nsobczak/CoupeDeFrance/Module Alimentation/Carte_d_alimentation/ReadMe.txt

Alimentation Robot coupe de France : 
100*100 mm
1 exemplaire
Jean-Marc@isen-lille.fr
Arthur.duytschaever@isen.yncrea.fr
