nsobczak/CoupeDeFrance/Module Cerveau/I2C/README.md

# I2C

Protocole de communication entre les différents arduinos.

i2cCommunication.zip est la librairie que nous avons créée.

## i2cCommunication

Il s'agit du dossier qui contient les fichiers de la bibliothèque que nous avons créée pour gérer la communication i2c.

## Tests

Il s'agit du dossier contenant les fichiers ayant servi à réaliser les différents test de la communication entre les arduino réalisée en i2c.
