nsobczak/CoupeDeFrance/Présentations/Présentation 1er semestre/README.md

# Présentation 1er semestre

Dossier contenant les fichiers ayant servi pour notre présentation du 1er semestre.
