nsobczak/CoupeDeFrance/Module Alimentation/Carte_d_alimentation/README.md

# Module alim

Il s'agit du dossier destiné à accueillir tout ce qui concerne la carte d'alimentation.
