nsobczak/CoupeDeFrance/Module Moteur/Software/Asservissement/README.md

# Asservissment

**TODO** :
- Définir ce à quoi sert chaque code
- Supprimer les codes inutiles
