nsobczak/CoupeDeFrance/Module Cerveau/Artificial Intelligence/Ecran/README.md

# Ecran

Il s'agit du dossier du code pour controler l'écran.

## Dossiers

- "BotMenu" est le dossier dans lequel est conservé le code principal de l'écran.
- "Ecran_test" est le dossier dans lequel nous faisons nos tests de l'écran.

## Bibliothèques

### U8glib
Il s'agit de la bibliothèque permettant de controller l'écran.

### m2tklib
Il s'agit de la bibliothèque permettant de controller les menus de l'écran.
