nsobczak/CoupeDeFrance/Module Funny Action/Hardware/PCB_Project/Project Outputs for PCB_Project/README.txt

Coupe de France de Robotique
1 exemplaire
Jean-marc.capron@yncrea.fr
Arthur.duytschaever@isen.yncrea.fr
