nsobczak/CoupeDeFrance/Module Moteur/Software/Caractérisation des moteurs/Récupération codeuse/README.md

# Récupération codeuse

Ce programme compte le nombre de ticks des codeuses d'un des 2 moteurs et les affiche dans le port série à une fréquence fixée.
