nsobczak/CoupeDeFrance/Module Moteur/Software/Archives/README.md

# Archives

This folder contains old programs. These are the one other team used. We may use them to help us.

## CodeOriginal
Il s'agit du code initialement écrit pour le spark core.

## monMain
Il s'agit du code adapté pour un arduino due.
