nsobczak/CoupeDeFrance/Documentation/arduino_emoji.png

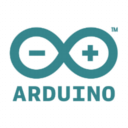
Documentation/arduino_emoji.png
