nsobczak/CoupeDeFrance/Documentation/html/_bot_menu_8cpp__incl.png

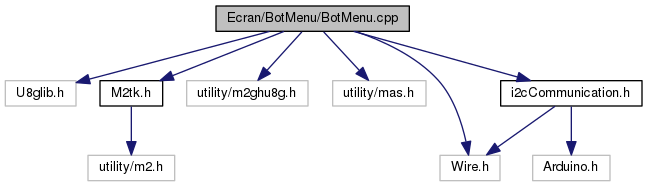
Documentation/html/_bot_menu_8cpp__incl.png
