nsobczak/CoupeDeFrance/Documentation/html/_capteur___i_r__detection__position_8cpp__incl.png

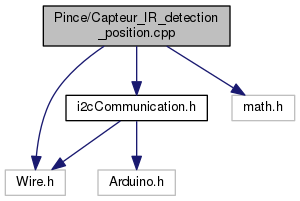
Documentation/html/_capteur___i_r__detection__position_8cpp__incl.png
