nsobczak/CoupeDeFrance/Documentation/html/_ecran_8cpp__incl.png

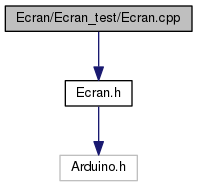
Documentation/html/_ecran_8cpp__incl.png
