nsobczak/CoupeDeFrance/Documentation/html/_ecran_8h__dep__incl.png

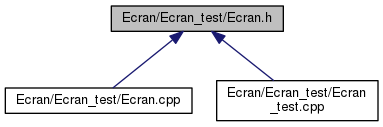
Documentation/html/_ecran_8h__dep__incl.png
