nsobczak/CoupeDeFrance/Documentation/html/_m2tk_8cpp__incl.png

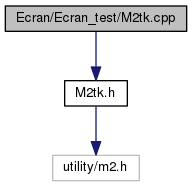
Documentation/html/_m2tk_8cpp__incl.png
