nsobczak/CoupeDeFrance/Documentation/html/_moteur__deplacement_8cpp__incl.png

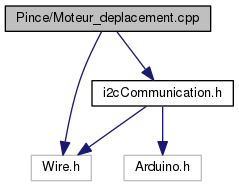
Documentation/html/_moteur__deplacement_8cpp__incl.png
