nsobczak/CoupeDeFrance/Documentation/html/_p_i_d_8cpp__incl.png

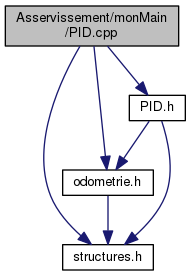
Documentation/html/_p_i_d_8cpp__incl.png
