nsobczak/CoupeDeFrance/Documentation/html/_p_i_d_8h__dep__incl.png

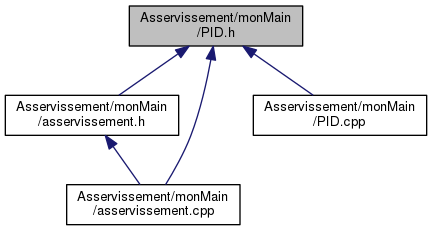
Documentation/html/_p_i_d_8h__dep__incl.png
