nsobczak/CoupeDeFrance/Documentation/html/_p_i_d_8h__incl.png

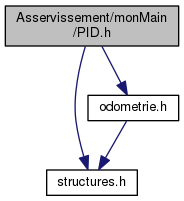
Documentation/html/_p_i_d_8h__incl.png
