nsobczak/CoupeDeFrance/Documentation/html/application_8cpp__incl.png

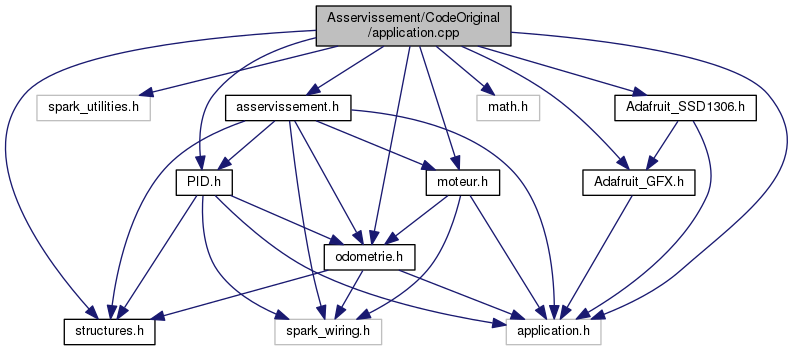
Documentation/html/application_8cpp__incl.png
