nsobczak/CoupeDeFrance/Documentation/html/asservissement_8cpp__incl.png

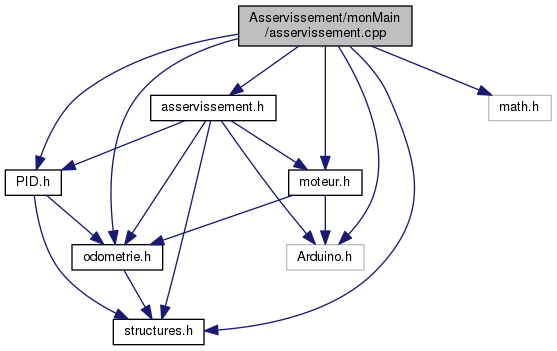
Documentation/html/asservissement_8cpp__incl.png
