nsobczak/CoupeDeFrance/Documentation/html/asservissement_8h__dep__incl.png

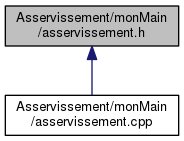
Documentation/html/asservissement_8h__dep__incl.png
