nsobczak/CoupeDeFrance/Documentation/html/asservissement_8h__incl.png

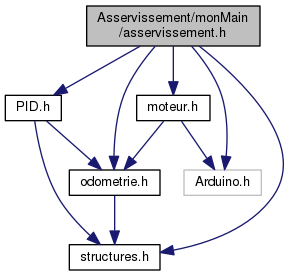
Documentation/html/asservissement_8h__incl.png
