nsobczak/CoupeDeFrance/Documentation/html/class_adafruit___g_f_x__inherit__graph.png

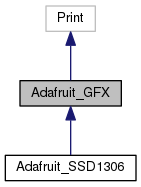
Documentation/html/class_adafruit___g_f_x__inherit__graph.png
