nsobczak/CoupeDeFrance/Documentation/html/dir_7feffd230ef17a4d3f6232c08444e68c_dep.png

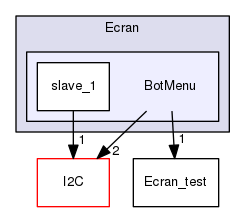
Documentation/html/dir_7feffd230ef17a4d3f6232c08444e68c_dep.png
