nsobczak/CoupeDeFrance/Documentation/html/dir_239d87ce9101b63f8d944565a49246da_dep.png

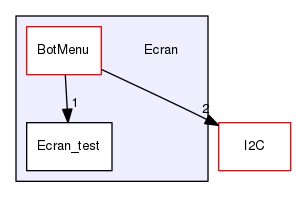
Documentation/html/dir_239d87ce9101b63f8d944565a49246da_dep.png
