nsobczak/CoupeDeFrance/Documentation/html/dir_b54d3ecc02a1dadce9e3ca1df9bb6ecc_dep.png

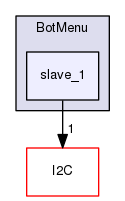
Documentation/html/dir_b54d3ecc02a1dadce9e3ca1df9bb6ecc_dep.png
