nsobczak/CoupeDeFrance/Documentation/html/i2c_communication_8cpp__incl.png

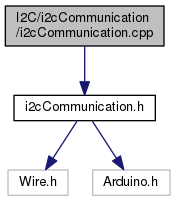
Documentation/html/i2c_communication_8cpp__incl.png
