nsobczak/CoupeDeFrance/Documentation/html/i2c_communication_8h__incl.png

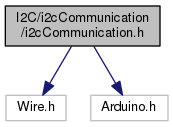
Documentation/html/i2c_communication_8h__incl.png
