nsobczak/CoupeDeFrance/Documentation/html/mon_main_8cpp__incl.png

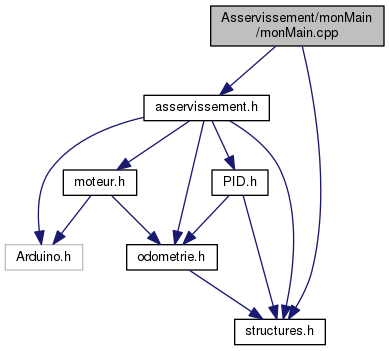
Documentation/html/mon_main_8cpp__incl.png
