nsobczak/CoupeDeFrance/Documentation/html/moteur_8cpp__incl.png

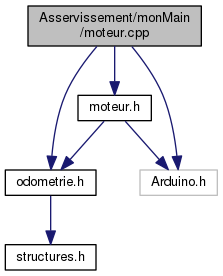
Documentation/html/moteur_8cpp__incl.png
