nsobczak/CoupeDeFrance/Documentation/html/moteur_8h__incl.png

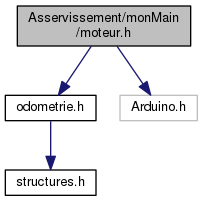
Documentation/html/moteur_8h__incl.png
