nsobczak/CoupeDeFrance/Documentation/html/newlib__stubs_8cpp__incl.png

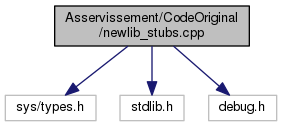
Documentation/html/newlib__stubs_8cpp__incl.png
