nsobczak/CoupeDeFrance/Documentation/html/odometrie_8cpp__incl.png

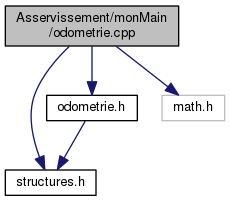
Documentation/html/odometrie_8cpp__incl.png
