nsobczak/CoupeDeFrance/Documentation/html/odometrie_8h__dep__incl.png

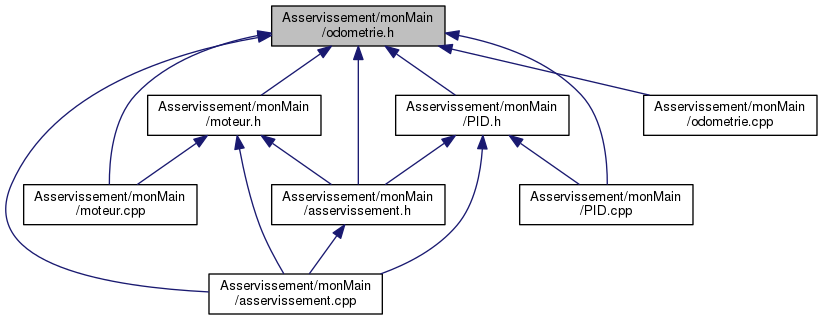
Documentation/html/odometrie_8h__dep__incl.png
