nsobczak/CoupeDeFrance/Documentation/html/odometrie_8h__incl.png

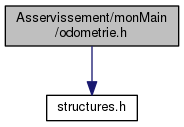
Documentation/html/odometrie_8h__incl.png
