nsobczak/CoupeDeFrance/Documentation/html/slave__1_8cpp__incl.png

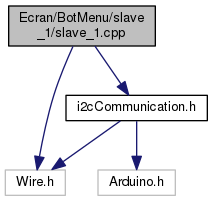
Documentation/html/slave__1_8cpp__incl.png
