nsobczak/CoupeDeFrance/Documentation/html/structures_8h__dep__incl.png

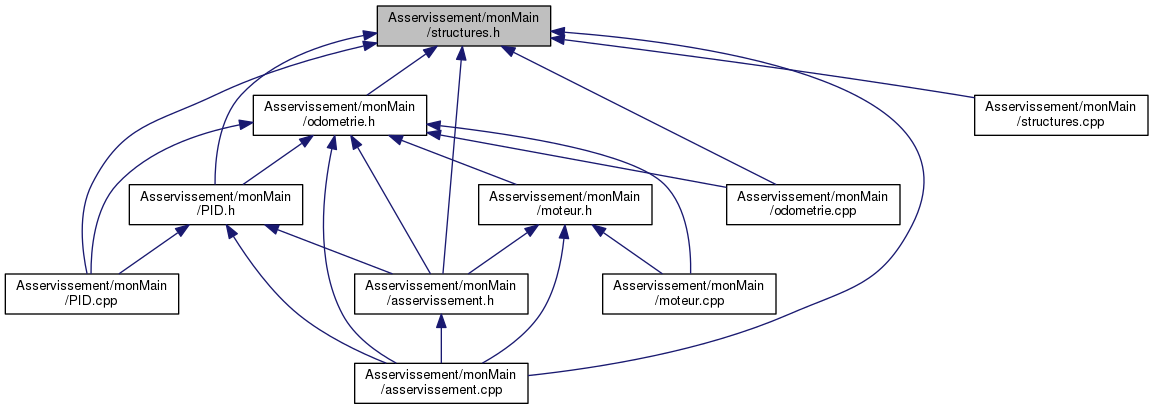
Documentation/html/structures_8h__dep__incl.png
