nsobczak/CoupeDeFrance/Documentation/html/usb__desc_8cpp__incl.png

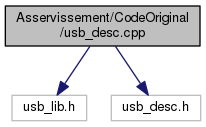
Documentation/html/usb__desc_8cpp__incl.png
