nsobczak/CoupeDeFrance/Documentation/html/usb__istr_8cpp__incl.png

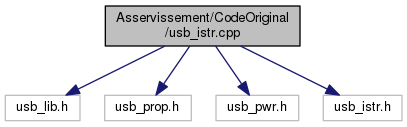
Documentation/html/usb__istr_8cpp__incl.png
