nsobczak/CoupeDeFrance/Documentation/html/wifi__credentials__reader_8cpp__incl.png

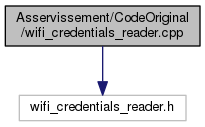
Documentation/html/wifi__credentials__reader_8cpp__incl.png
