nsobczak/CoupeDeFrance/Documentation/schéma global.png

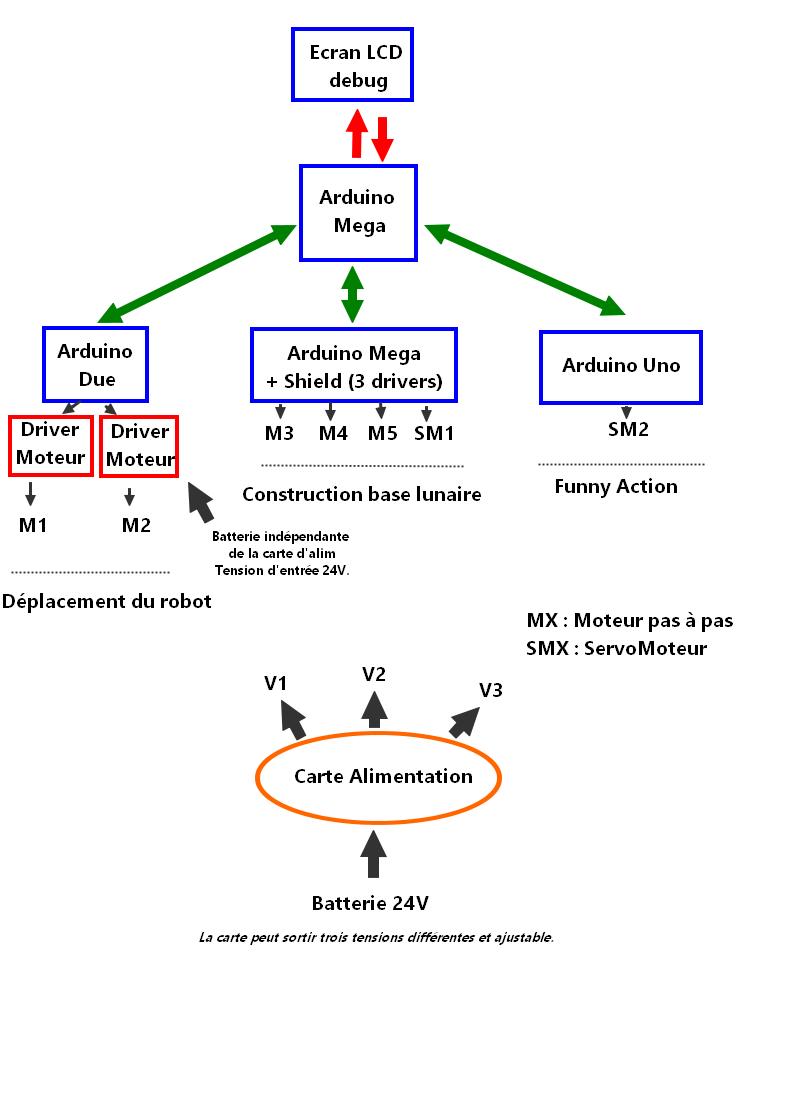
Documentation/schéma global.png
