nsobczak/CoupeDeFrance/Module Cerveau/Artificial Intelligence/AI_uml/AI_UML.png

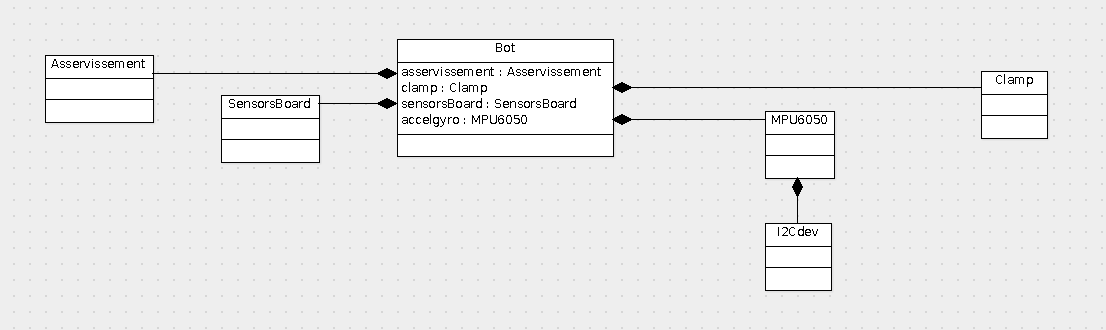
Module Cerveau/Artificial Intelligence/AI_uml/AI_UML.png
