nsobczak/CoupeDeFrance/Module Cerveau/Artificial Intelligence/Menu_Plans/Menu Plans.png

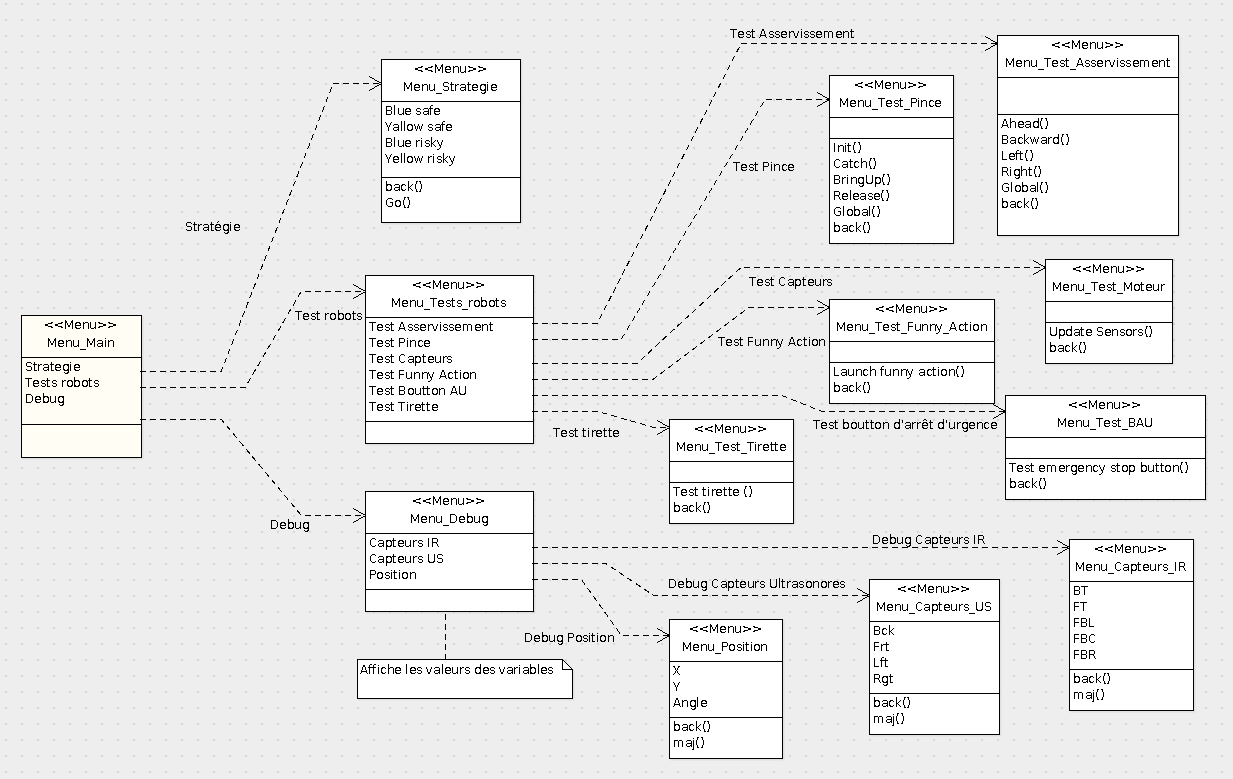
Module Cerveau/Artificial Intelligence/Menu_Plans/Menu Plans.png
