nsobczak/CoupeDeFrance/Média/Funny action (2).JPG

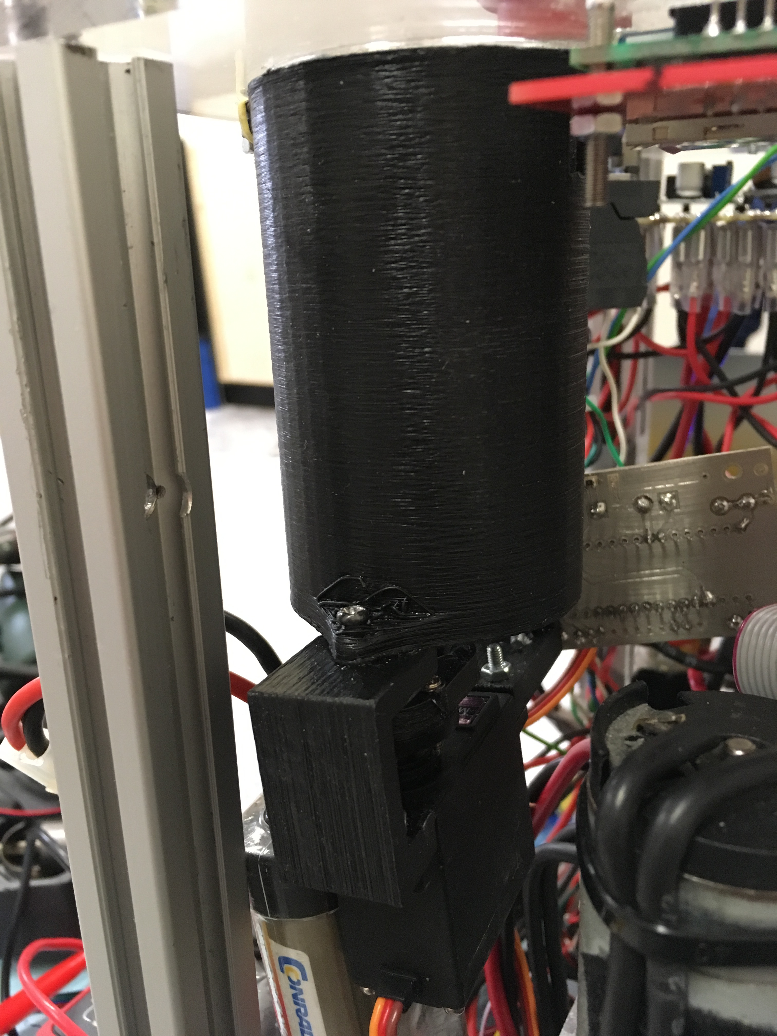
Média/Funny action (2).JPG
