nsobczak/CoupeDeFrance/Média/Funny action.JPG

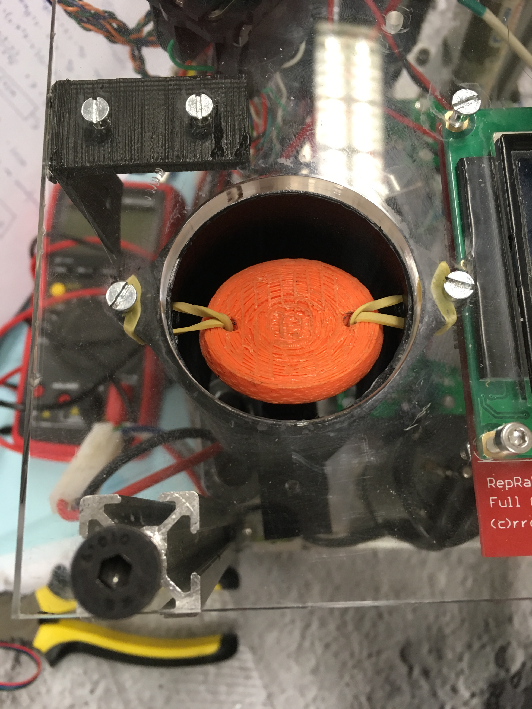
Média/Funny action.JPG
