nsobczak/CoupeDeFrance/Média/IMG_20161012_150901.jpg

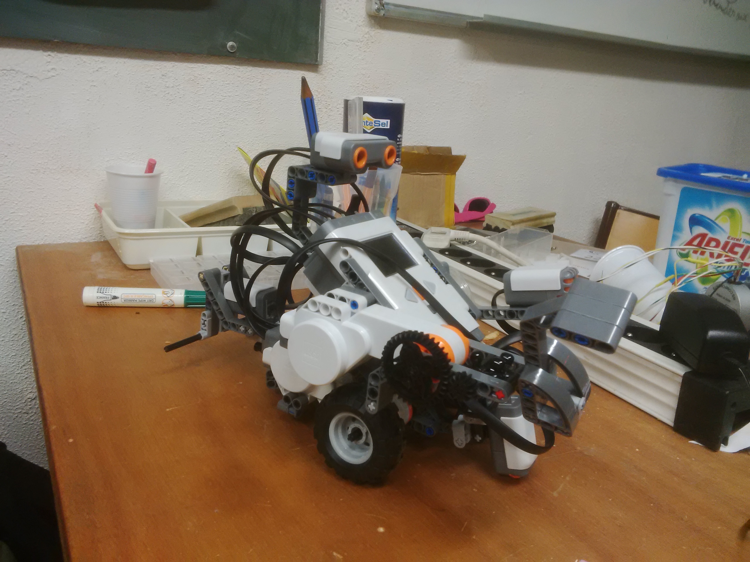
Média/IMG_20161012_150901.jpg
