nsobczak/CoupeDeFrance/Média/IMG_20161215_091232.jpg

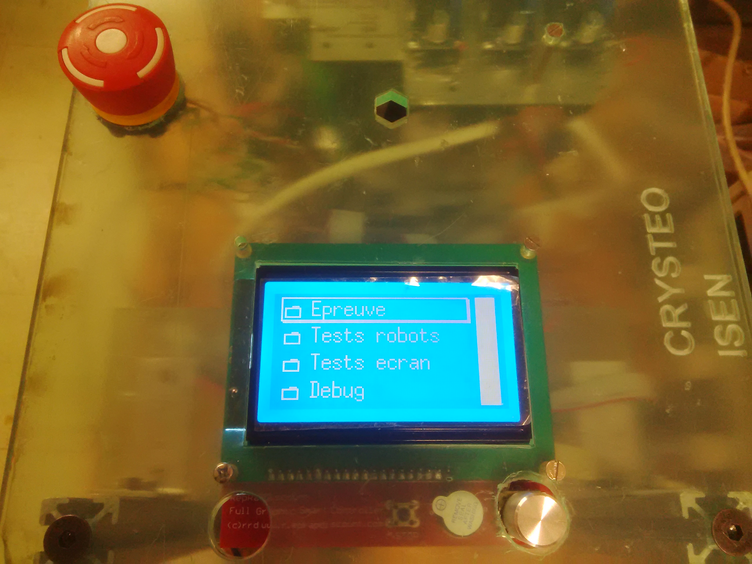
Média/IMG_20161215_091232.jpg
