nsobczak/CoupeDeFrance/Média/Photo_découpe_laser.PNG

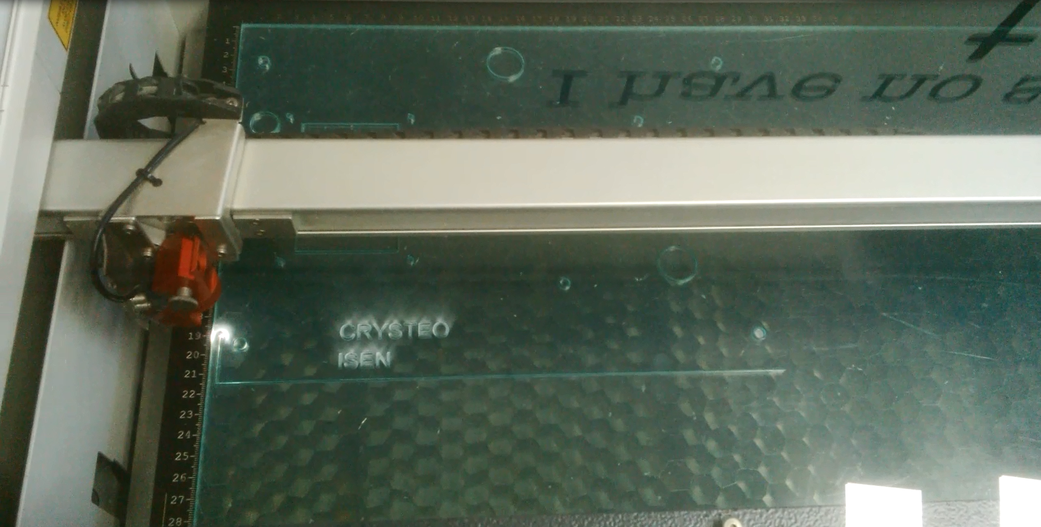
Média/Photo_découpe_laser.PNG
