nsobczak/CoupeDeFrance/Média/Photo_grand_robot_01.PNG

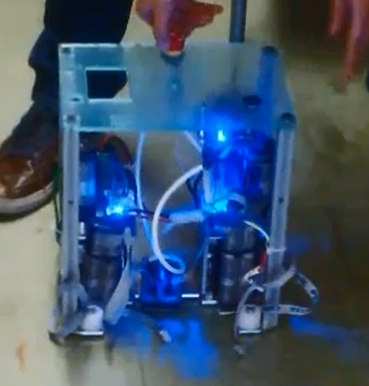
Média/Photo_grand_robot_01.PNG
