nsobczak/CoupeDeFrance/Média/Pince.JPG

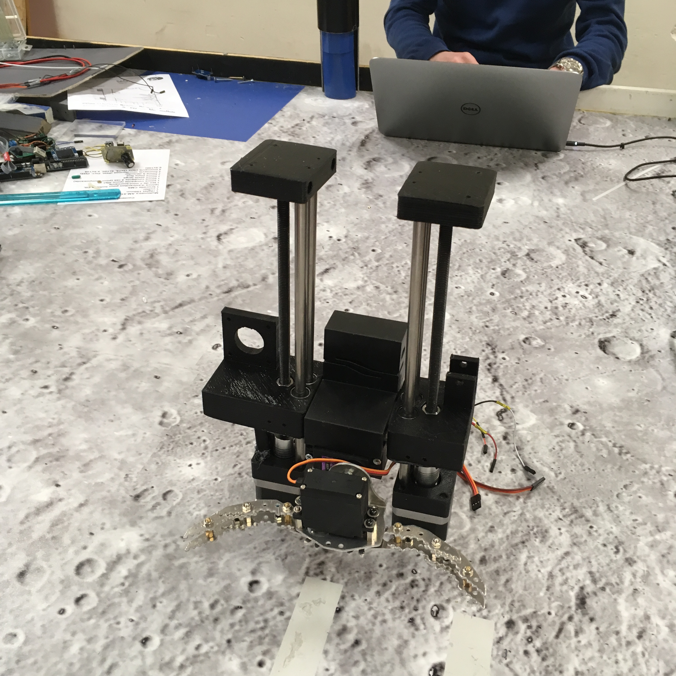
Média/Pince.JPG
