nsobczak/CoupeDeFrance/Média/Robot (2).JPG

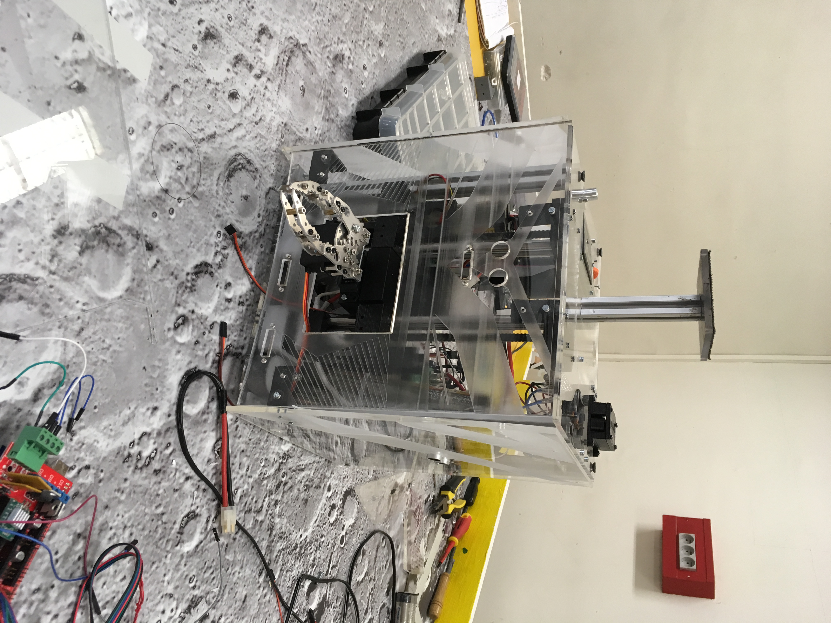
Média/Robot (2).JPG
