nsobczak/CoupeDeFrance/Média/Robot (3).JPG

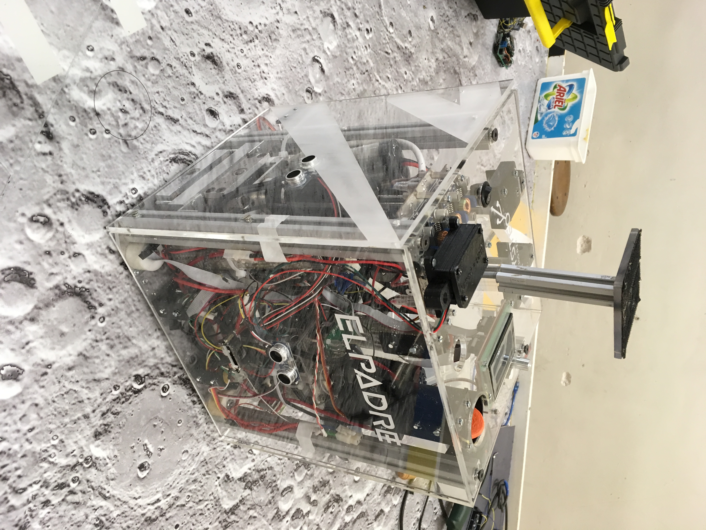
Média/Robot (3).JPG
