nsobczak/CoupeDeFrance/Média/Robot (4).JPG

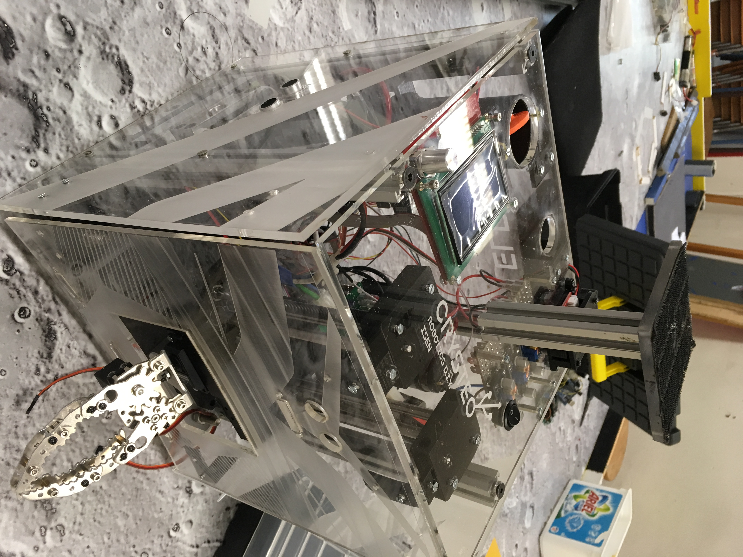
Média/Robot (4).JPG
