nsobczak/CoupeDeFrance/Média/Robot.JPG

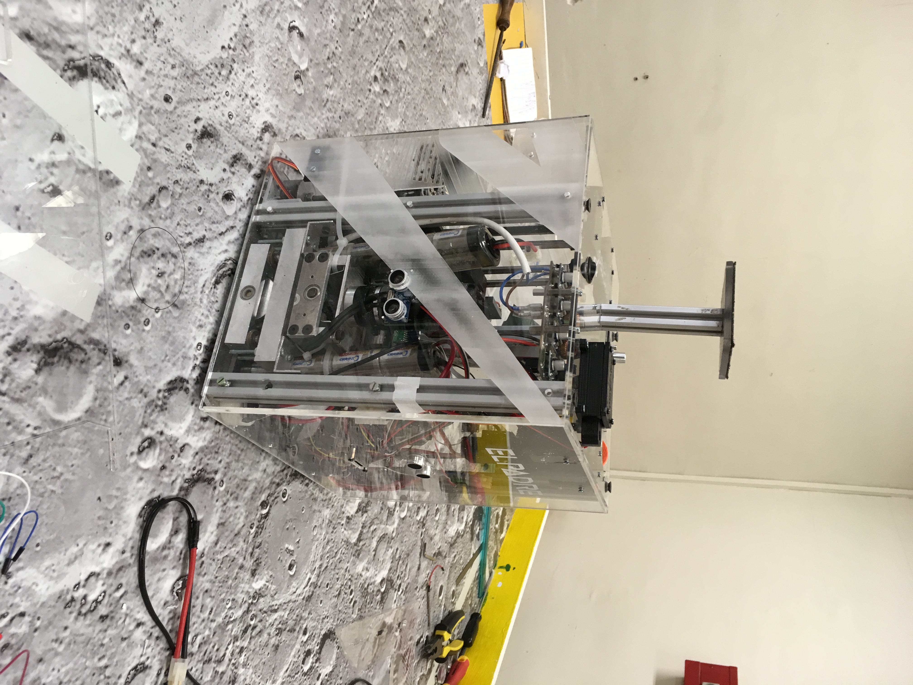
Média/Robot.JPG
