nsobczak/CoupeDeFrance/Présentations/Présentation 2eme semestre/Images/capteur-distance-ir-sharp-gp2yoa21-10cm-80cm-5.jpg

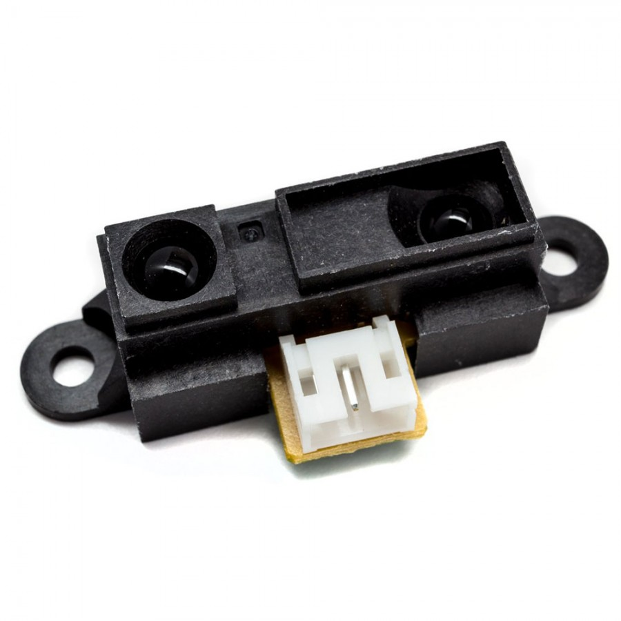
Présentations/Présentation 2eme semestre/Images/capteur-distance-ir-sharp-gp2yoa21-10cm-80cm-5.jpg
