nsobczak/CoupeDeFrance/Présentations/Présentation 2eme semestre/Images/Ecran.jpg

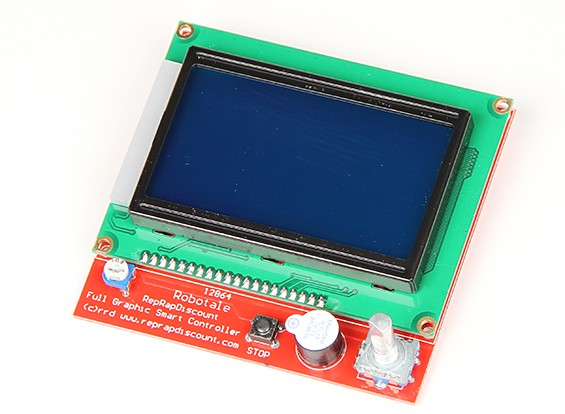
Présentations/Présentation 2eme semestre/Images/Ecran.jpg
