nsobczak/CoupeDeFrance/Présentations/Présentation 2eme semestre/Images/hc-sr04_capteur_de_distance_par_ultrason.jpg

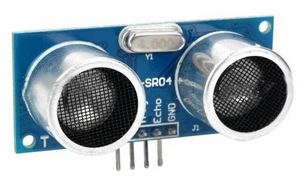
Présentations/Présentation 2eme semestre/Images/hc-sr04_capteur_de_distance_par_ultrason.jpg
