nsobczak/CoupeDeFrance/Présentations/Présentation 2eme semestre/Images/Schéma global.png

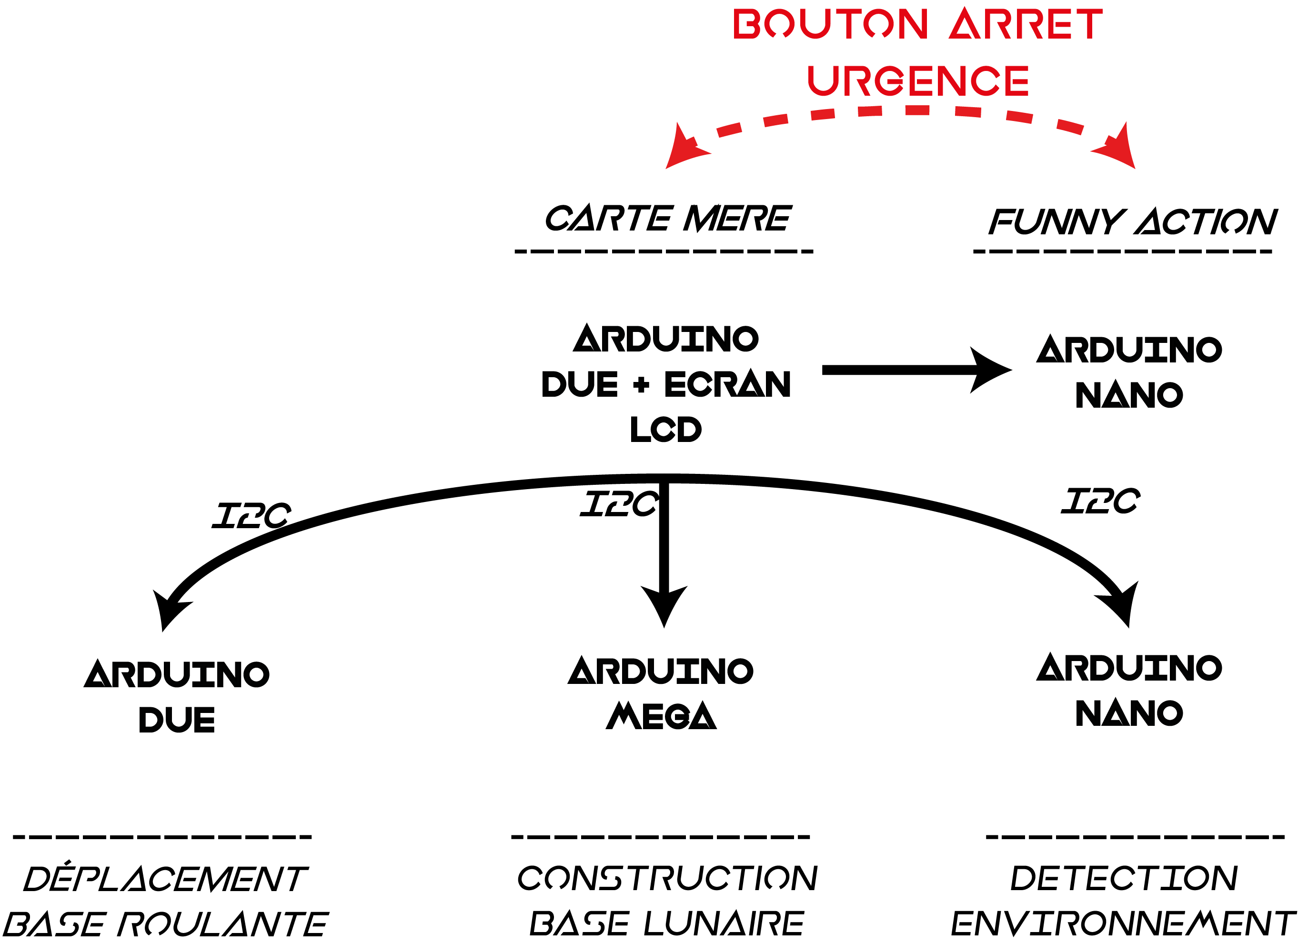
Présentations/Présentation 2eme semestre/Images/Schéma global.png
