nsobczak/CoupeDeFrance/Présentations/Présentation 2eme semestre/Images/Yncrea_BM_ISEN-Lille_Blanc-horizontal.png

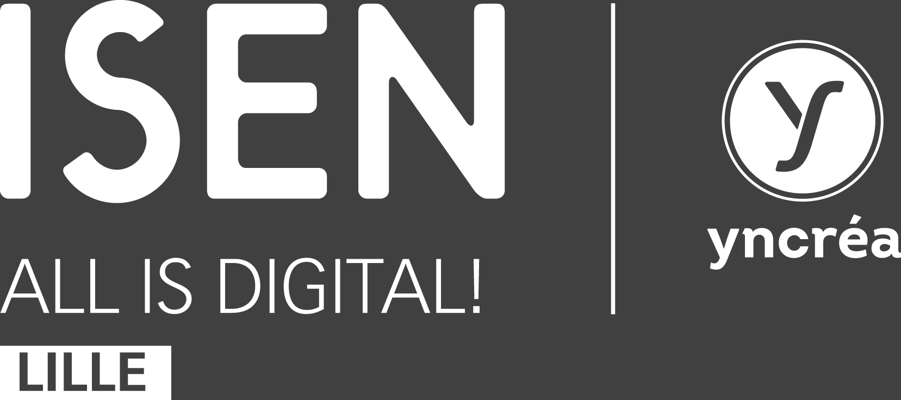
Présentations/Présentation 2eme semestre/Images/Yncrea_BM_ISEN-Lille_Blanc-horizontal.png
