nsobczak/CoupeDeFrance/Présentations/Présentation 2eme semestre/Images/Yncrea_BM_ISEN-Lille_horizontal fond transparent.png

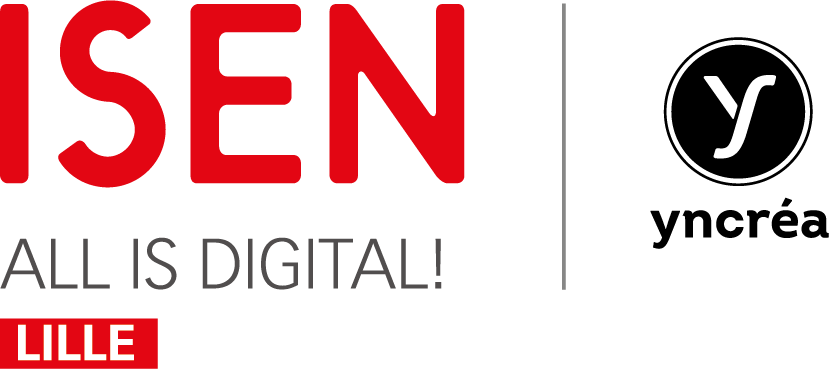
Présentations/Présentation 2eme semestre/Images/Yncrea_BM_ISEN-Lille_horizontal fond transparent.png
