nsobczak/CoupeDeFrance/Présentations/Présentation 2eme semestre/Poster/3051793895_1_16_avUZXeAR.jpg

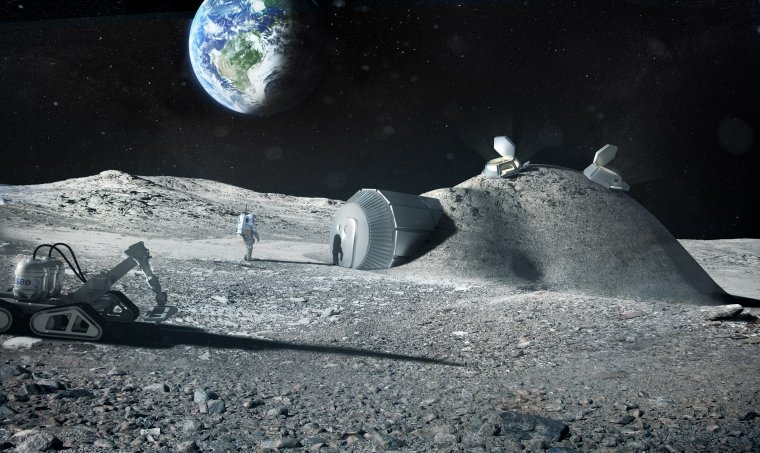
Présentations/Présentation 2eme semestre/Poster/3051793895_1_16_avUZXeAR.jpg
