nsobczak/CoupeDeFrance/SolidWorks/El Padre/Base_roulante/Actionneur/herculex_DRS0101.jpg

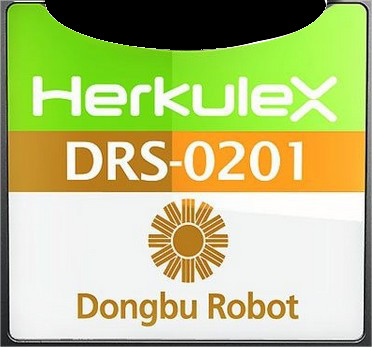
SolidWorks/El Padre/Base_roulante/Actionneur/herculex_DRS0101.jpg
