nsobczak/CoupeDeFrance/SolidWorks/El Padre/Base_roulante/Claps/AntiClapsFinal/Assembly anti claps 2.SLDASM

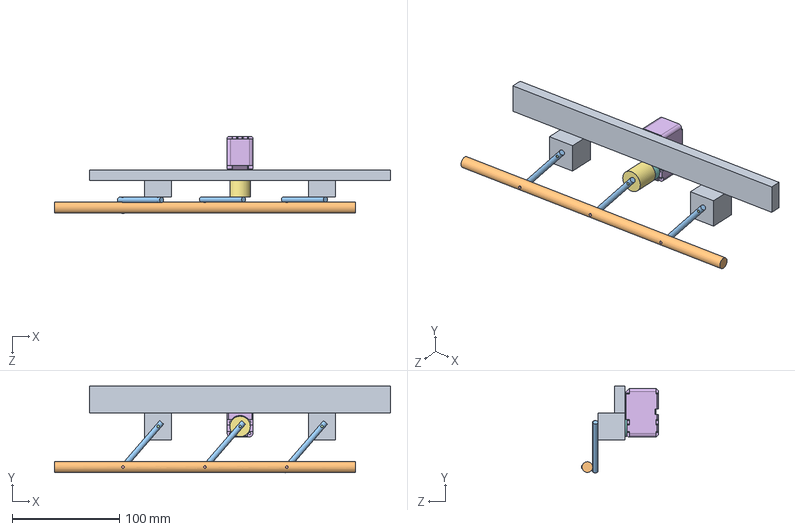
[picture p97: CAD file, 2017-02-13]
SolidWorks/El Padre/Base_roulante/Claps/AntiClapsFinal/Assembly anti claps 2.SLDASM
312.7 x 80.7 x 71.3 mm
support
tige
tigeSupport x 3
Vis 1 x 3
Vis 2 x 3
herkulex_DRS0101_servomoteur
RenfortServomoteur
roulementHerkulex
