nsobczak/CoupeDeFrance/SolidWorks/El Padre/Base_roulante/cristeo/Assemblage canon - acroche-1.STL

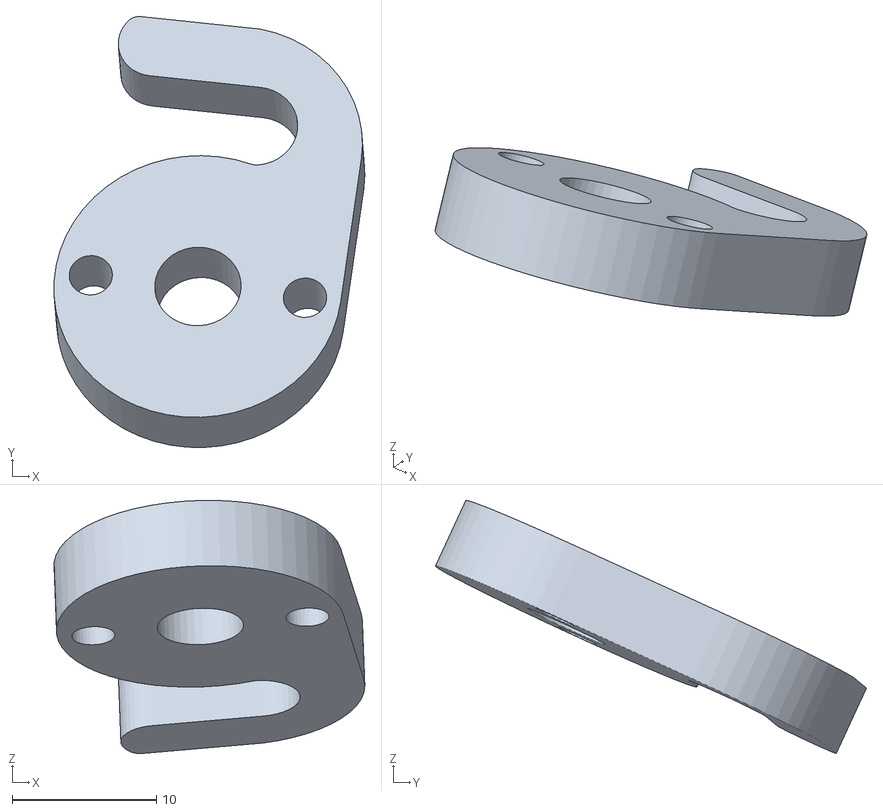
[picture p98: CAD file, 2017-04-03]
SolidWorks/El Padre/Base_roulante/cristeo/Assemblage canon - acroche-1.STL
21.6 x 29.9 x 17.6
