nsobczak/CoupeDeFrance/SolidWorks/El Padre/isen robot 2016-17/SUPPORT DU MILIEU.SLDASM

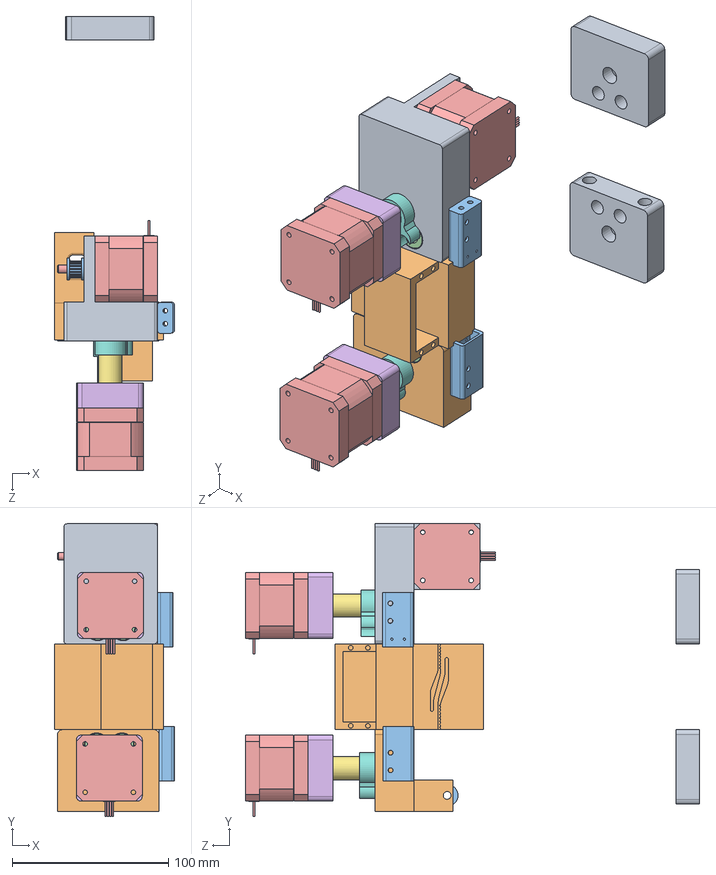
[picture p99: CAD file, 2017-04-14]
SolidWorks/El Padre/isen robot 2016-17/SUPPORT DU MILIEU.SLDASM
77.0 x 188.1 x 291.0 mm
support-milieu_droite
support-milieu_gauche
poulie pour courroie x 2
roulement lineaire M8-24 x 6
moteur NEMA 17-40mm x 3
support8moteur x 2
Adaptateur x 2
PINCE_ANTI_WOOBLE x 2
support_haut x 2
ENSEMBLE CHARIOT DEPLACEMENT_1
support_fin_de_coursz x 2
