nsobczak/CoupeDeFrance/SolidWorks/El Padre/Base_roulante/cristeo/Assemblage canon - support moteur 2-1.STL

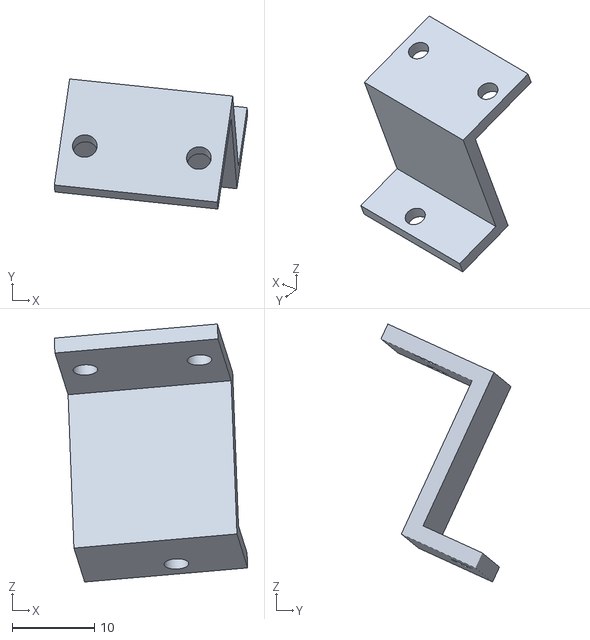
[picture p100: CAD file, 2017-04-03]
SolidWorks/El Padre/Base_roulante/cristeo/Assemblage canon - support moteur 2-1.STL
23.5 x 15.8 x 31.4
