nsobczak/CoupeDeFrance/SolidWorks/El Padre/Base_roulante/cristeo/Assemblage canon - support servo moteur 1-1.STL

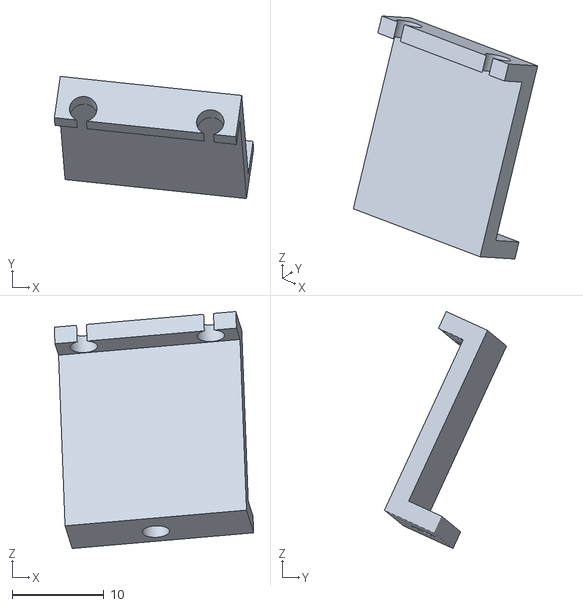
[picture p101: CAD file, 2017-04-03]
SolidWorks/El Padre/Base_roulante/cristeo/Assemblage canon - support servo moteur 1-1.STL
21.8 x 13.3 x 25.9
