nsobczak/CoupeDeFrance/SolidWorks/El Padre/isen robot 2016-17/Pince/Assemblage2.SLDPRT

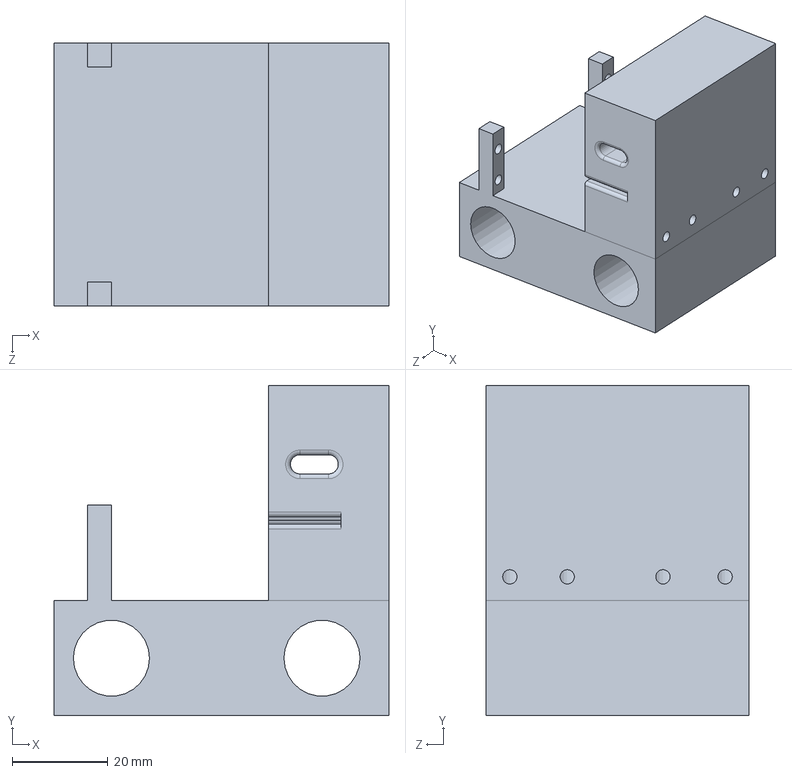
[picture p102: CAD file, 2017-02-13]
SolidWorks/El Padre/isen robot 2016-17/Pince/Assemblage2.SLDPRT
70.0 x 69.0 x 55.0 mm
