nsobczak/CoupeDeFrance/SolidWorks/El Padre/Base_roulante/Base du robot/capteur_ultrasonore.SLDASM

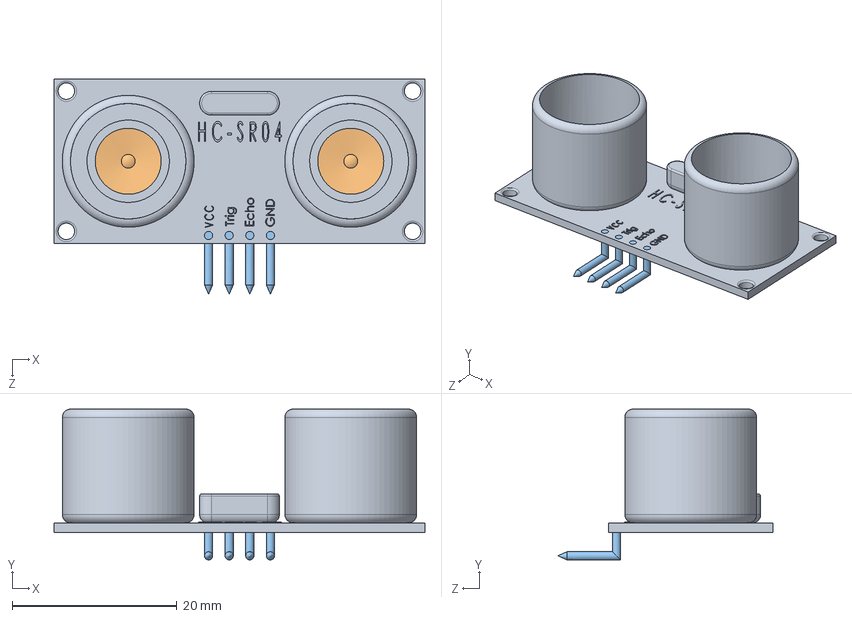
[picture p103: CAD file, 2017-03-29]
SolidWorks/El Padre/Base_roulante/Base du robot/capteur_ultrasonore.SLDASM
45.0 x 18.3 x 26.1 mm
UltraSonic
pin header x 4
