nsobczak/CoupeDeFrance/SolidWorks/El Padre/Base_roulante/cristeo/Assemblage canon - servo moteur-1.STL

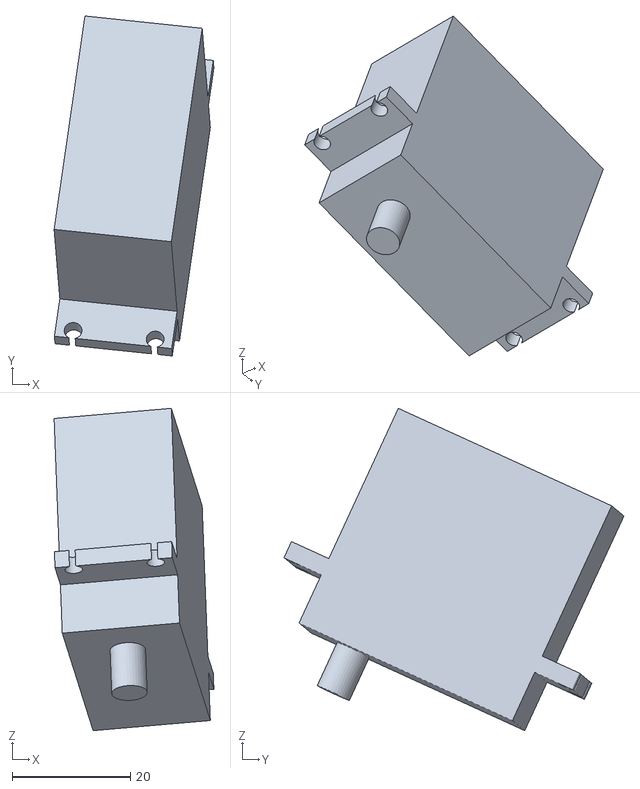
[picture p104: CAD file, 2017-04-03]
SolidWorks/El Padre/Base_roulante/cristeo/Assemblage canon - servo moteur-1.STL
27.0 x 57.5 x 54.5
