nsobczak/CoupeDeFrance/SolidWorks/El Padre/Base_roulante/Base du robot/Ultrasonic.SLDASM

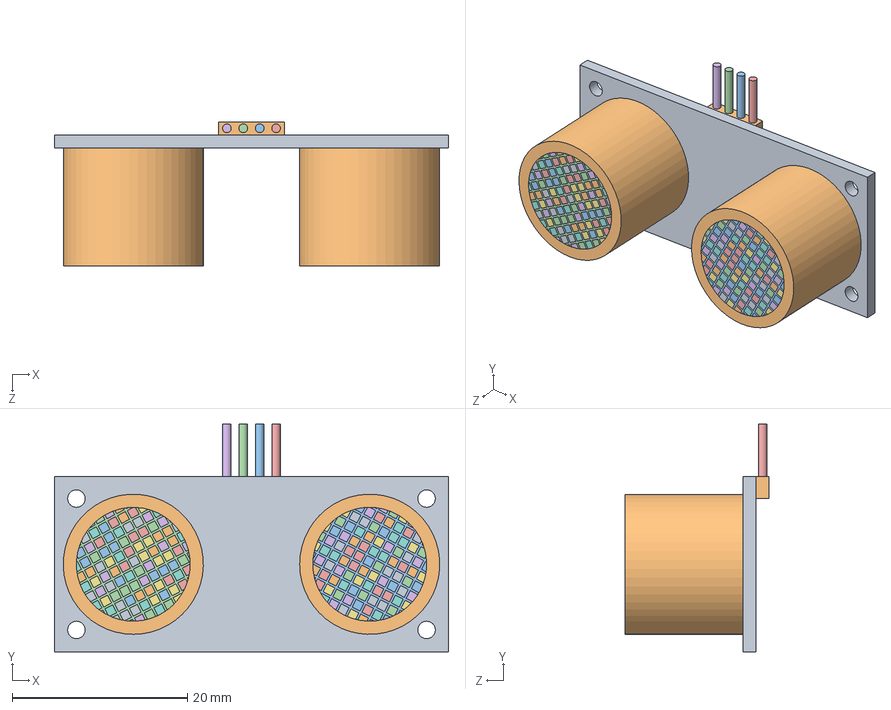
[picture p105: CAD file, 2017-03-29]
SolidWorks/El Padre/Base_roulante/Base du robot/Ultrasonic.SLDASM
45.0 x 26.0 x 16.5 mm
Ultrasonic1
Ultrasonic2
Ultrasonic3
Ultrasonic4
Ultrasonic5
Ultrasonic6
Ultrasonic7
Ultrasonic8
Ultrasonic9
Ultrasonic10
Ultrasonic11
Ultrasonic12
Ultrasonic13
Ultrasonic14
Ultrasonic15
Ultrasonic16
Ultrasonic17
Ultrasonic18
Ultrasonic19
Ultrasonic20
Ultrasonic21
Ultrasonic22
Ultrasonic23
Ultrasonic24
Ultrasonic25
Ultrasonic26
Ultrasonic27
Ultrasonic28
Ultrasonic29
Ultrasonic30
Ultrasonic31
Ultrasonic32
Ultrasonic33
Ultrasonic34
Ultrasonic35
Ultrasonic36
Ultrasonic37
Ultrasonic38
Ultrasonic39
Ultrasonic40
Ultrasonic41
Ultrasonic42
Ultrasonic43
Ultrasonic44
Ultrasonic45
Ultrasonic46
Ultrasonic47
Ultrasonic48
Ultrasonic49
Ultrasonic50
Ultrasonic51
Ultrasonic52
Ultrasonic53
Ultrasonic54
Ultrasonic55
Ultrasonic56
Ultrasonic57
Ultrasonic58
Ultrasonic59
Ultrasonic60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
