nsobczak/CoupeDeFrance/SolidWorks/El Padre/Base_roulante/Bloc moteur/bloc moteur.SLDASM

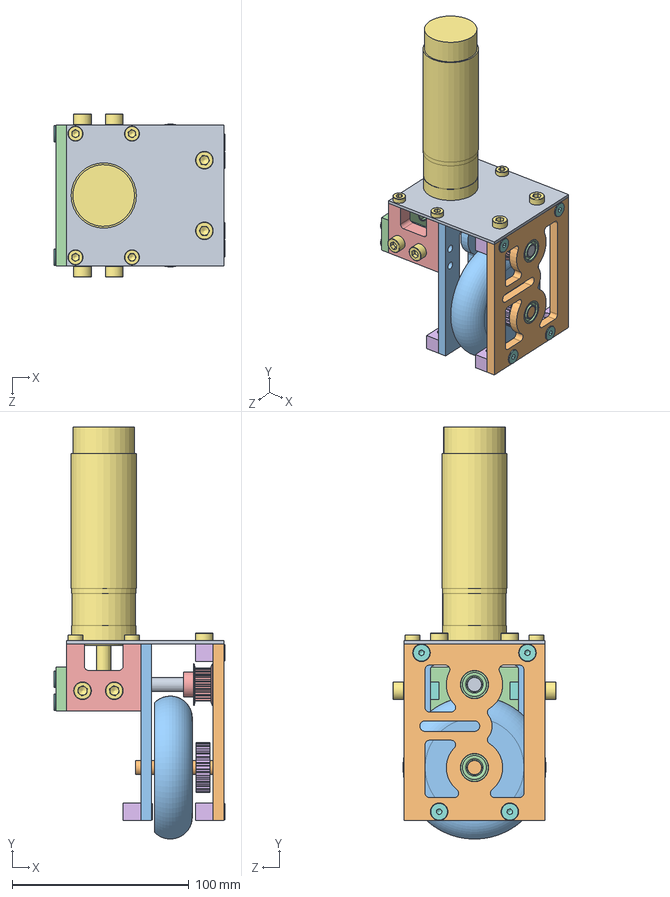
[picture p106: CAD file, 2017-02-13]
SolidWorks/El Padre/Base_roulante/Bloc moteur/bloc moteur.SLDASM
96.7 x 233.3 x 92.5 mm
support moteur
support central
support inter
support exter
RENFORT x 2
fix carre x 3
moteur
support coulisse x 2
axe inter
axe roue
roue
angular contact ball bearing_68_iso x 5
poulie 20 dents
poulie 30 dents
socket head cap screw_iso x 10
socket countersunk head screw_iso x 9
