nsobczak/CoupeDeFrance/SolidWorks/El Padre/Base_roulante/cristeo/Assemblage canon - la boule-1.STL

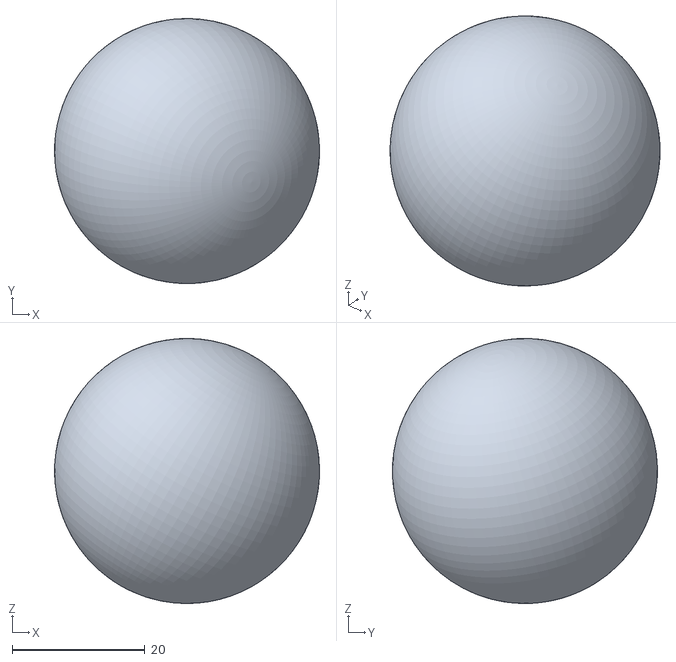
[picture p107: CAD file, 2017-04-03]
SolidWorks/El Padre/Base_roulante/cristeo/Assemblage canon - la boule-1.STL
40.0 x 40.0 x 40.0
