nsobczak/CoupeDeFrance/SolidWorks/El Padre/isen robot 2016-17/MTOT.SLDASM

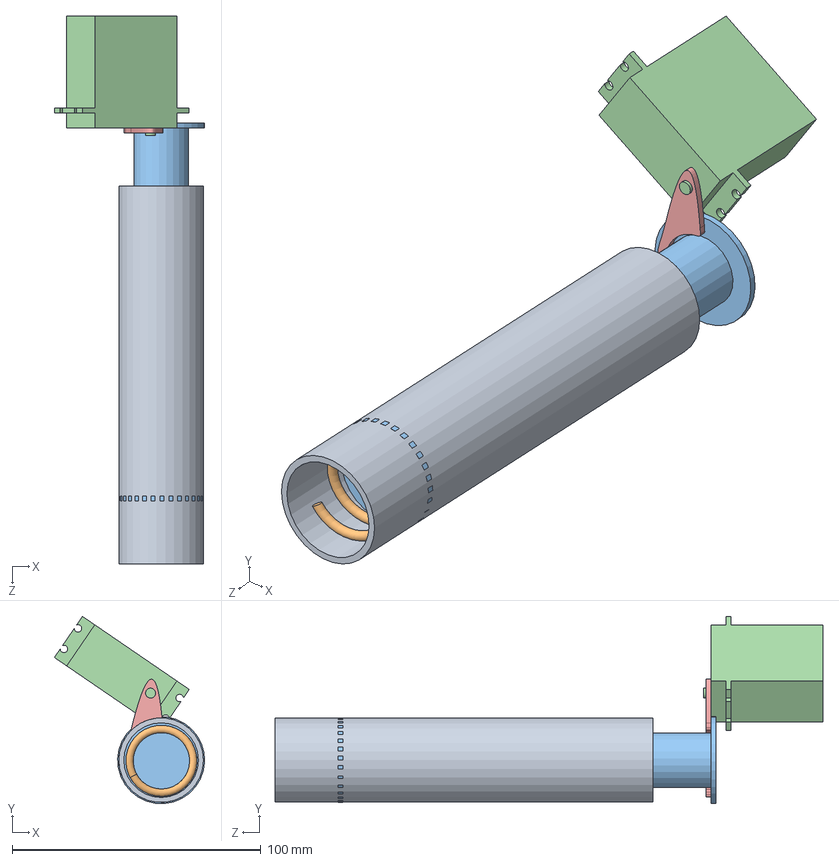
[picture p108: CAD file, 2017-02-13]
SolidWorks/El Padre/isen robot 2016-17/MTOT.SLDASM
60.4 x 75.2 x 220.2 mm
M1
M2
M3
M4
M5
