nsobczak/CoupeDeFrance/SolidWorks/El Padre/isen robot 2016-17/Pince/Assemblage11.SLDASM

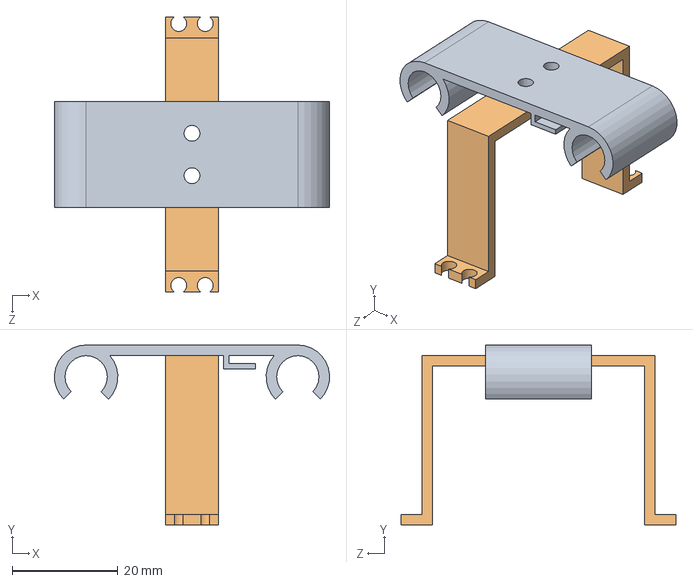
[picture p110: CAD file, 2017-02-13]
SolidWorks/El Padre/isen robot 2016-17/Pince/Assemblage11.SLDASM
52.0 x 34.0 x 52.0 mm
Pièce11
Pièce12
