nsobczak/CoupeDeFrance/SolidWorks/El Padre/Base_roulante/cristeo/Assemblage canon.SLDASM

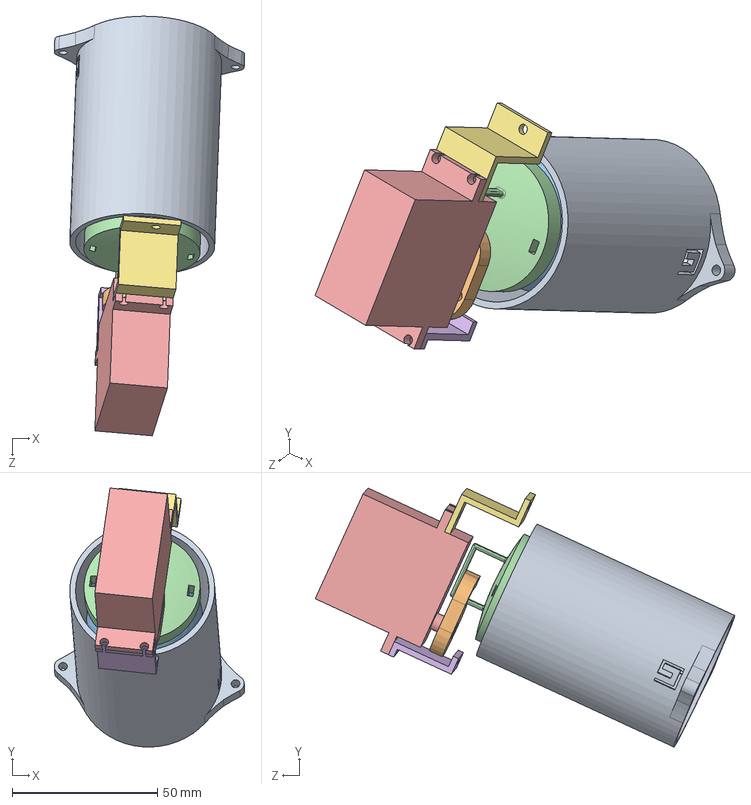
[picture p111: CAD file, 2017-04-03]
SolidWorks/El Padre/Base_roulante/cristeo/Assemblage canon.SLDASM
65.6 x 89.3 x 144.6 mm
canon
acroche
la boule
lanceur
servo moteur
support servo moteur 1
support moteur 2
