nsobczak/CoupeDeFrance/SolidWorks/El Padre/Base_roulante/Base du robot/Base_grand_robot_V2 (2).SLDASM

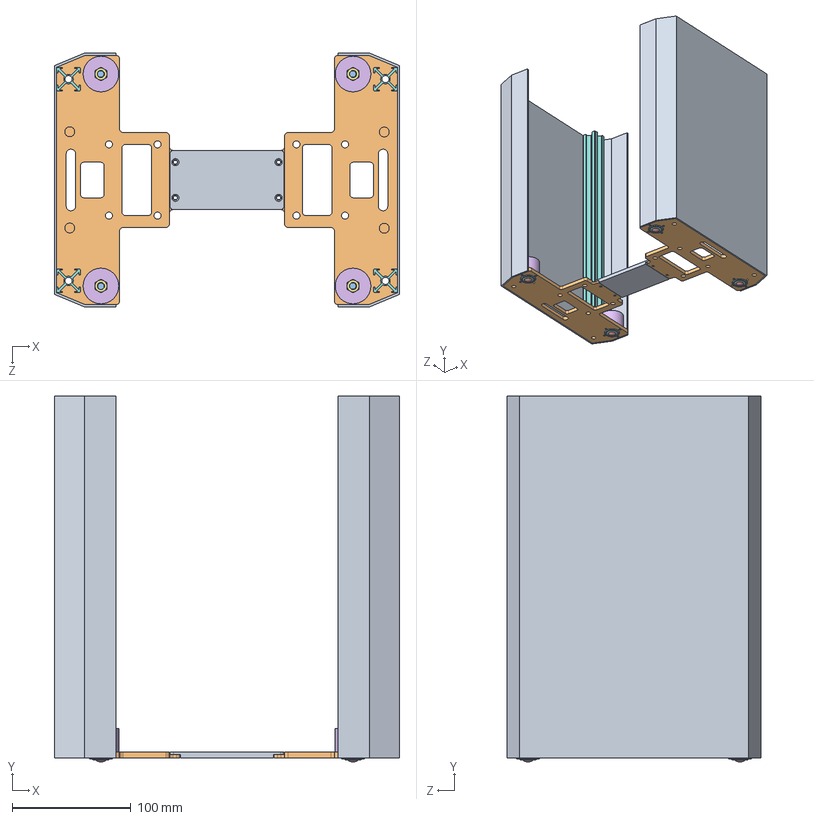
[picture p112: CAD file, 2017-02-13]
SolidWorks/El Padre/Base_roulante/Base du robot/Base_grand_robot_V2 (2).SLDASM
291.0 x 308.4 x 214.0 mm
Base_centre
base_modifiee x 2
contour_roulement x 4
porte_bille x 4
bille x 4
Support_bille_appui x 4
hex nut style 1 gradeab_iso x 4
Profile20O6_V2 x 4
Contour_Socle_V2 x 2
