nsobczak/CoupeDeFrance/SolidWorks/El Padre/Base_roulante/Bloc moteur/maintientcodeuseroulement.SLDPRT

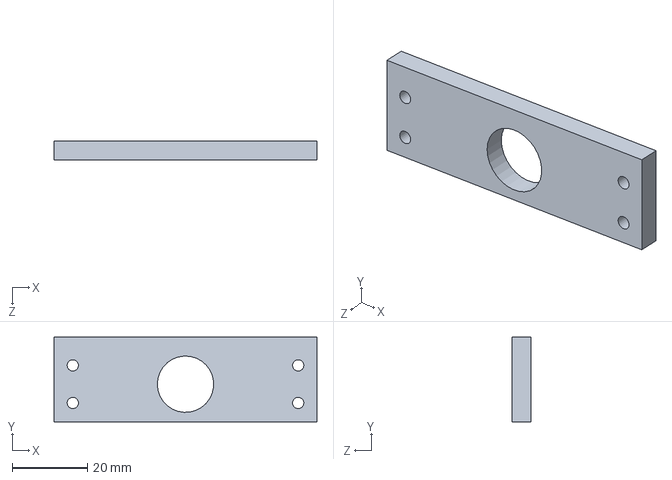
[picture p113: CAD file, 2017-02-13]
SolidWorks/El Padre/Base_roulante/Bloc moteur/maintientcodeuseroulement.SLDPRT
70.0 x 22.5 x 5.00 mm
