nsobczak/CoupeDeFrance/SolidWorks/El Padre/isen robot 2016-17/Assemblage_finale.SLDASM

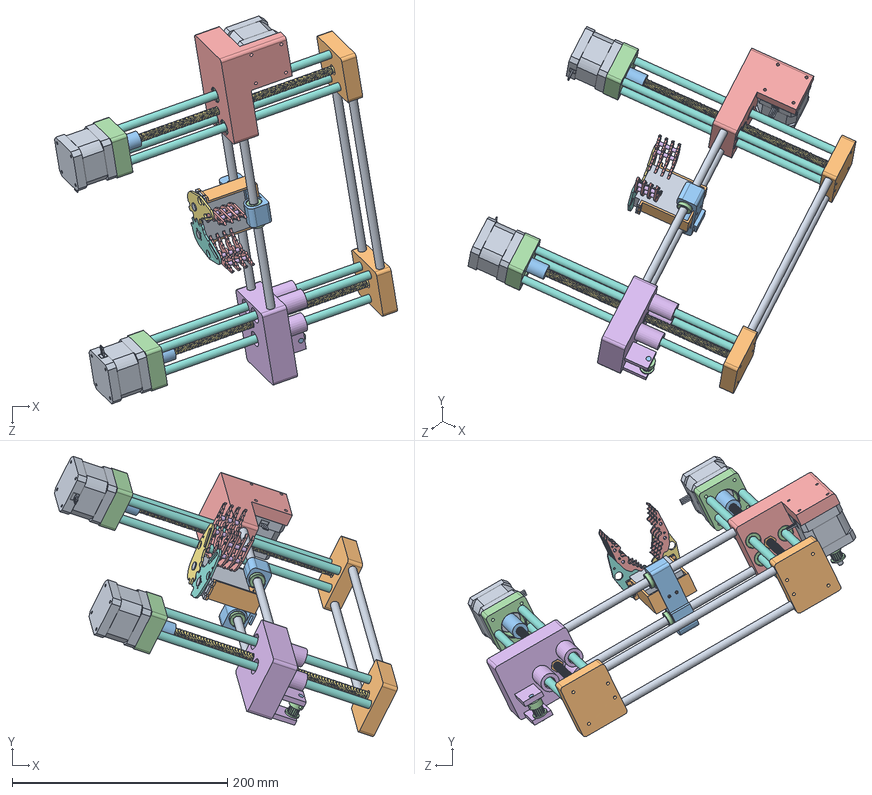
[picture p114: CAD file, 2017-02-13]
SolidWorks/El Padre/isen robot 2016-17/Assemblage_finale.SLDASM
318.8 x 260.5 x 360.5 mm
moteur NEMA 17-40mm x 3
support_haut x 2
Adaptateur x 2
support8moteur x 2
support-milieu_droite
support-milieu_gauche
tige filetee M8 x 2
tige lisse 8 x 6
e6 x 4
ecrou socket x 2
TIGE ROULLEMENT
LM8UU x 8
piece pince x 8
Pièce2 x 12
Pièce4
Pièce3
Pièce5
Pièce12
Pièce22
poulie pour courroie x 2
