nsobczak/CoupeDeFrance/SolidWorks/El Padre/Base_roulante/Actionneur/roulementHerkulex.SLDPRT

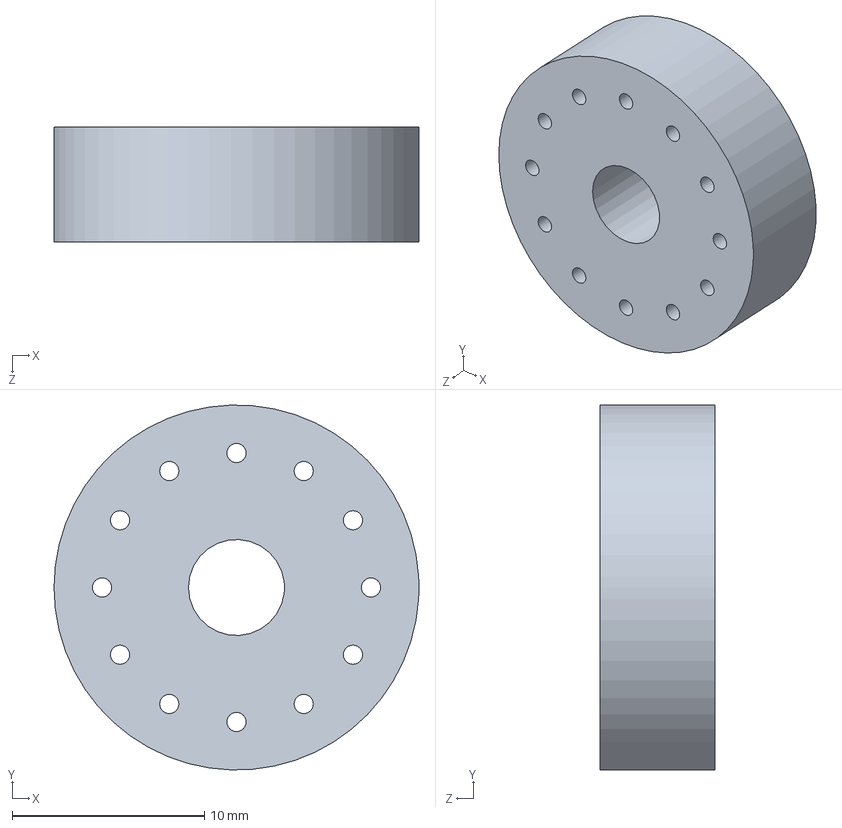
[picture p115: CAD file, 2017-02-13]
SolidWorks/El Padre/Base_roulante/Actionneur/roulementHerkulex.SLDPRT
19.0 x 19.0 x 6.00 mm
