nsobczak/CoupeDeFrance/SolidWorks/El Padre/Base_roulante/Assemblage popcorn/Pièces/Bac/Bac ping pong.SLDPRT

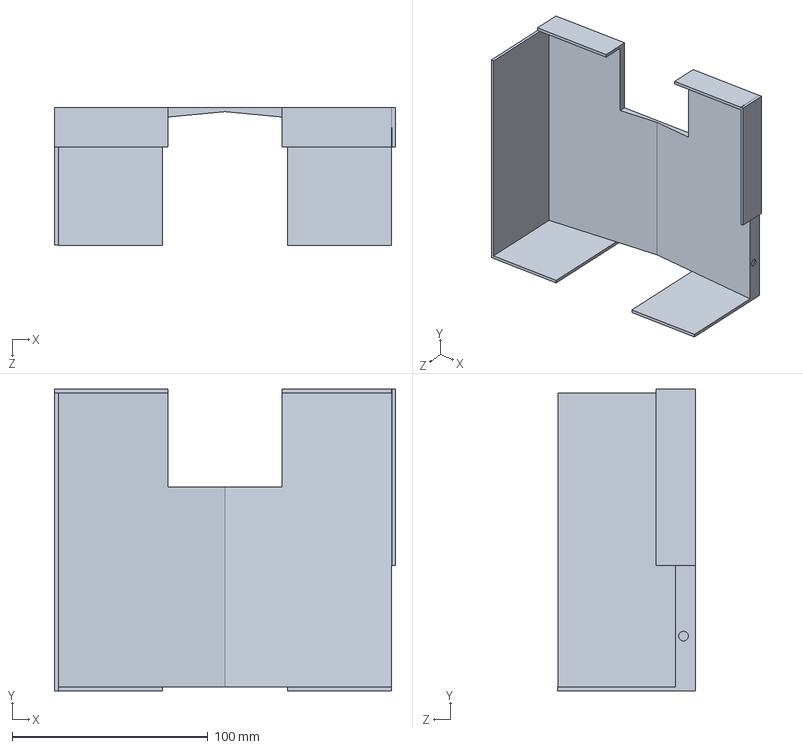
[picture p116: CAD file, 2017-02-13]
SolidWorks/El Padre/Base_roulante/Assemblage popcorn/Pièces/Bac/Bac ping pong.SLDPRT
174.0 x 154.1 x 70.2 mm
