nsobczak/CoupeDeFrance/SolidWorks/El Padre/Base_roulante/Assemblage popcorn/Pièces/socle/Gand socle.SLDPRT

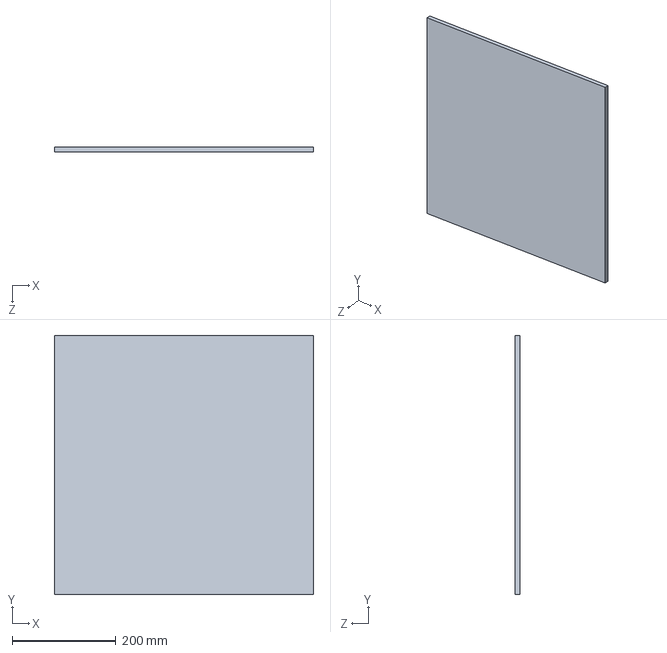
[picture p117: CAD file, 2017-02-13]
SolidWorks/El Padre/Base_roulante/Assemblage popcorn/Pièces/socle/Gand socle.SLDPRT
500.0 x 500.0 x 10.0 mm
