nsobczak/CoupeDeFrance/SolidWorks/El Padre/Base_roulante/Assemblage popcorn/Pièces/Tige/tige.SLDPRT

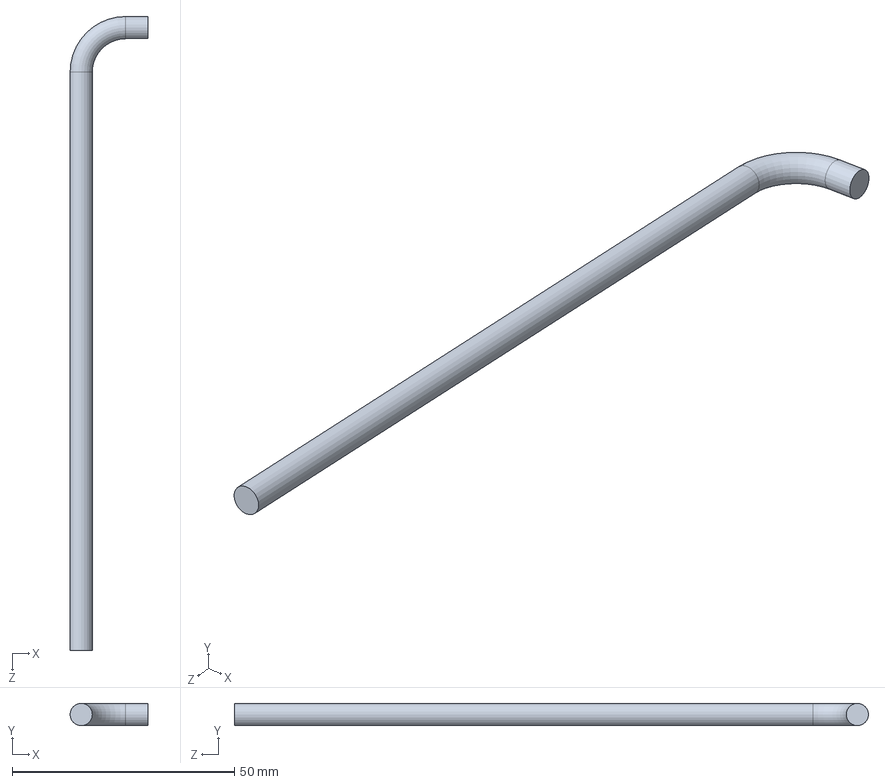
[picture p118: CAD file, 2017-02-13]
SolidWorks/El Padre/Base_roulante/Assemblage popcorn/Pièces/Tige/tige.SLDPRT
17.5 x 5.00 x 142.5 mm
