nsobczak/CoupeDeFrance/SolidWorks/El Padre/Base_roulante/Assemblage popcorn/Pièces/Tube/bord.SLDPRT

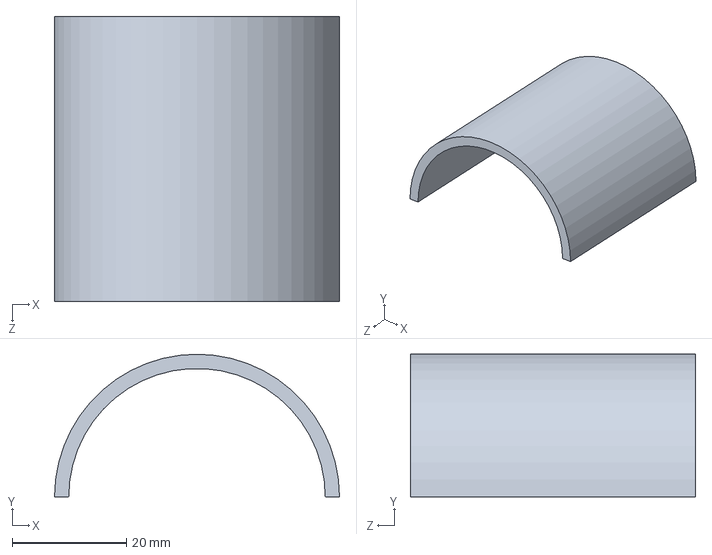
[picture p119: CAD file, 2017-02-13]
SolidWorks/El Padre/Base_roulante/Assemblage popcorn/Pièces/Tube/bord.SLDPRT
50.0 x 25.0 x 50.0 mm
