nsobczak/CoupeDeFrance/SolidWorks/El Padre/Base_roulante/assemblage_spot2/plaque_engrenage_qui_sort.SLDPRT

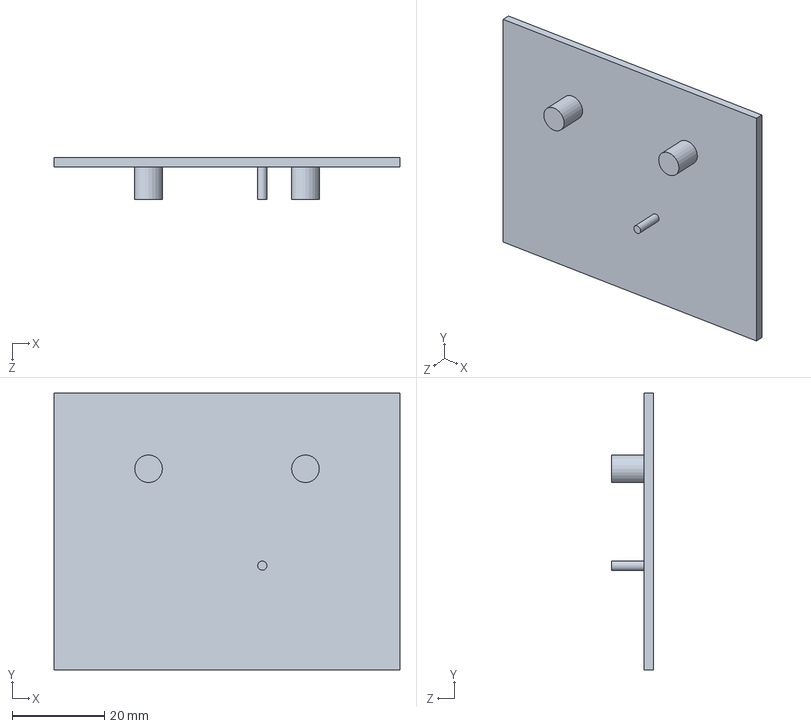
[picture p120: CAD file, 2017-02-13]
SolidWorks/El Padre/Base_roulante/assemblage_spot2/plaque_engrenage_qui_sort.SLDPRT
75.0 x 60.0 x 9.00 mm
