nsobczak/CoupeDeFrance/SolidWorks/El Padre/Base_roulante/Base du robot/bille_porteuse/Support_bille_appui.SLDPRT

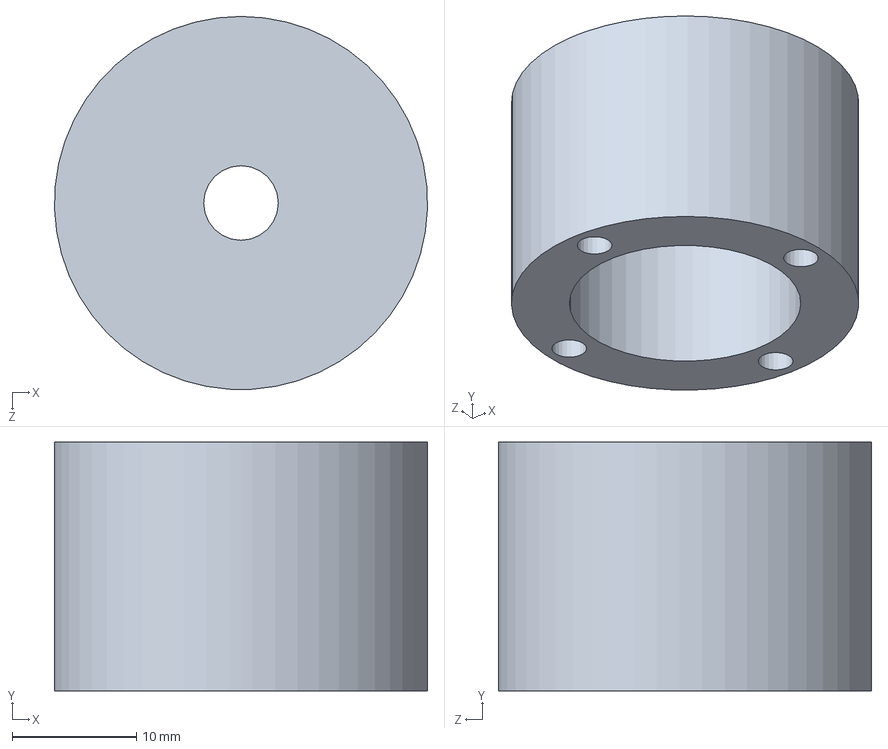
[picture p121: CAD file, 2017-02-13]
SolidWorks/El Padre/Base_roulante/Base du robot/bille_porteuse/Support_bille_appui.SLDPRT
30.0 x 20.0 x 30.0 mm
