nsobczak/CoupeDeFrance/SolidWorks/El Padre/Base_roulante/Base du robot/socleV2.SLDPRT

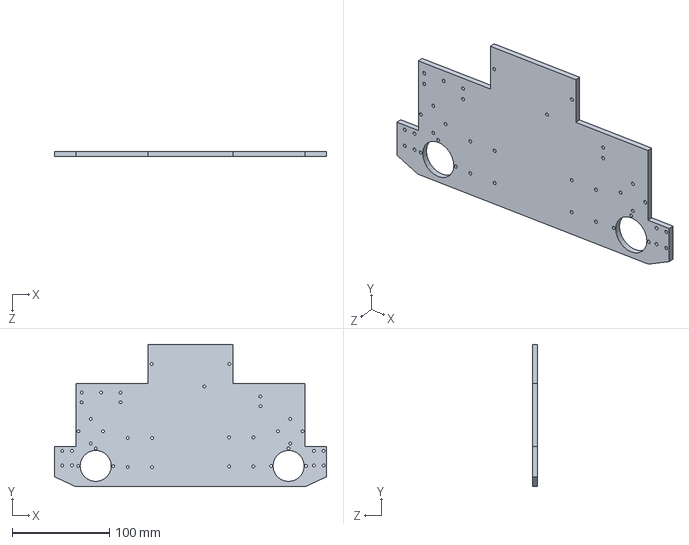
[picture p122: CAD file, 2017-05-04]
SolidWorks/El Padre/Base_roulante/Base du robot/socleV2.SLDPRT
280.0 x 146.2 x 5.00 mm
