nsobczak/CoupeDeFrance/SolidWorks/El Padre/Base_roulante/Bloc moteur/nouvelle_codeuse.SLDPRT

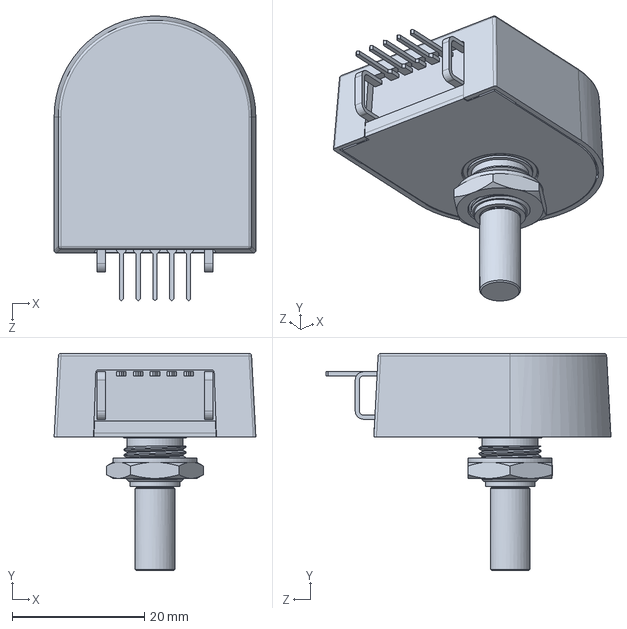
[picture p123: CAD file, 2017-02-13]
SolidWorks/El Padre/Base_roulante/Bloc moteur/nouvelle_codeuse.SLDPRT
30.5 x 32.8 x 43.1 mm
