nsobczak/CoupeDeFrance/SolidWorks/El Padre/Base_roulante/Claps/AntiClapsFinal/BloqueurTige.SLDPRT

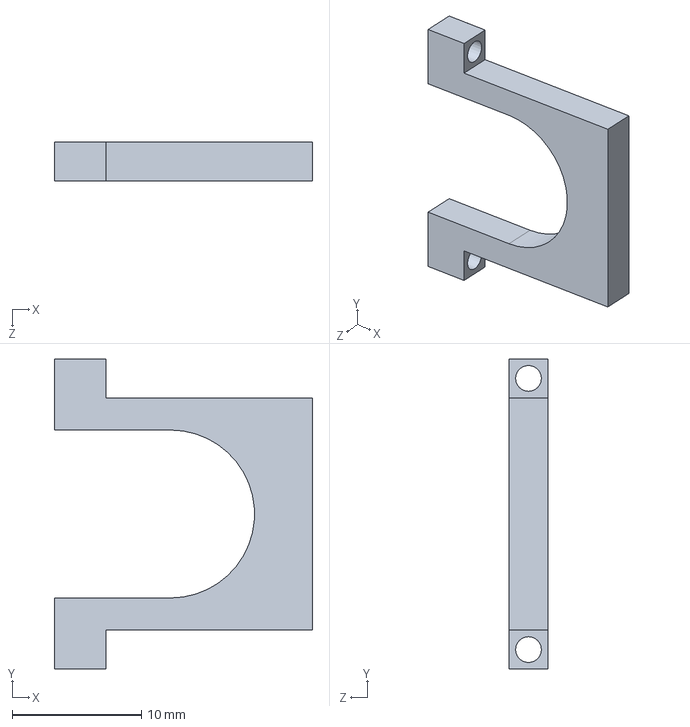
[picture p124: CAD file, 2017-02-13]
SolidWorks/El Padre/Base_roulante/Claps/AntiClapsFinal/BloqueurTige.SLDPRT
20.0 x 24.0 x 3.00 mm
