nsobczak/CoupeDeFrance/SolidWorks/El Padre/Base_roulante/Claps/Clap/haut claps.SLDPRT

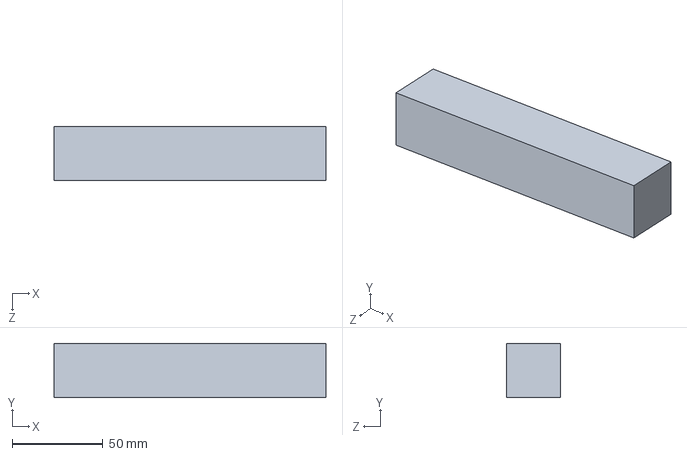
[picture p125: CAD file, 2017-02-13]
SolidWorks/El Padre/Base_roulante/Claps/Clap/haut claps.SLDPRT
150.0 x 30.0 x 30.0 mm
