nsobczak/CoupeDeFrance/SolidWorks/El Padre/isen robot 2016-17/PROTEGE FACE.SLDPRT

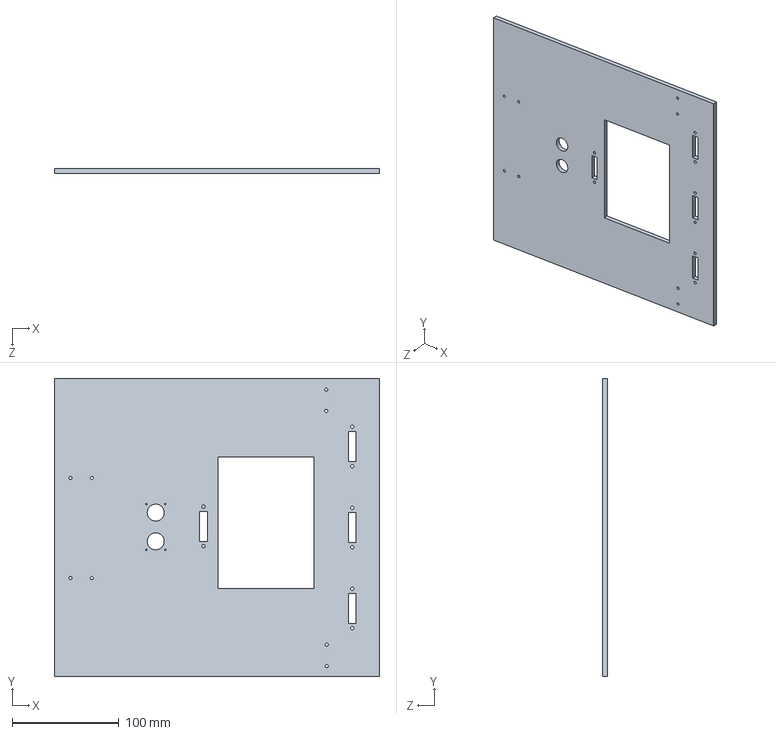
[picture p126: CAD file, 2017-05-10]
SolidWorks/El Padre/isen robot 2016-17/PROTEGE FACE.SLDPRT
305.0 x 280.0 x 5.00 mm
