nsobczak/CoupeDeFrance/SolidWorks/El Padre/isen robot 2016-17/TiretteDeDepart/Carlingue/Bas.SLDPRT

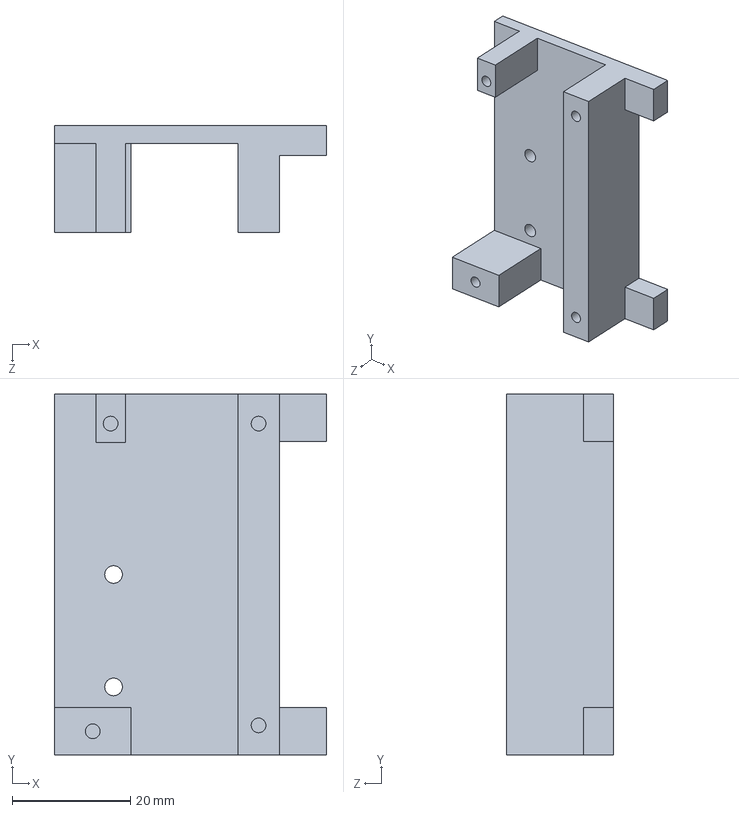
[picture p127: CAD file, 2017-04-14]
SolidWorks/El Padre/isen robot 2016-17/TiretteDeDepart/Carlingue/Bas.SLDPRT
46.0 x 61.0 x 18.0 mm
