nsobczak/CoupeDeFrance/SolidWorks/El Padre/isen robot 2016-17/TiretteDeDepart/EndStop/End-Stop.SLDPRT

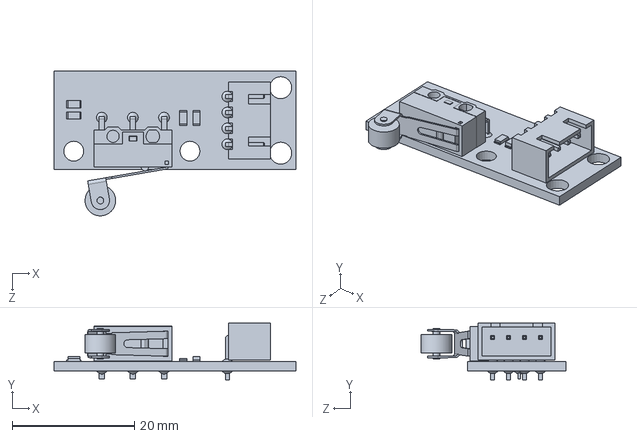
[picture p128: CAD file, 2017-04-14]
SolidWorks/El Padre/isen robot 2016-17/TiretteDeDepart/EndStop/End-Stop.SLDPRT
39.5 x 9.25 x 23.6 mm
