nsobczak/CoupeDeFrance/SolidWorks/El Padre/isen robot 2016-17/TiretteDeDepart/Tirette/Tirette.SLDPRT

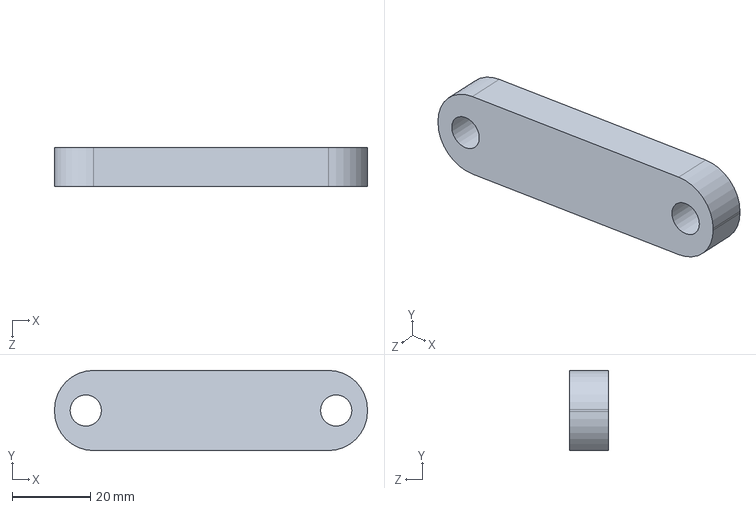
[picture p129: CAD file, 2017-04-14]
SolidWorks/El Padre/isen robot 2016-17/TiretteDeDepart/Tirette/Tirette.SLDPRT
80.0 x 20.5 x 10.0 mm
