nsobczak/CoupeDeFrance/SolidWorks/El Padre/Plans découpeuse laser des différentes faces/GAUCHE_EL_PADRE.DXF

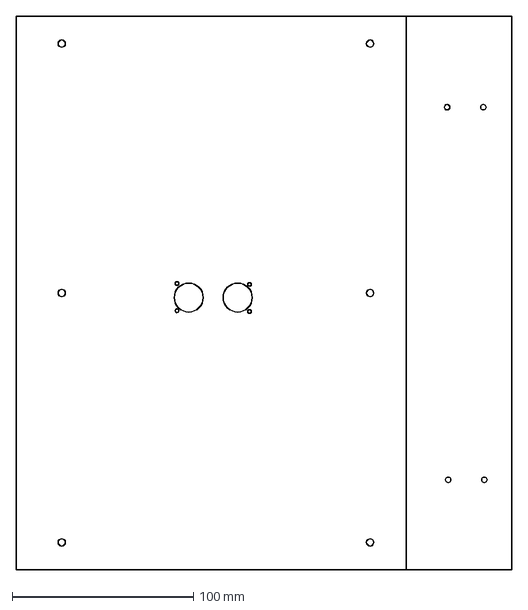
[picture p130: CAD file, 2017-04-14]
SolidWorks/El Padre/Plans découpeuse laser des différentes faces/GAUCHE_EL_PADRE.DXF
273.0 x 305.0 mm
