nsobczak/CoupeDeFrance/SolidWorks/El Padre/Base_roulante/Actionneur/herkulex_DRS0101_servomoteur.SLDPRT

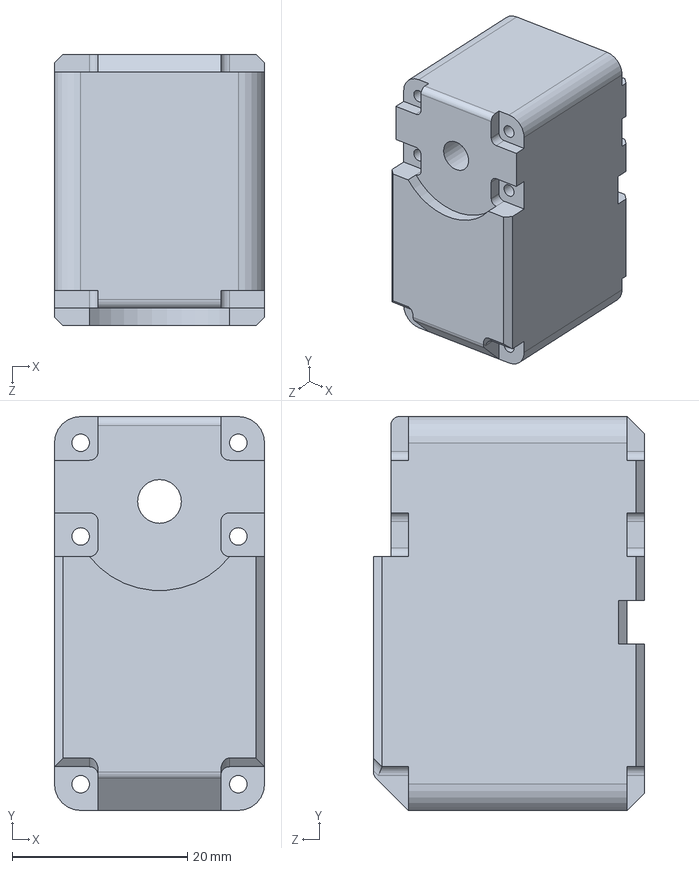
[picture p131: CAD file, 2017-02-13]
SolidWorks/El Padre/Base_roulante/Actionneur/herkulex_DRS0101_servomoteur.SLDPRT
24.0 x 45.0 x 31.0 mm
