nsobczak/CoupeDeFrance/SolidWorks/El Padre/Base_roulante/Assemblage popcorn/Pièces/Clapet/Axe servo.SLDPRT

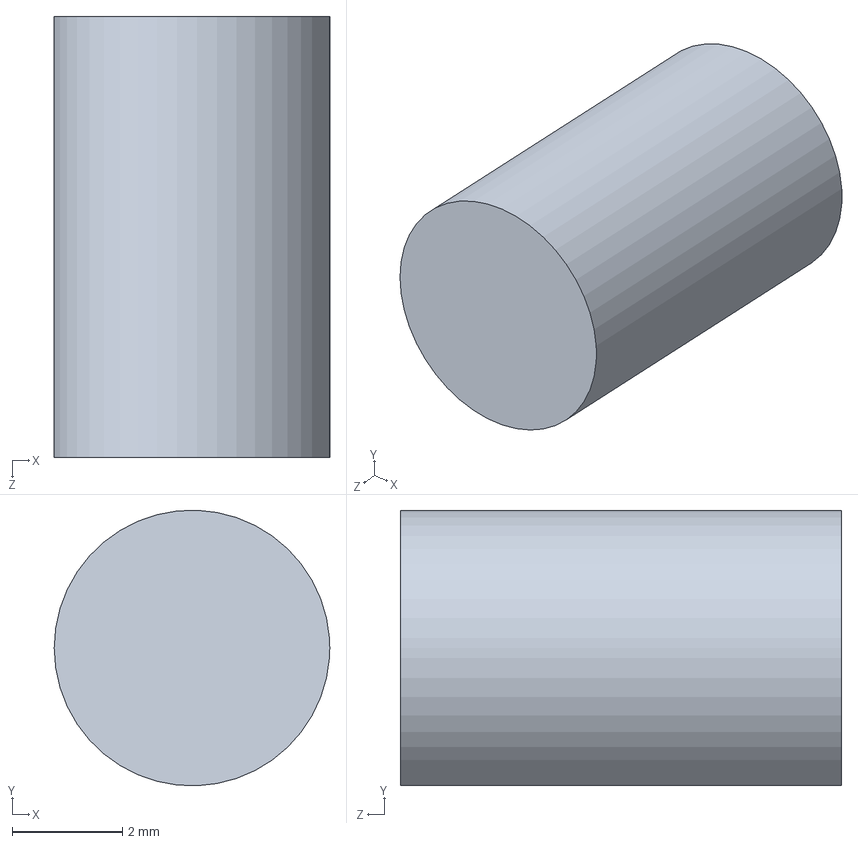
[picture p132: CAD file, 2017-02-13]
SolidWorks/El Padre/Base_roulante/Assemblage popcorn/Pièces/Clapet/Axe servo.SLDPRT
5.00 x 5.00 x 8.00 mm
