nsobczak/CoupeDeFrance/SolidWorks/El Padre/Base_roulante/Assemblage popcorn/Pièces/socle/socle servo bac.SLDPRT

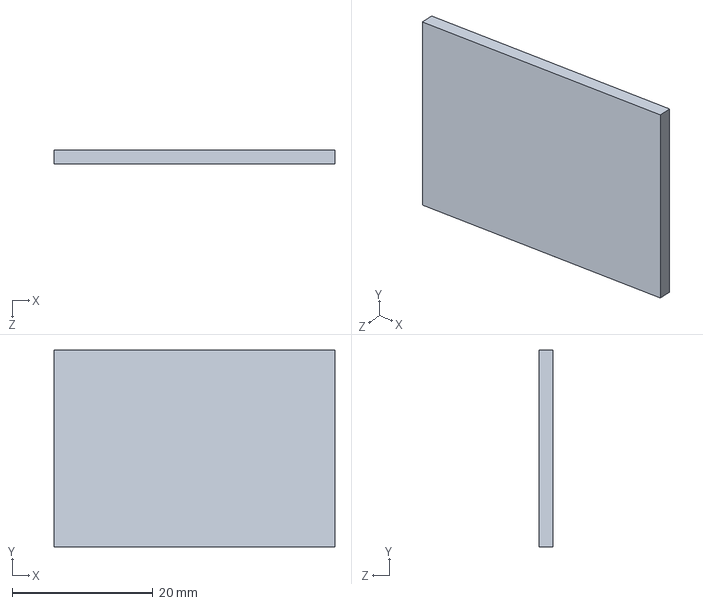
[picture p133: CAD file, 2017-02-13]
SolidWorks/El Padre/Base_roulante/Assemblage popcorn/Pièces/socle/socle servo bac.SLDPRT
40.0 x 28.0 x 2.00 mm
