nsobczak/CoupeDeFrance/SolidWorks/El Padre/Base_roulante/assemblage_spot2/support_pince_pour_vis.SLDPRT

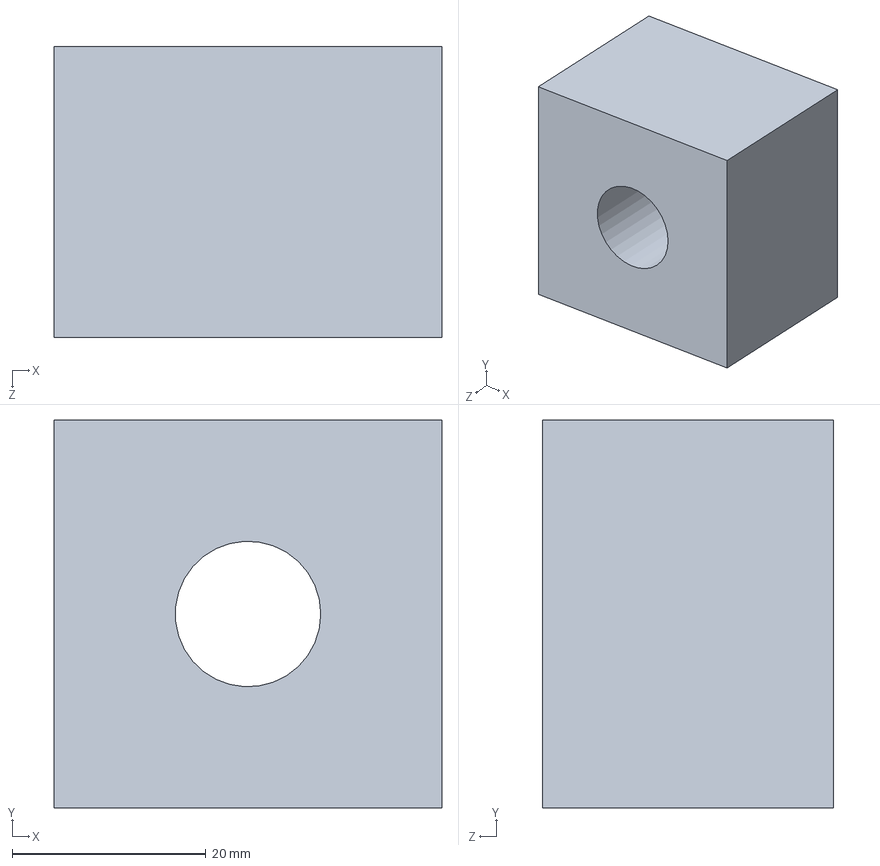
[picture p134: CAD file, 2017-02-13]
SolidWorks/El Padre/Base_roulante/assemblage_spot2/support_pince_pour_vis.SLDPRT
40.0 x 40.0 x 30.0 mm
