nsobczak/CoupeDeFrance/SolidWorks/El Padre/Base_roulante/Base du robot/Protege_arriere.SLDPRT

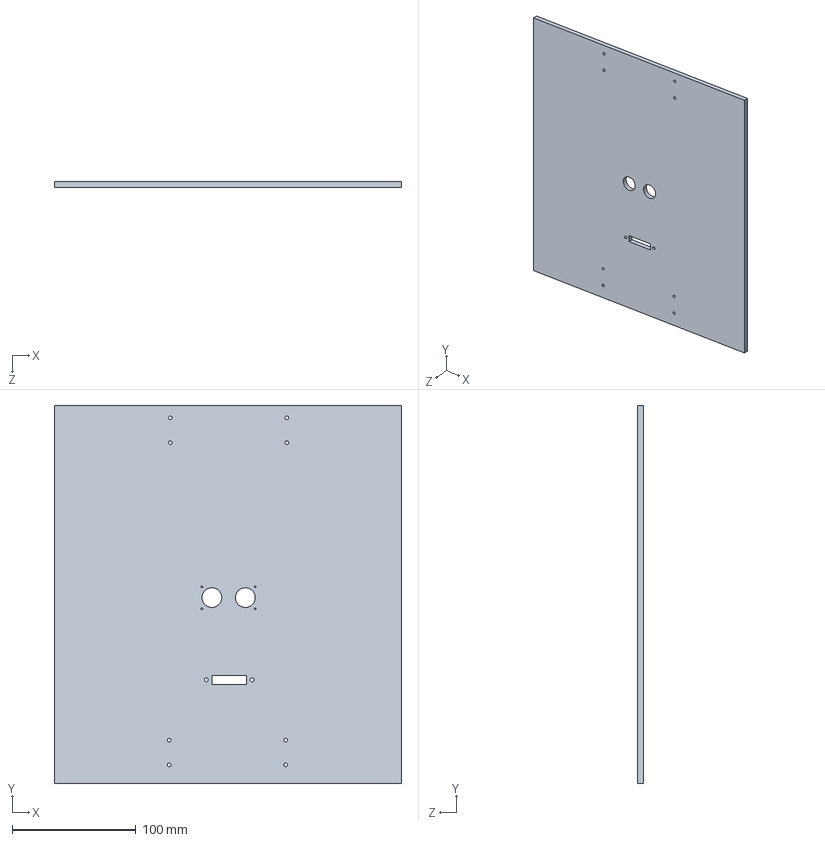
[picture p135: CAD file, 2017-05-04]
SolidWorks/El Padre/Base_roulante/Base du robot/Protege_arriere.SLDPRT
280.0 x 305.0 x 5.00 mm
