nsobczak/CoupeDeFrance/SolidWorks/El Padre/Base_roulante/Bloc moteur/axe inter.SLDPRT

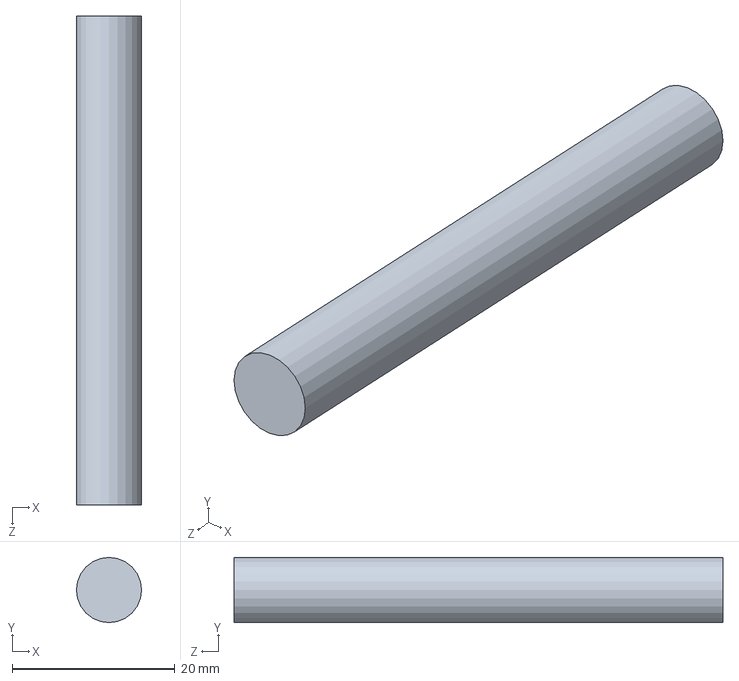
[picture p136: CAD file, 2017-02-13]
SolidWorks/El Padre/Base_roulante/Bloc moteur/axe inter.SLDPRT
8.00 x 8.00 x 60.0 mm
