nsobczak/CoupeDeFrance/SolidWorks/El Padre/Base_roulante/Claps/AntiClapsFinal/support.SLDPRT

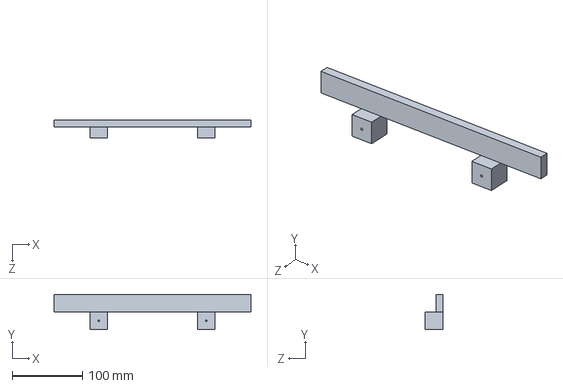
[picture p137: CAD file, 2017-02-13]
SolidWorks/El Padre/Base_roulante/Claps/AntiClapsFinal/support.SLDPRT
280.0 x 50.0 x 25.0 mm
