nsobczak/CoupeDeFrance/SolidWorks/El Padre/Base_roulante/cristeo/canon.STL

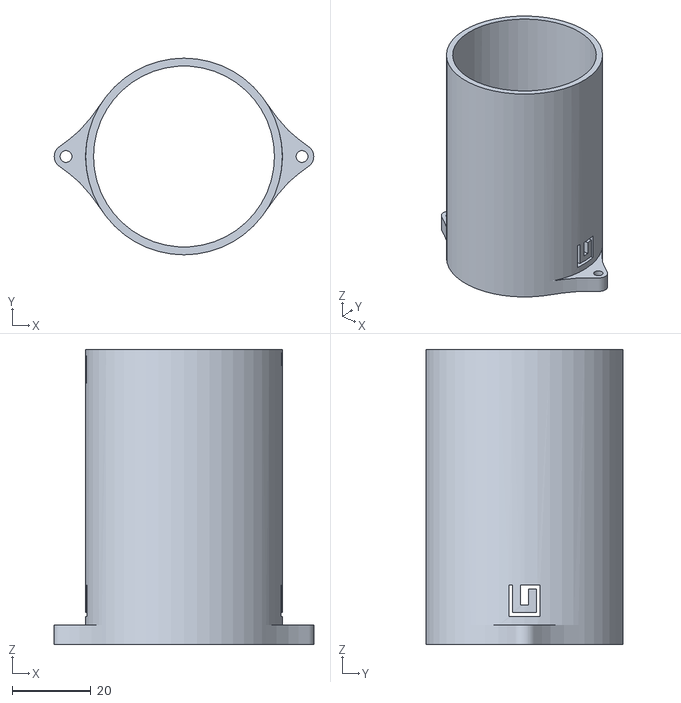
[picture p138: CAD file, 2017-04-03]
SolidWorks/El Padre/Base_roulante/cristeo/canon.STL
66.0 x 50.0 x 75.0
