nsobczak/CoupeDeFrance/SolidWorks/El Padre/isen robot 2016-17/Funny Action/support moteur 2.SLDPRT

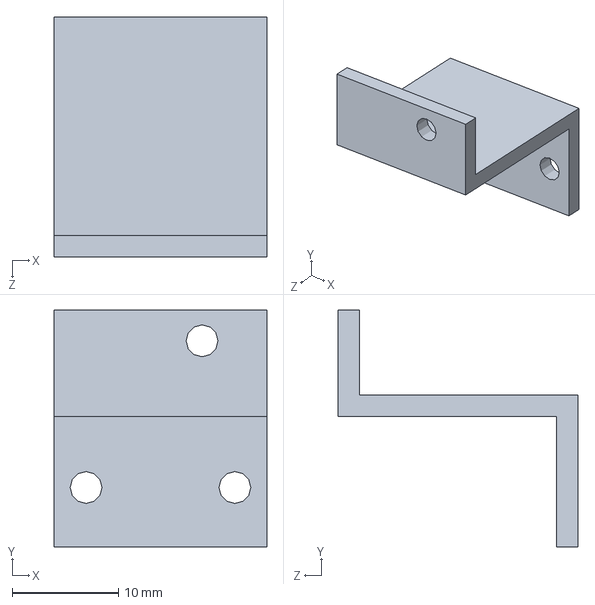
[picture p139: CAD file, 2017-04-14]
SolidWorks/El Padre/isen robot 2016-17/Funny Action/support moteur 2.SLDPRT
20.0 x 22.3 x 22.5 mm
