nsobczak/CoupeDeFrance/SolidWorks/El Padre/isen robot 2016-17/Pince/support_charriot_2.SLDPRT

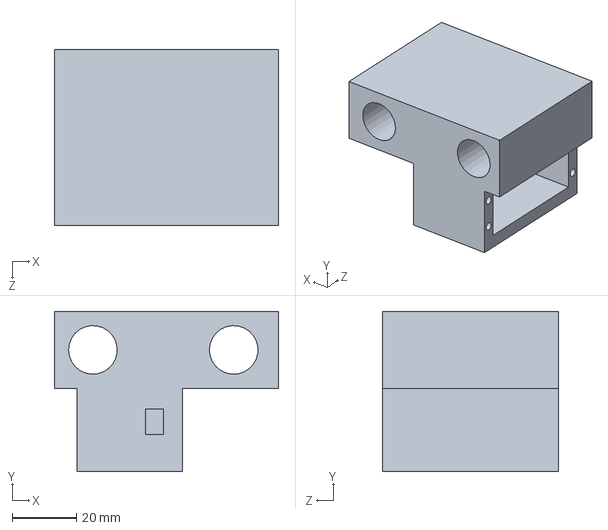
[picture p140: CAD file, 2017-03-29]
SolidWorks/El Padre/isen robot 2016-17/Pince/support_charriot_2.SLDPRT
70.0 x 50.0 x 55.0 mm
