nsobczak/CoupeDeFrance/SolidWorks/El Padre/isen robot 2016-17/support batterieV2.SLDPRT

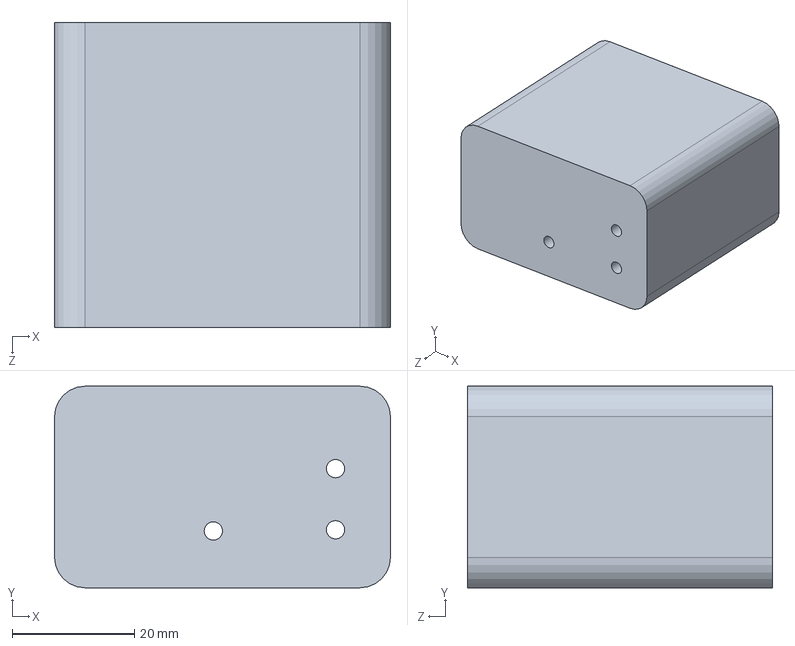
[picture p141: CAD file, 2017-05-10]
SolidWorks/El Padre/isen robot 2016-17/support batterieV2.SLDPRT
55.0 x 33.0 x 50.0 mm
