nsobczak/CoupeDeFrance/SolidWorks/El Padre/isen robot 2016-17/TiretteDeDepart/Carlingue/Haut.SLDPRT

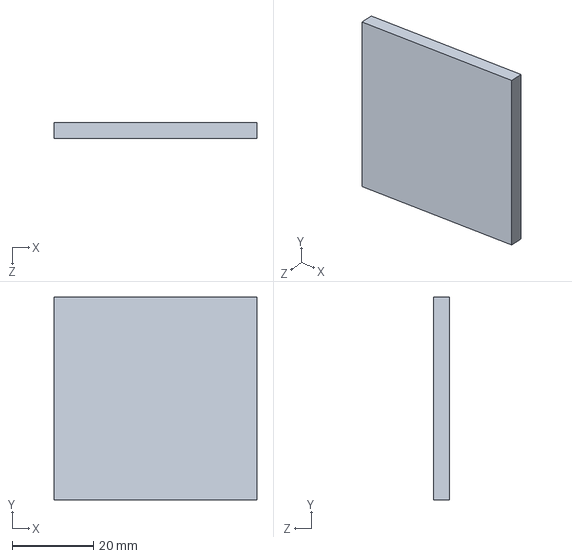
[picture p142: CAD file, 2017-04-07]
SolidWorks/El Padre/isen robot 2016-17/TiretteDeDepart/Carlingue/Haut.SLDPRT
50.0 x 50.0 x 4.00 mm
