nsobczak/CoupeDeFrance/SolidWorks/El Padre/Plans découpeuse laser des différentes faces/ARRIERE_EL_PADRE.DXF

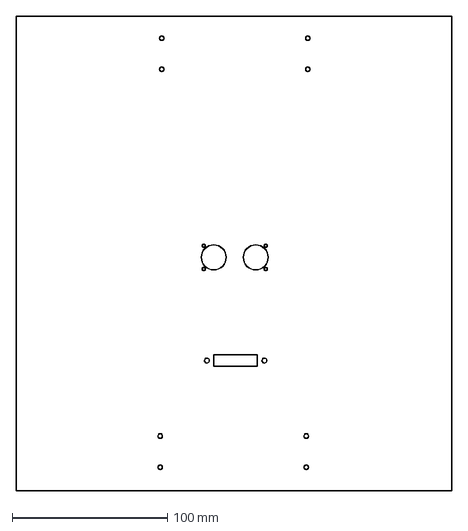
[picture p143: CAD file, 2017-04-14]
SolidWorks/El Padre/Plans découpeuse laser des différentes faces/ARRIERE_EL_PADRE.DXF
280.0 x 305.0 mm
