nsobczak/CoupeDeFrance/SolidWorks/El Padre/Base_roulante/Assemblage popcorn/Pièces/Clapet/clapet1.SLDPRT

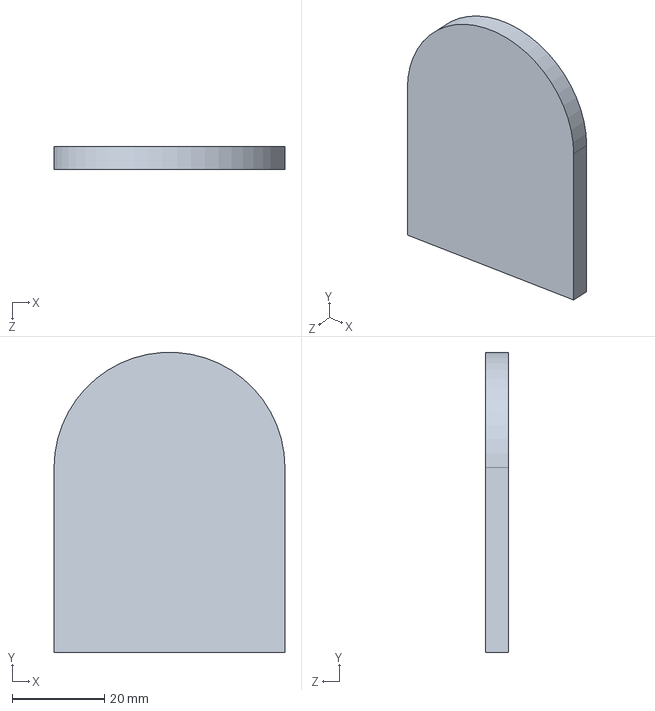
[picture p144: CAD file, 2017-02-13]
SolidWorks/El Padre/Base_roulante/Assemblage popcorn/Pièces/Clapet/clapet1.SLDPRT
50.0 x 65.0 x 5.00 mm
