nsobczak/CoupeDeFrance/SolidWorks/El Padre/Base_roulante/Assemblage popcorn/Pièces/socle/socle.SLDPRT

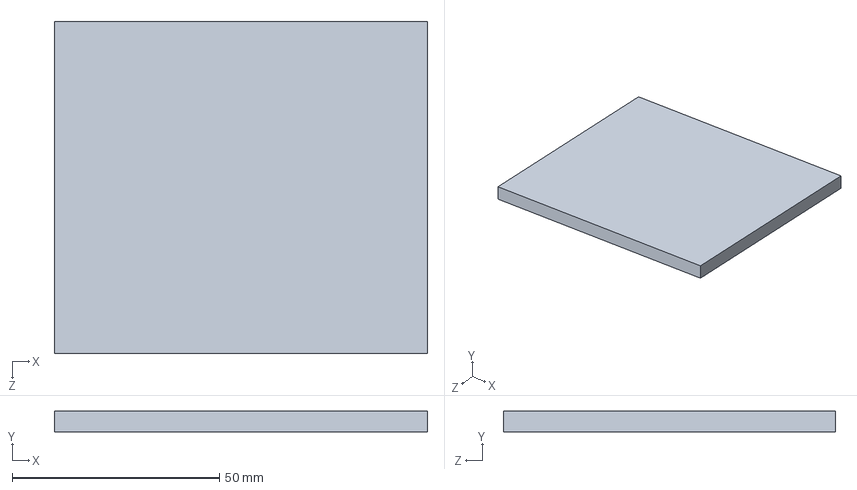
[picture p145: CAD file, 2017-02-13]
SolidWorks/El Padre/Base_roulante/Assemblage popcorn/Pièces/socle/socle.SLDPRT
90.0 x 5.00 x 80.0 mm
