nsobczak/CoupeDeFrance/SolidWorks/El Padre/Base_roulante/Base du robot/bille_porteuse/porte_bille.SLDPRT

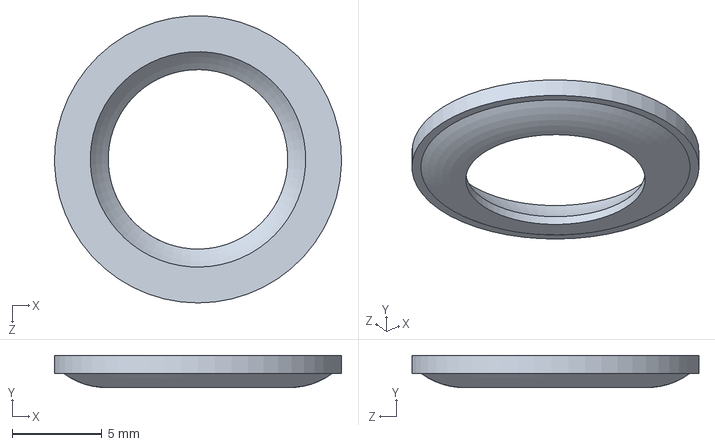
[picture p146: CAD file, 2017-02-13]
SolidWorks/El Padre/Base_roulante/Base du robot/bille_porteuse/porte_bille.SLDPRT
16.0 x 1.79 x 16.0 mm
