nsobczak/CoupeDeFrance/SolidWorks/El Padre/Base_roulante/Base du robot/socle00.SLDPRT

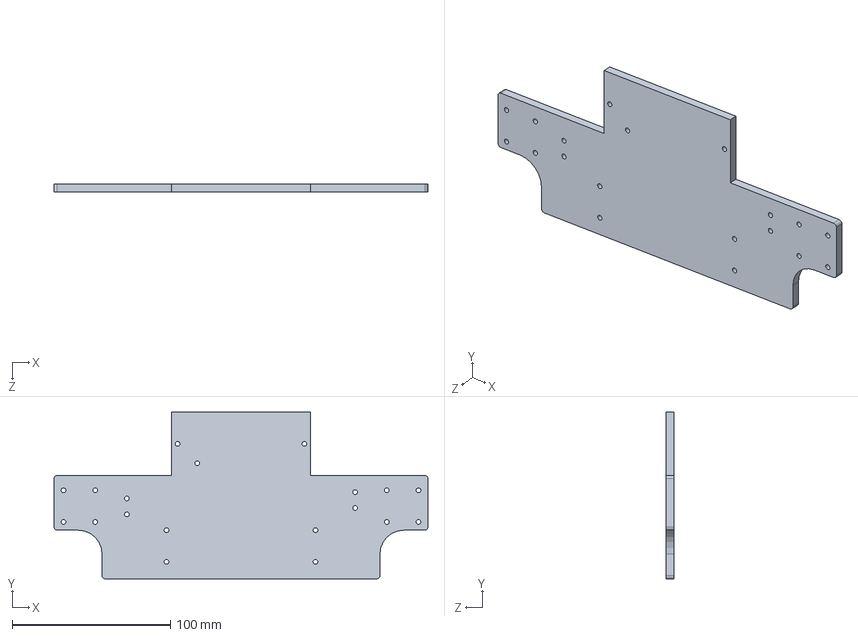
[picture p147: CAD file, 2017-05-04]
SolidWorks/El Padre/Base_roulante/Base du robot/socle00.SLDPRT
236.0 x 105.2 x 5.00 mm
