nsobczak/CoupeDeFrance/SolidWorks/El Padre/Base_roulante/Bloc moteur/ROULEMENT.SLDPRT

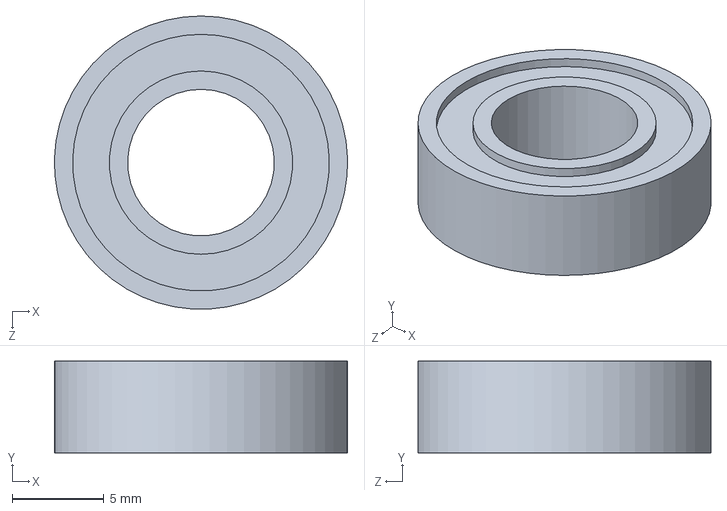
[picture p148: CAD file, 2017-02-13]
SolidWorks/El Padre/Base_roulante/Bloc moteur/ROULEMENT.SLDPRT
16.0 x 5.00 x 16.0 mm
