nsobczak/CoupeDeFrance/SolidWorks/El Padre/Base_roulante/Claps/AntiClapsFinal/Vis 2.SLDPRT

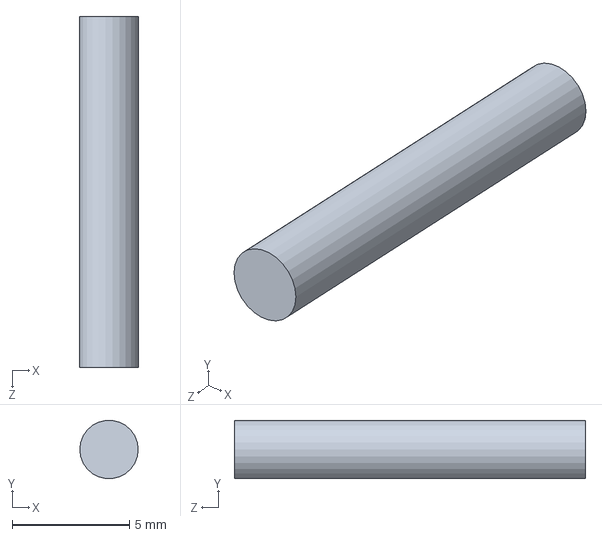
[picture p149: CAD file, 2017-02-13]
SolidWorks/El Padre/Base_roulante/Claps/AntiClapsFinal/Vis 2.SLDPRT
2.50 x 2.48 x 15.0 mm
