nsobczak/CoupeDeFrance/SolidWorks/El Padre/Base_roulante/Claps/Clap/bas claps.SLDPRT

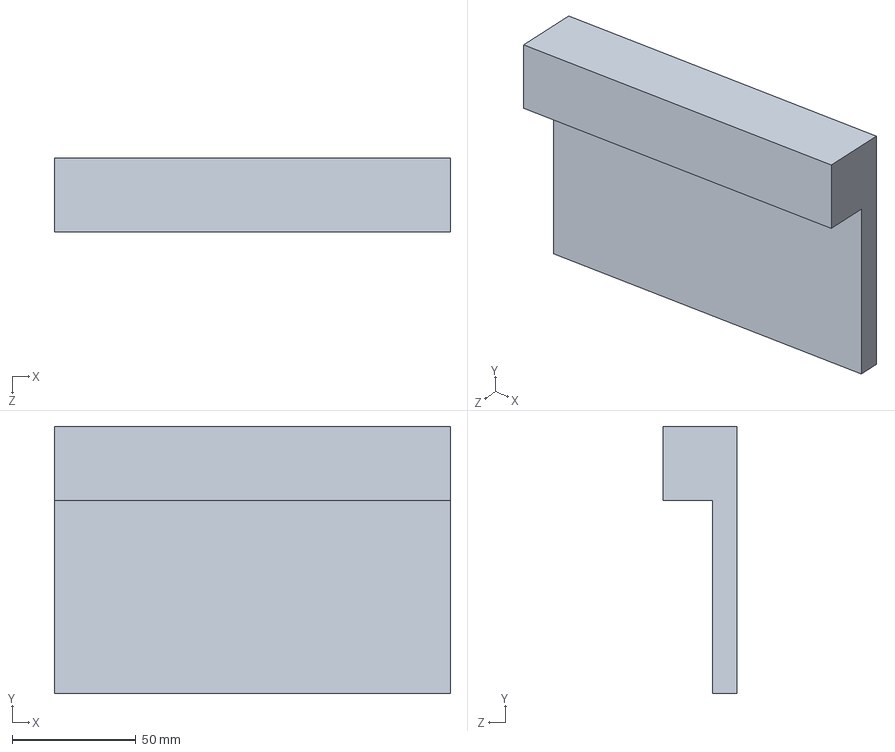
[picture p150: CAD file, 2017-02-13]
SolidWorks/El Padre/Base_roulante/Claps/Clap/bas claps.SLDPRT
160.0 x 108.0 x 30.0 mm
