nsobczak/CoupeDeFrance/SolidWorks/El Padre/isen robot 2016-17/Funny Action/bague support.SLDPRT

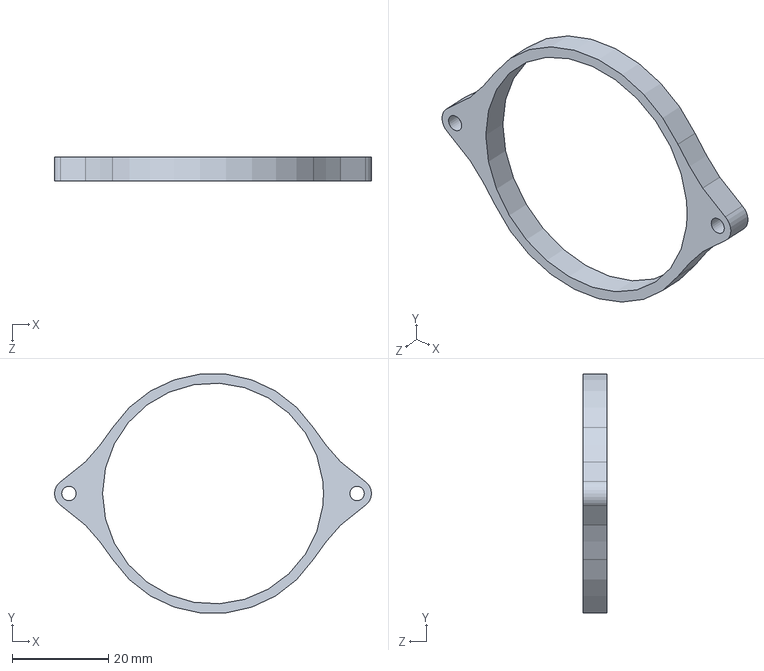
[picture p151: CAD file, 2017-04-14]
SolidWorks/El Padre/isen robot 2016-17/Funny Action/bague support.SLDPRT
66.0 x 49.7 x 5.00 mm
