nsobczak/CoupeDeFrance/SolidWorks/El Padre/isen robot 2016-17/Pince/Pièce11.SLDPRT

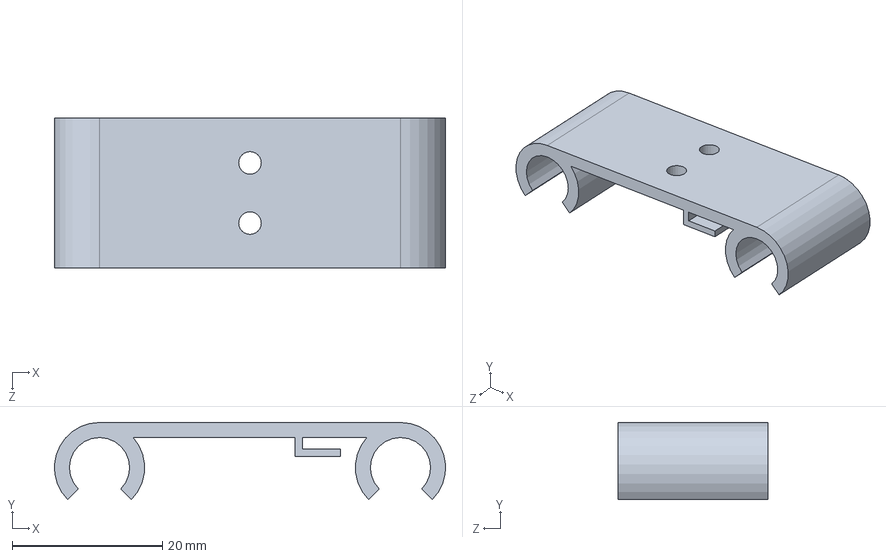
[picture p152: CAD file, 2017-02-13]
SolidWorks/El Padre/isen robot 2016-17/Pince/Pièce11.SLDPRT
52.0 x 10.2 x 20.0 mm
