nsobczak/CoupeDeFrance/SolidWorks/El Padre/isen robot 2016-17/SupportRoulementBille.SLDPRT

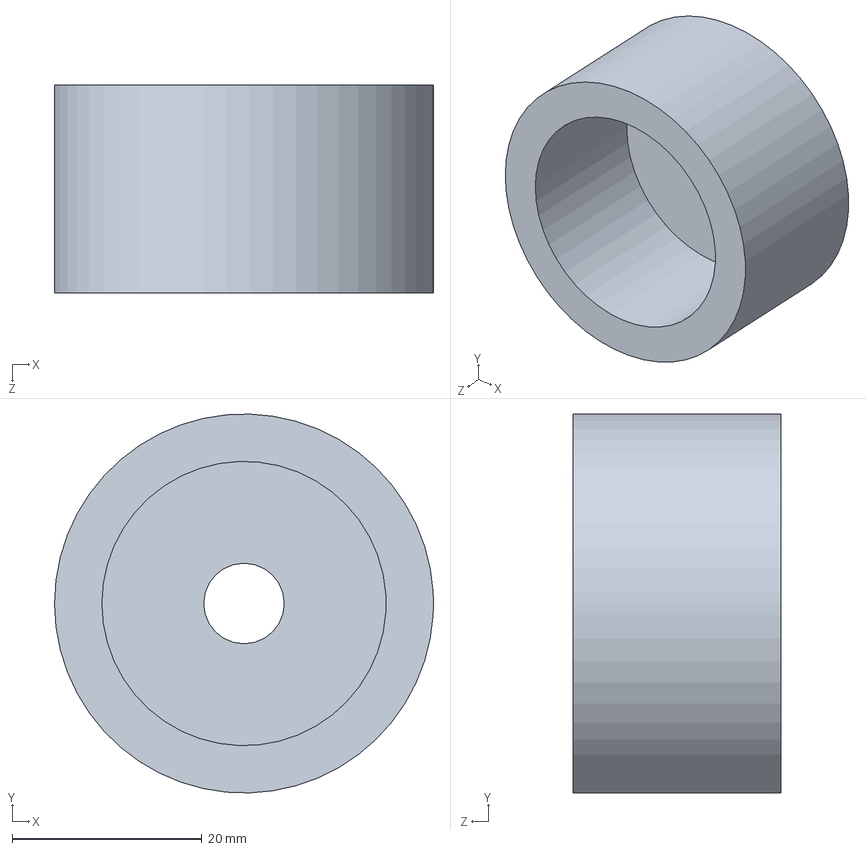
[picture p153: CAD file, 2017-05-10]
SolidWorks/El Padre/isen robot 2016-17/SupportRoulementBille.SLDPRT
40.0 x 40.0 x 22.0 mm
