nsobczak/CoupeDeFrance/SolidWorks/El Padre/Plans découpeuse laser des différentes faces/HAUT_EL_PADRE.DXF

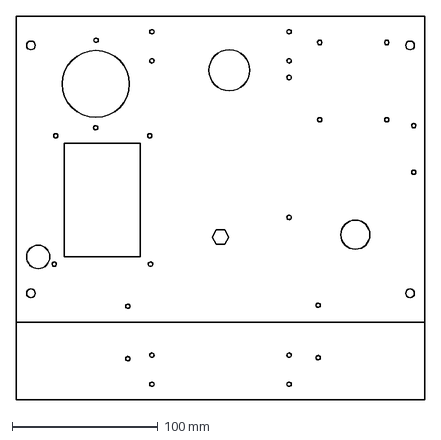
[picture p154: CAD file, 2017-04-14]
SolidWorks/El Padre/Plans découpeuse laser des différentes faces/HAUT_EL_PADRE.DXF
280.0 x 263.0 mm
