nsobczak/CoupeDeFrance/SolidWorks/El Padre/Base_roulante/Assemblage popcorn/Pièces/Clapet/clapet2.SLDPRT

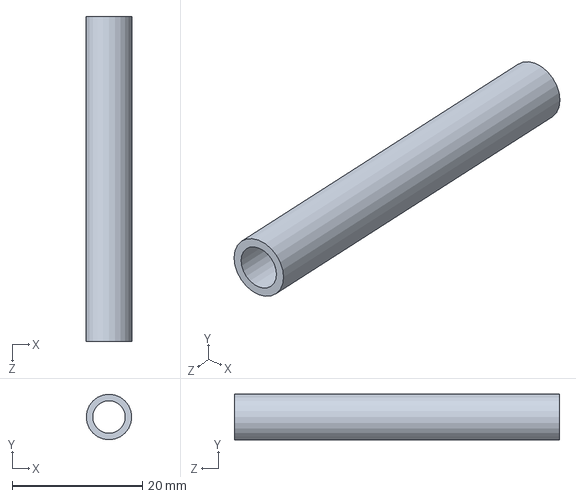
[picture p155: CAD file, 2017-02-13]
SolidWorks/El Padre/Base_roulante/Assemblage popcorn/Pièces/Clapet/clapet2.SLDPRT
7.00 x 7.00 x 50.0 mm
