nsobczak/CoupeDeFrance/SolidWorks/El Padre/Base_roulante/Assemblage popcorn/Pièces/socle/socle servo clapet.SLDPRT

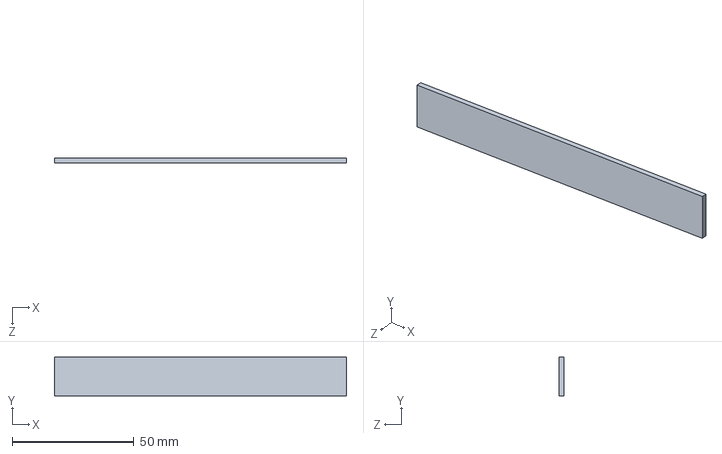
[picture p156: CAD file, 2017-02-13]
SolidWorks/El Padre/Base_roulante/Assemblage popcorn/Pièces/socle/socle servo clapet.SLDPRT
120.0 x 16.0 x 2.00 mm
