nsobczak/CoupeDeFrance/SolidWorks/El Padre/Base_roulante/Assemblage popcorn/Pièces/Tube/tube2.SLDPRT

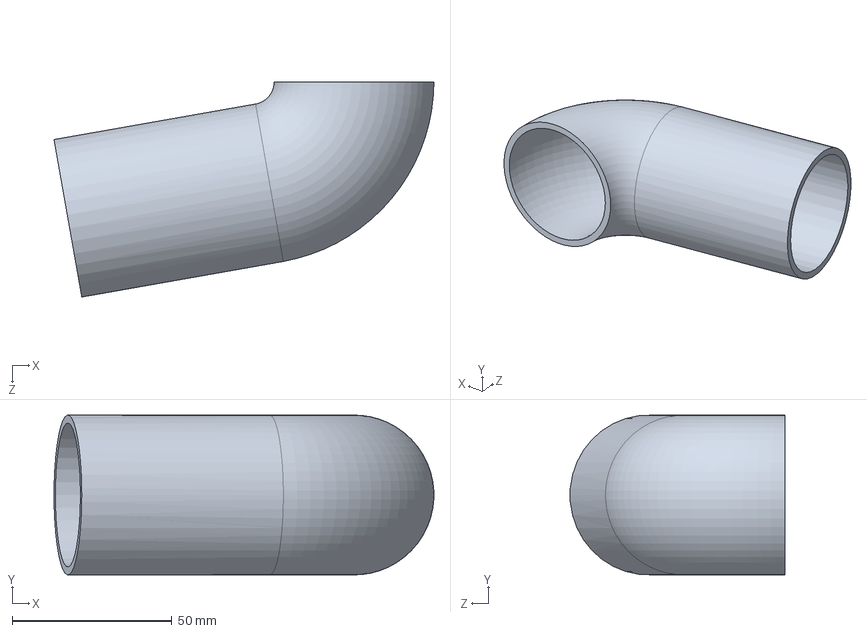
[picture p157: CAD file, 2017-02-13]
SolidWorks/El Padre/Base_roulante/Assemblage popcorn/Pièces/Tube/tube2.SLDPRT
118.8 x 50.0 x 67.2 mm
