nsobczak/CoupeDeFrance/SolidWorks/El Padre/Base_roulante/assemblage_spot2/spot.SLDPRT

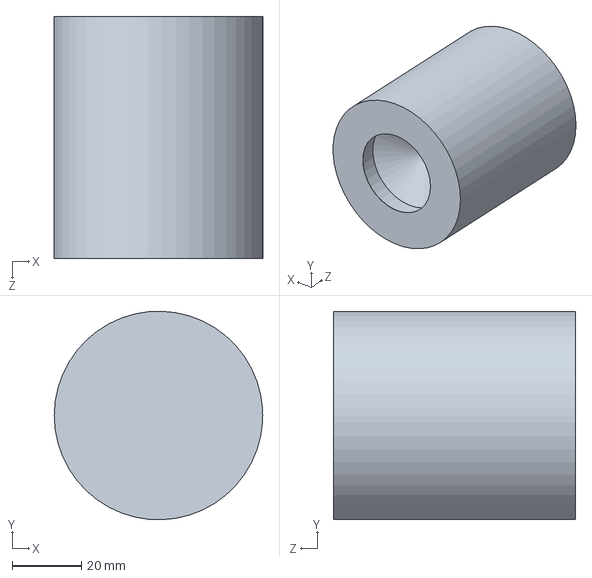
[picture p158: CAD file, 2017-02-13]
SolidWorks/El Padre/Base_roulante/assemblage_spot2/spot.SLDPRT
60.3 x 60.3 x 70.0 mm
