nsobczak/CoupeDeFrance/SolidWorks/El Padre/Base_roulante/Base du robot/bille_porteuse/bille.SLDPRT

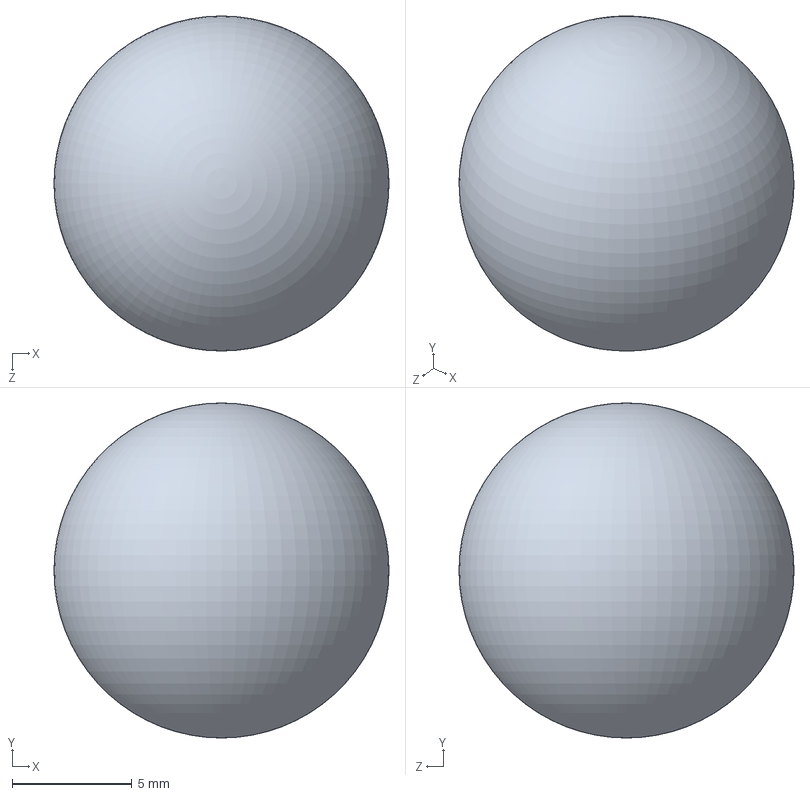
[picture p159: CAD file, 2017-02-13]
SolidWorks/El Padre/Base_roulante/Base du robot/bille_porteuse/bille.SLDPRT
14.0 x 14.0 x 14.0 mm
