nsobczak/CoupeDeFrance/SolidWorks/El Padre/Base_roulante/Base du robot/Protege_laterale_gauche.SLDPRT

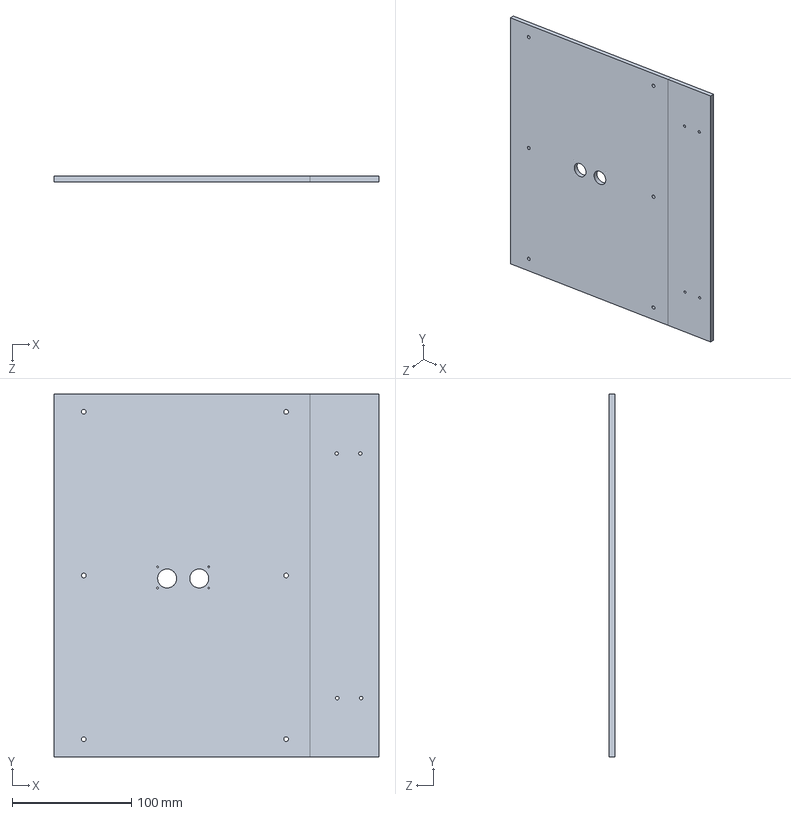
[picture p160: CAD file, 2017-05-04]
SolidWorks/El Padre/Base_roulante/Base du robot/Protege_laterale_gauche.SLDPRT
273.0 x 305.0 x 5.00 mm
