nsobczak/CoupeDeFrance/SolidWorks/El Padre/Base_roulante/Bloc moteur/coulisse codeur.SLDPRT

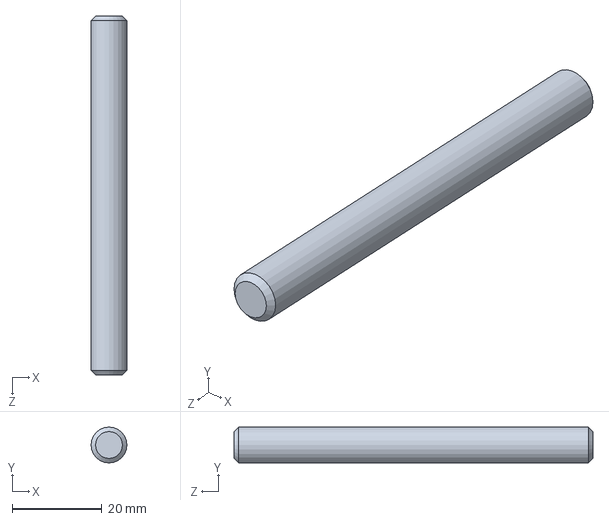
[picture p161: CAD file, 2017-02-13]
SolidWorks/El Padre/Base_roulante/Bloc moteur/coulisse codeur.SLDPRT
8.00 x 8.00 x 80.0 mm
