nsobczak/CoupeDeFrance/SolidWorks/El Padre/isen robot 2016-17/Pince/Pièce22.SLDPRT

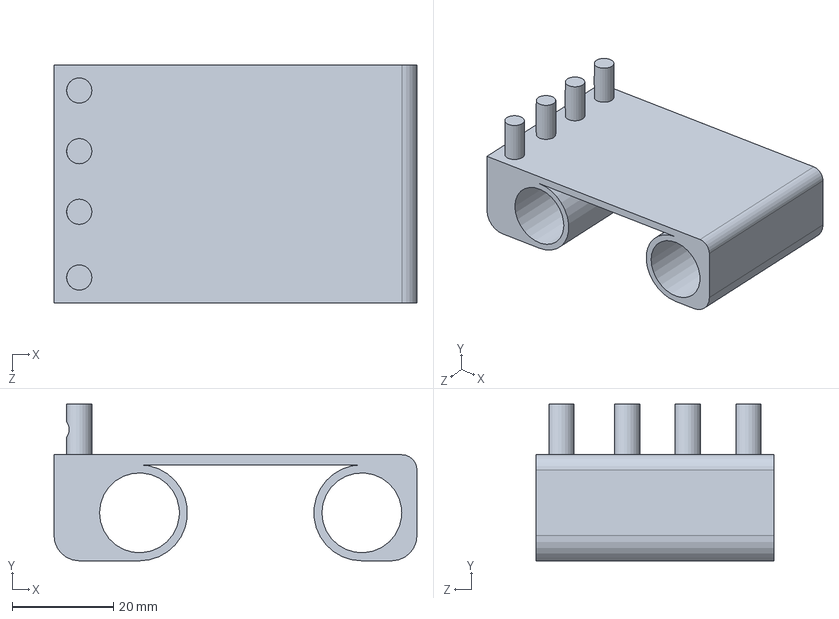
[picture p162: CAD file, 2017-02-13]
SolidWorks/El Padre/isen robot 2016-17/Pince/Pièce22.SLDPRT
71.8 x 31.0 x 47.0 mm
