nsobczak/CoupeDeFrance/SolidWorks/El Padre/isen robot 2016-17/support_haut_moteur.SLDPRT

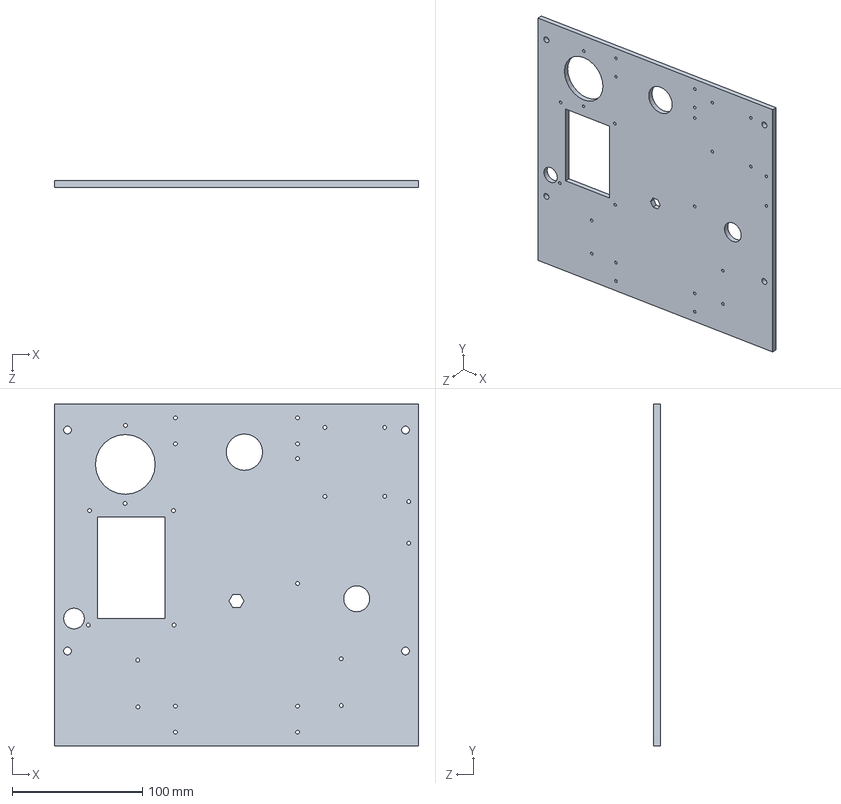
[picture p163: CAD file, 2017-04-14]
SolidWorks/El Padre/isen robot 2016-17/support_haut_moteur.SLDPRT
280.0 x 263.0 x 5.00 mm
