nsobczak/CoupeDeFrance/SolidWorks/El Padre/Base_roulante/Assemblage popcorn/Pièces/Tube/Tube1.SLDPRT

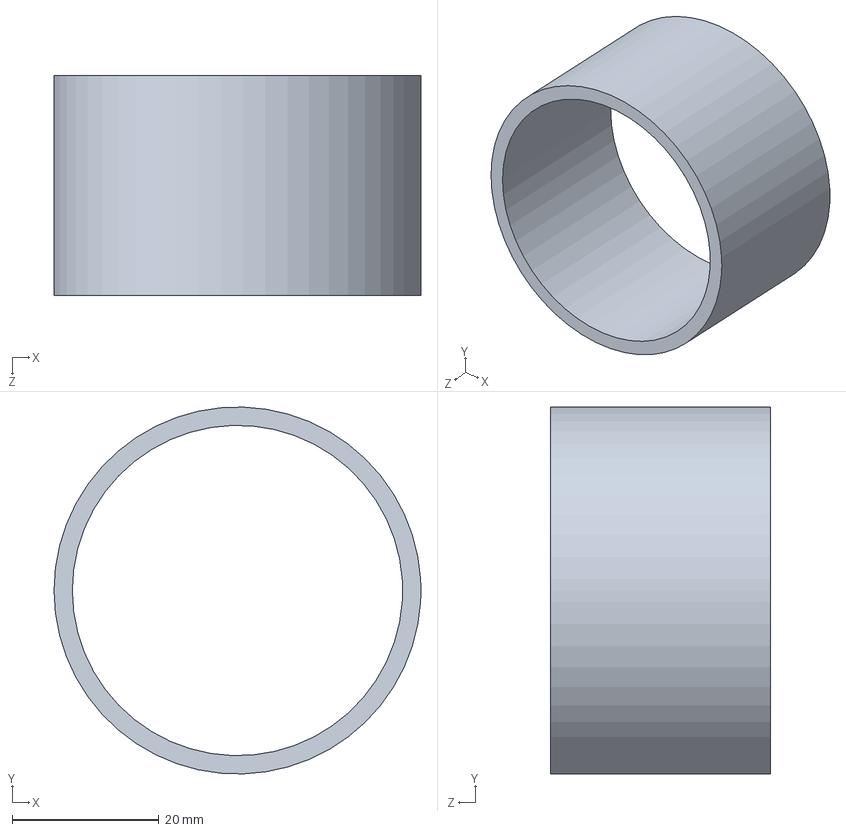
[picture p165: CAD file, 2017-02-13]
SolidWorks/El Padre/Base_roulante/Assemblage popcorn/Pièces/Tube/Tube1.SLDPRT
50.0 x 50.0 x 30.0 mm
