nsobczak/CoupeDeFrance/SolidWorks/El Padre/Base_roulante/Base du robot/bille_porteuse/contour_roulement.SLDPRT

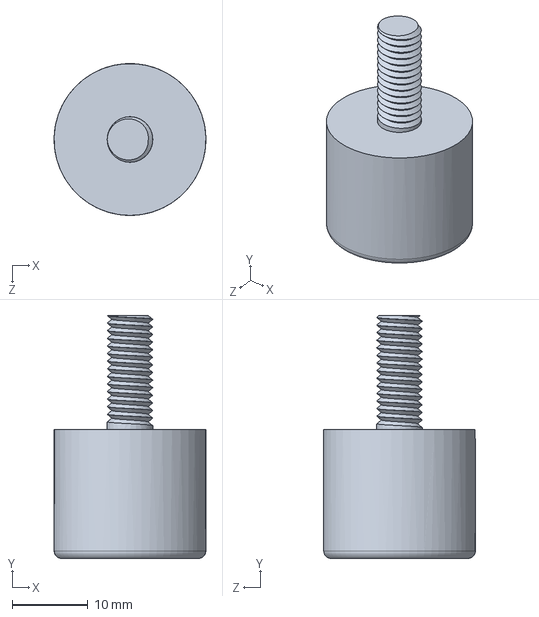
[picture p166: CAD file, 2017-02-13]
SolidWorks/El Padre/Base_roulante/Base du robot/bille_porteuse/contour_roulement.SLDPRT
20.0 x 32.0 x 20.0 mm
