nsobczak/CoupeDeFrance/SolidWorks/El Padre/Base_roulante/Claps/AntiClapsFinal/tigeCLAP.SLDPRT

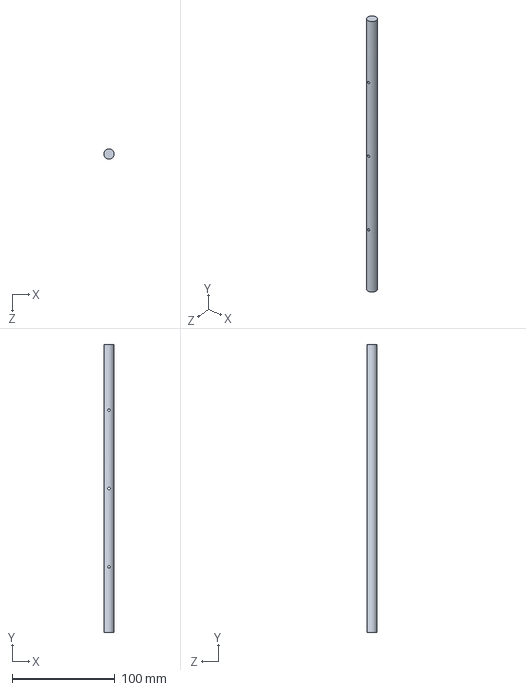
[picture p167: CAD file, 2017-02-13]
SolidWorks/El Padre/Base_roulante/Claps/AntiClapsFinal/tigeCLAP.SLDPRT
10.0 x 280.0 x 10.0 mm
