nsobczak/CoupeDeFrance/SolidWorks/El Padre/isen robot 2016-17/Funny Action/support servo moteur 1.SLDPRT

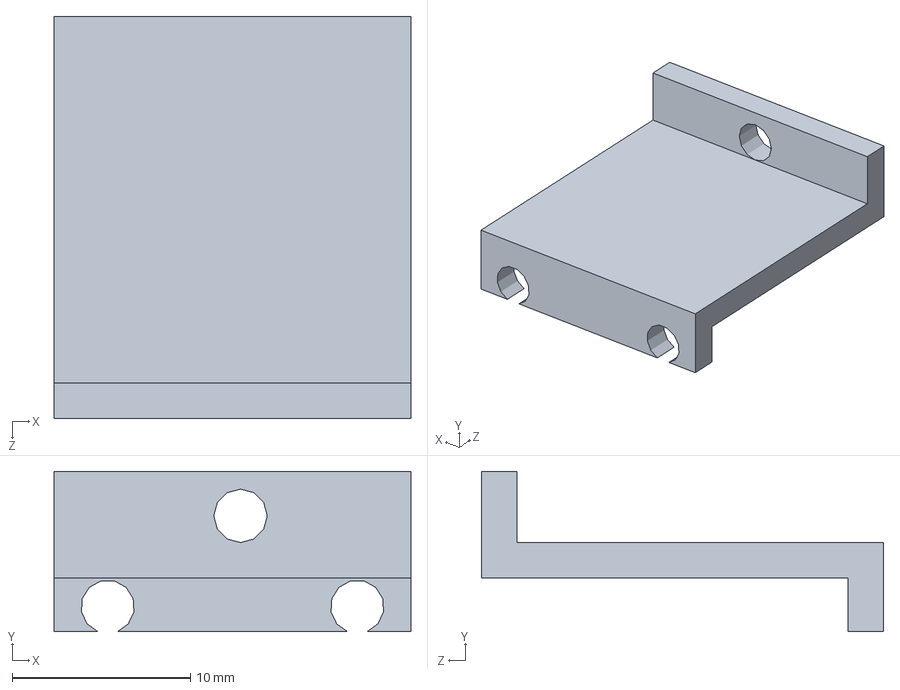
[picture p168: CAD file, 2017-03-29]
SolidWorks/El Padre/isen robot 2016-17/Funny Action/support servo moteur 1.SLDPRT
20.0 x 9.00 x 22.5 mm
