nsobczak/CoupeDeFrance/SolidWorks/El Padre/isen robot 2016-17/Pince/Pièce12.SLDPRT

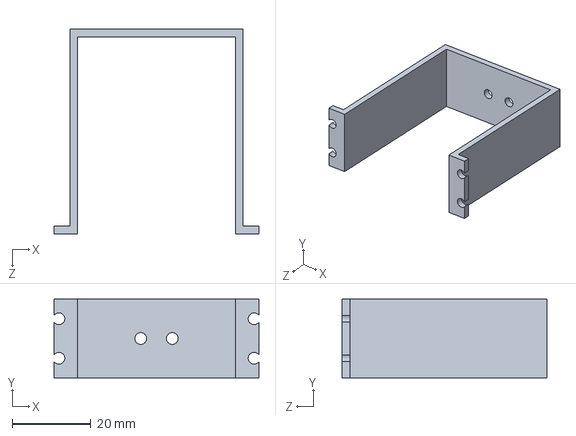
[picture p169: CAD file, 2017-02-13]
SolidWorks/El Padre/isen robot 2016-17/Pince/Pièce12.SLDPRT
52.0 x 20.0 x 52.0 mm
