nsobczak/CoupeDeFrance/SolidWorks/El Padre/isen robot 2016-17/support moteur pas a pas.SLDPRT

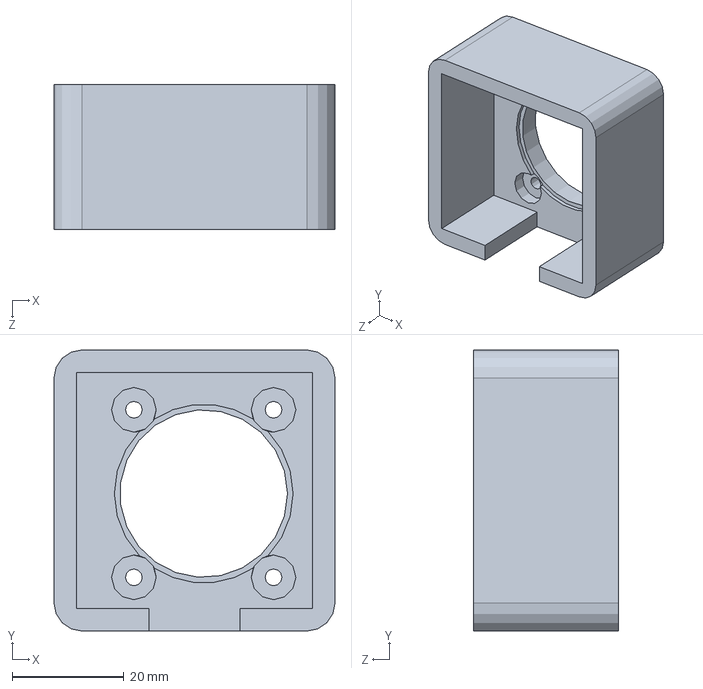
[picture p170: CAD file, 2017-04-14]
SolidWorks/El Padre/isen robot 2016-17/support moteur pas a pas.SLDPRT
50.3 x 50.3 x 26.0 mm
