nsobczak/CoupeDeFrance/SolidWorks/El Padre/Plans découpeuse laser des différentes faces/FACE_EL_PADRE.DXF

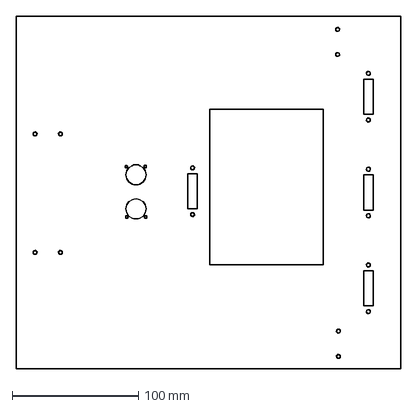
[picture p171: CAD file, 2017-04-14]
SolidWorks/El Padre/Plans découpeuse laser des différentes faces/FACE_EL_PADRE.DXF
305.0 x 280.0 mm
