nsobczak/CoupeDeFrance/SolidWorks/El Padre/Base_roulante/assemblage_spot2/engrenage_gros_1.SLDPRT

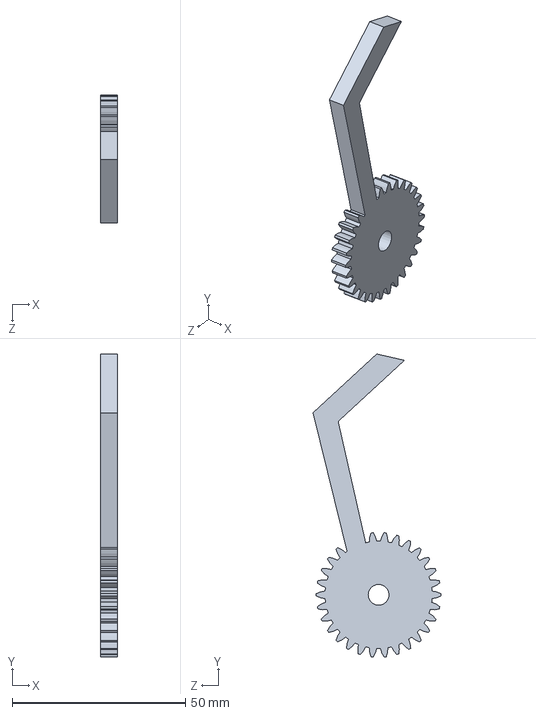
[picture p172: CAD file, 2017-02-13]
SolidWorks/El Padre/Base_roulante/assemblage_spot2/engrenage_gros_1.SLDPRT
5.00 x 87.4 x 36.9 mm
