nsobczak/CoupeDeFrance/SolidWorks/El Padre/Base_roulante/Base du robot/EQUERRE.SLDPRT

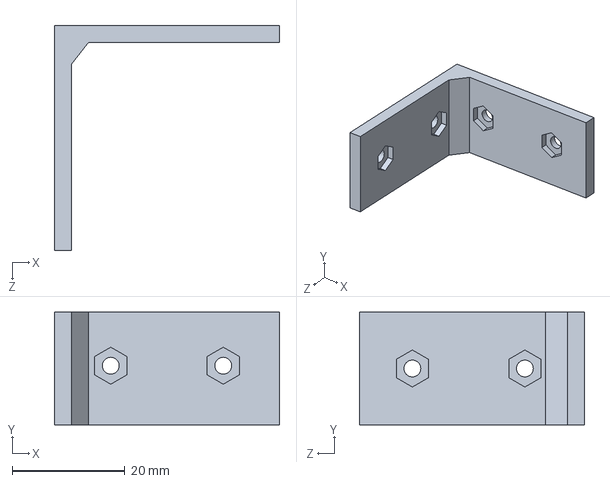
[picture p173: CAD file, 2017-05-04]
SolidWorks/El Padre/Base_roulante/Base du robot/EQUERRE.SLDPRT
40.0 x 20.0 x 40.0 mm
