nsobczak/CoupeDeFrance/SolidWorks/El Padre/Base_roulante/Bloc moteur/roulement_6_15_5.sldprt

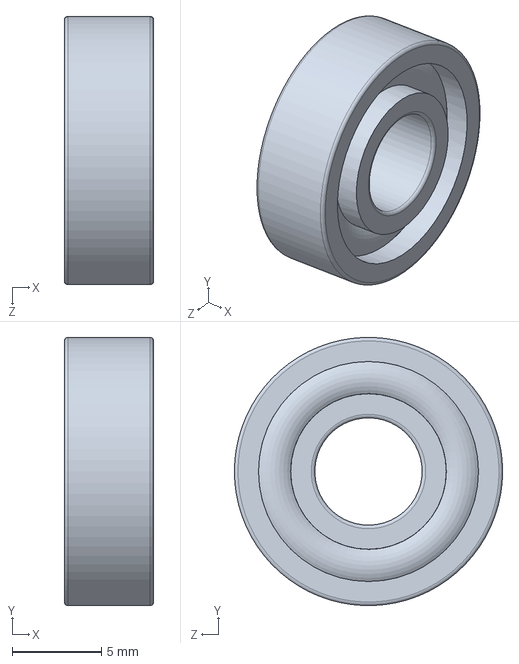
[picture p174: CAD file, 2017-02-13]
SolidWorks/El Padre/Base_roulante/Bloc moteur/roulement_6_15_5.sldprt
5.00 x 15.0 x 15.0 mm
