nsobczak/CoupeDeFrance/SolidWorks/El Padre/isen robot 2016-17/Funny Action/lanceur.SLDPRT

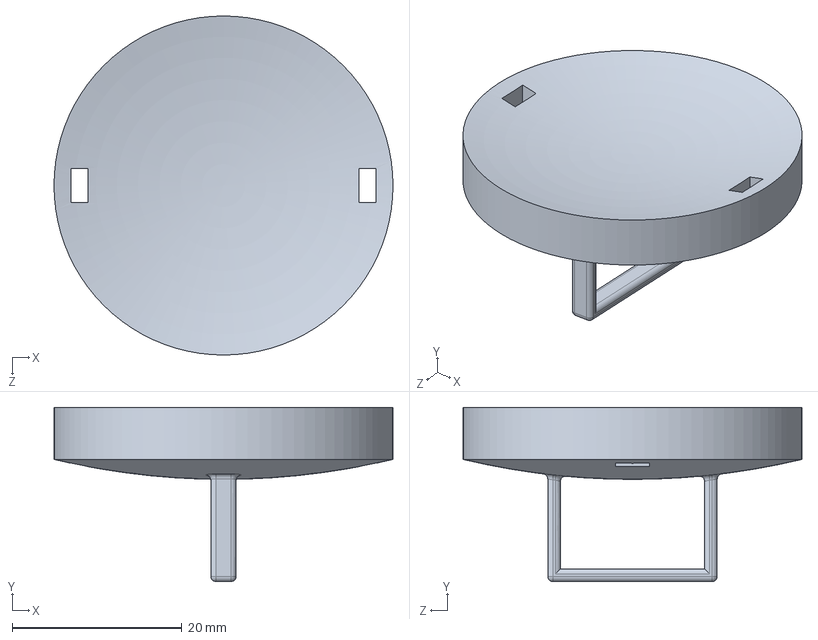
[picture p175: CAD file, 2017-03-29]
SolidWorks/El Padre/isen robot 2016-17/Funny Action/lanceur.SLDPRT
40.0 x 20.5 x 40.0 mm
