nsobczak/CoupeDeFrance/SolidWorks/El Padre/isen robot 2016-17/Pince/Pièce3.SLDPRT

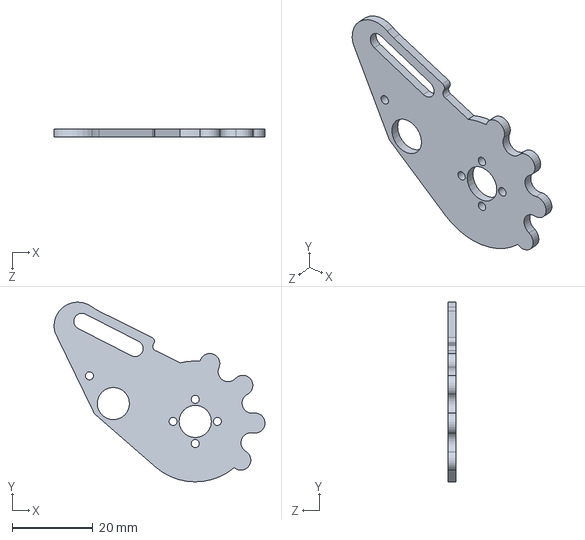
[picture p176: CAD file, 2017-02-13]
SolidWorks/El Padre/isen robot 2016-17/Pince/Pièce3.SLDPRT
52.4 x 44.6 x 2.00 mm
