nsobczak/CoupeDeFrance/SolidWorks/El Padre/Plans découpeuse laser des différentes faces/PROTEGE FACE.DXF

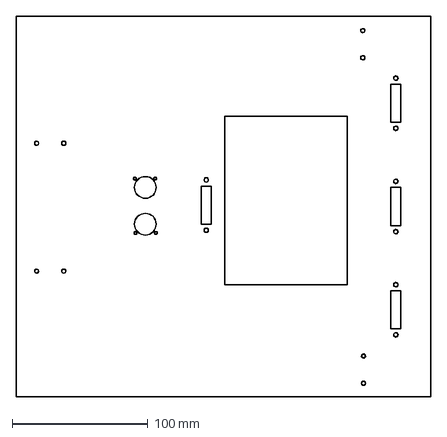
[picture p177: CAD file, 2017-04-14]
SolidWorks/El Padre/Plans découpeuse laser des différentes faces/PROTEGE FACE.DXF
305.0 x 280.0 mm
