nsobczak/CoupeDeFrance/SolidWorks/El Padre/Base_roulante/assemblage_spot2/plaque_pivot_servo.SLDPRT

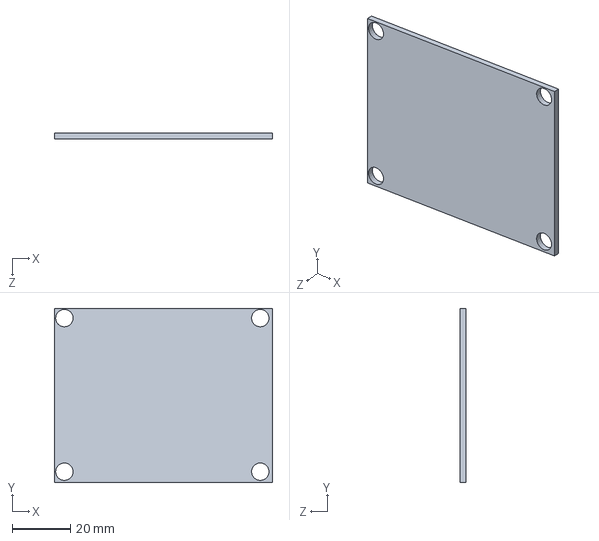
[picture p178: CAD file, 2017-02-13]
SolidWorks/El Padre/Base_roulante/assemblage_spot2/plaque_pivot_servo.SLDPRT
75.0 x 60.0 x 2.00 mm
