nsobczak/CoupeDeFrance/SolidWorks/El Padre/Base_roulante/Base du robot/support moteur pas a pas.SLDPRT

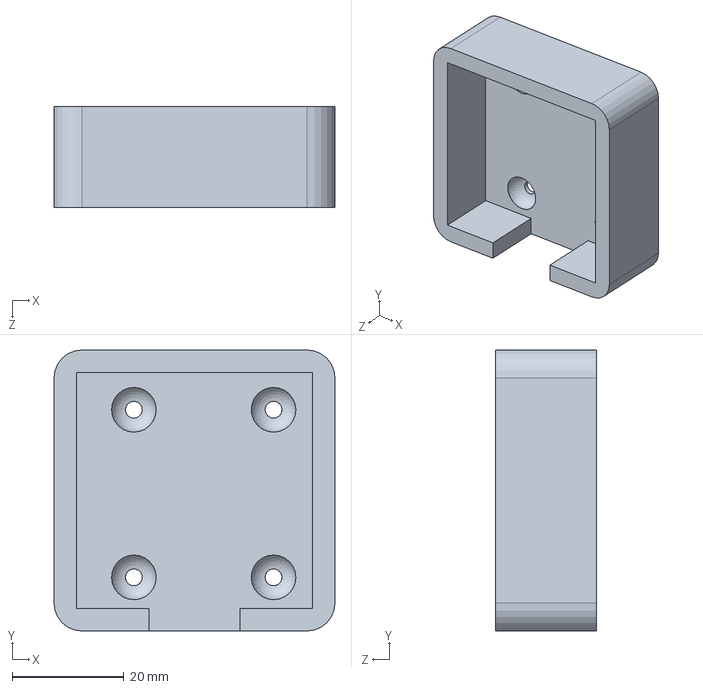
[picture p179: CAD file, 2017-04-14]
SolidWorks/El Padre/Base_roulante/Base du robot/support moteur pas a pas.SLDPRT
50.3 x 50.3 x 18.0 mm
