nsobczak/CoupeDeFrance/SolidWorks/El Padre/Base_roulante/Bloc moteur/support central.SLDPRT

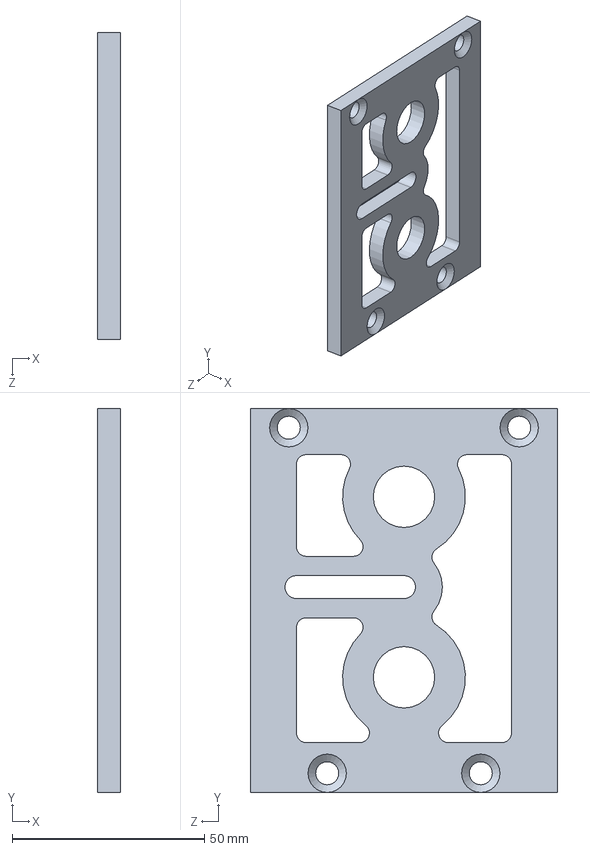
[picture p180: CAD file, 2017-02-13]
SolidWorks/El Padre/Base_roulante/Bloc moteur/support central.SLDPRT
6.00 x 100.0 x 80.0 mm
