nsobczak/CoupeDeFrance/SolidWorks/El Padre/Base_roulante/Claps/AntiClapsFinal/Vis 1.SLDPRT

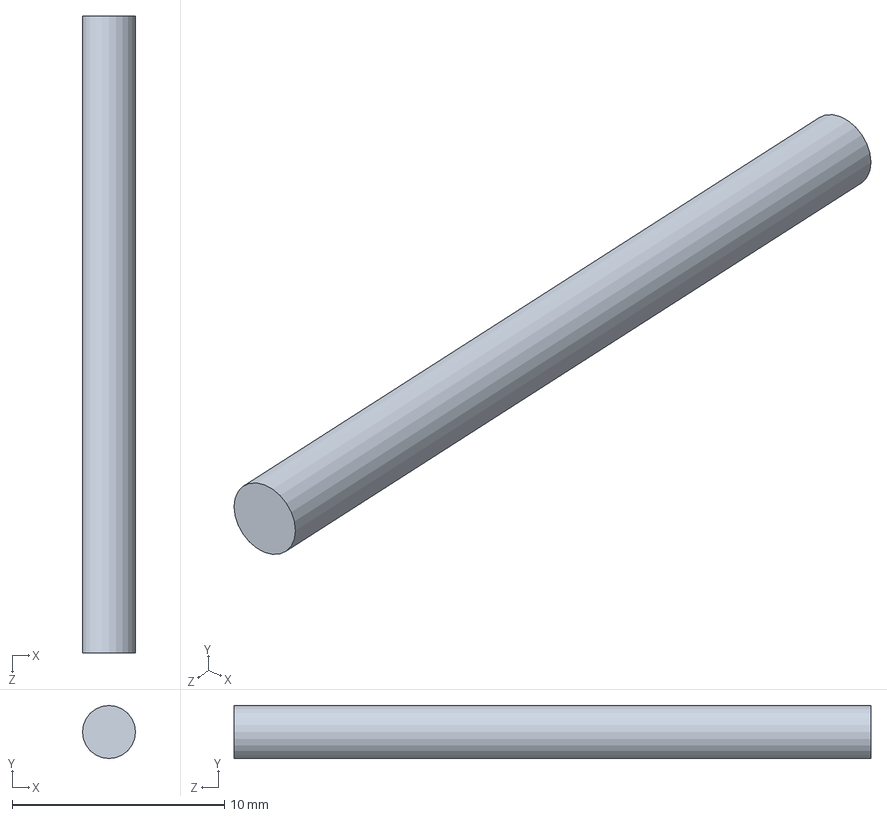
[picture p181: CAD file, 2017-02-13]
SolidWorks/El Padre/Base_roulante/Claps/AntiClapsFinal/Vis 1.SLDPRT
2.50 x 2.50 x 30.0 mm
