nsobczak/CoupeDeFrance/SolidWorks/El Padre/isen robot 2016-17/Pince/Pièce6.SLDPRT

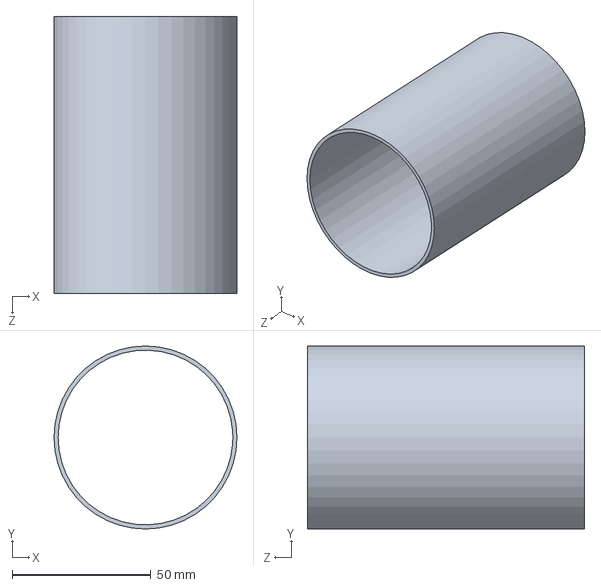
[picture p182: CAD file, 2017-02-13]
SolidWorks/El Padre/isen robot 2016-17/Pince/Pièce6.SLDPRT
66.0 x 66.0 x 100.0 mm
