nsobczak/CoupeDeFrance/SolidWorks/El Padre/isen robot 2016-17/support-milieu_droite.SLDPRT

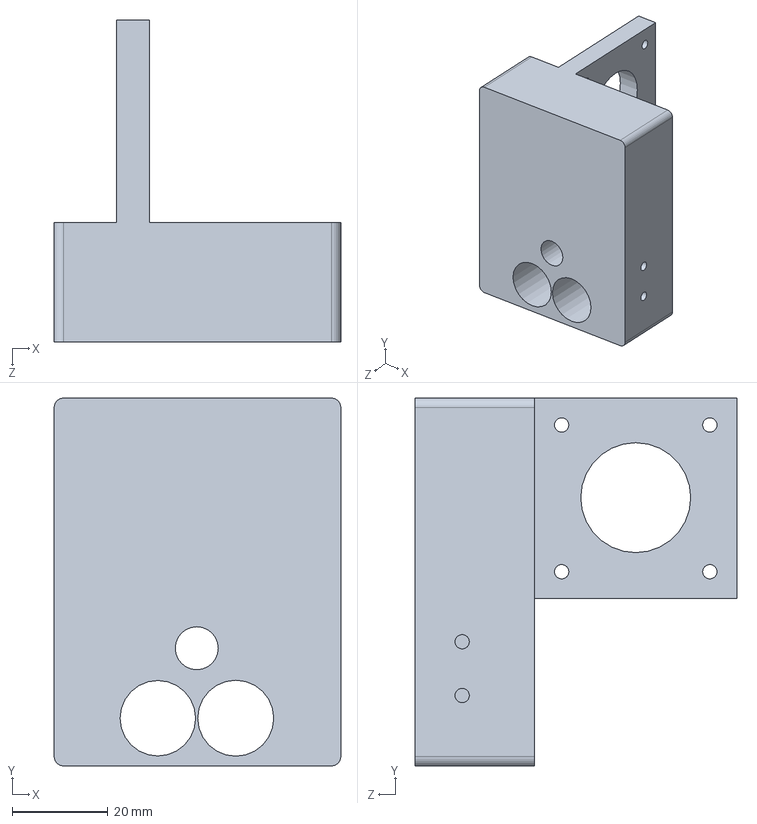
[picture p183: CAD file, 2017-04-03]
SolidWorks/El Padre/isen robot 2016-17/support-milieu_droite.SLDPRT
60.0 x 77.0 x 67.3 mm
