nsobczak/CoupeDeFrance/SolidWorks/El Padre/Base_roulante/assemblage_spot2/vis_sans_fin.SLDPRT

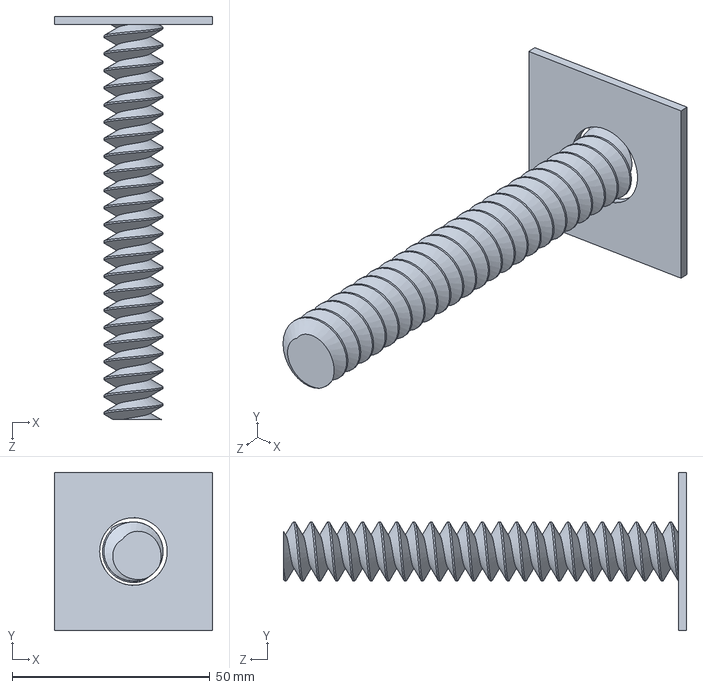
[picture p184: CAD file, 2017-02-13]
SolidWorks/El Padre/Base_roulante/assemblage_spot2/vis_sans_fin.SLDPRT
40.0 x 40.0 x 102.0 mm
