nsobczak/CoupeDeFrance/SolidWorks/El Padre/Base_roulante/Base du robot/EQUERRE SOCLE.SLDPRT

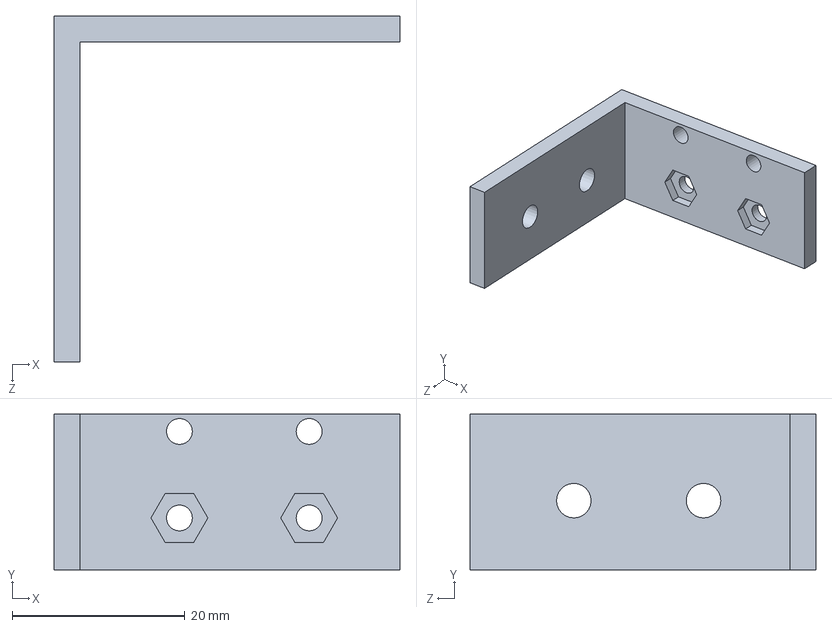
[picture p185: CAD file, 2017-04-03]
SolidWorks/El Padre/Base_roulante/Base du robot/EQUERRE SOCLE.SLDPRT
40.0 x 18.0 x 40.0 mm
