nsobczak/CoupeDeFrance/SolidWorks/El Padre/Base_roulante/Bloc moteur/pneu.SLDPRT

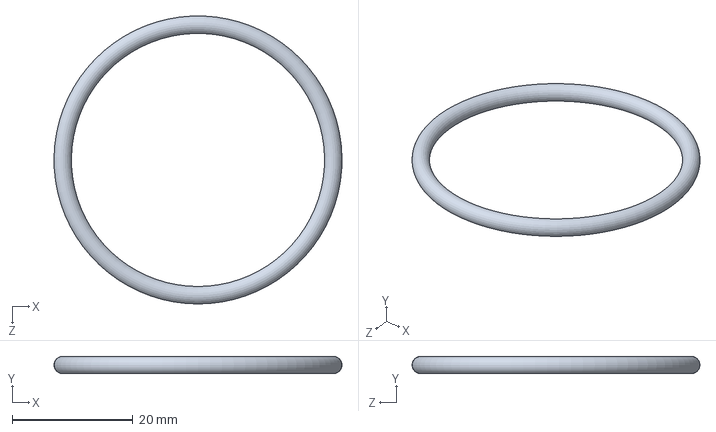
[picture p186: CAD file, 2017-02-13]
SolidWorks/El Padre/Base_roulante/Bloc moteur/pneu.SLDPRT
47.7 x 2.90 x 47.7 mm
