nsobczak/CoupeDeFrance/SolidWorks/El Padre/Base_roulante/Claps/AntiClapsFinal/tigeSupport.SLDPRT

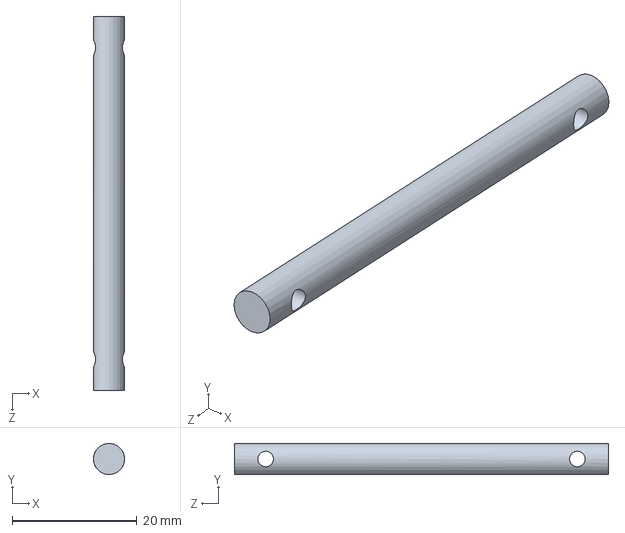
[picture p187: CAD file, 2017-02-13]
SolidWorks/El Padre/Base_roulante/Claps/AntiClapsFinal/tigeSupport.SLDPRT
5.00 x 5.00 x 60.0 mm
