nsobczak/CoupeDeFrance/SolidWorks/El Padre/isen robot 2016-17/Funny Action/servo moteur.SLDPRT

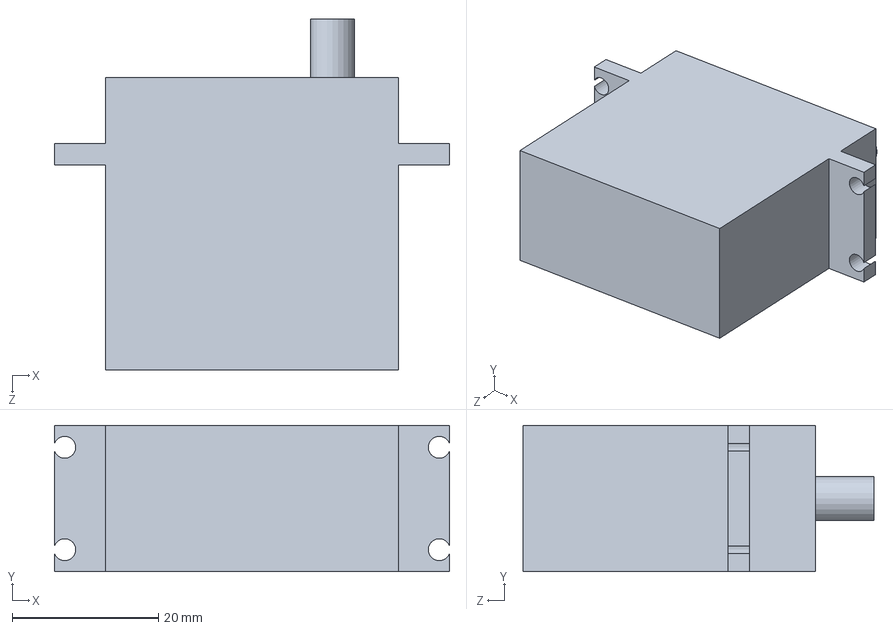
[picture p188: CAD file, 2017-03-29]
SolidWorks/El Padre/isen robot 2016-17/Funny Action/servo moteur.SLDPRT
54.0 x 20.0 x 48.0 mm
