nsobczak/CoupeDeFrance/SolidWorks/El Padre/Base_roulante/assemblage_spot2/support_servomoteur.SLDPRT

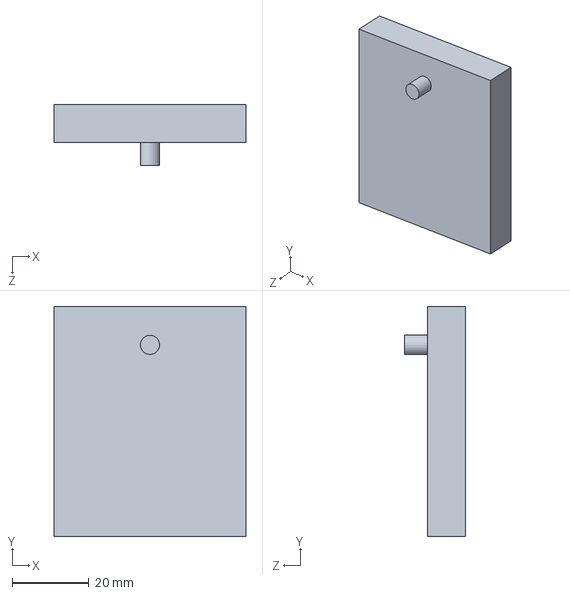
[picture p189: CAD file, 2017-02-13]
SolidWorks/El Padre/Base_roulante/assemblage_spot2/support_servomoteur.SLDPRT
50.0 x 60.0 x 16.0 mm
