nsobczak/CoupeDeFrance/SolidWorks/El Padre/Base_roulante/Bloc moteur/support codeuse modifie.SLDPRT

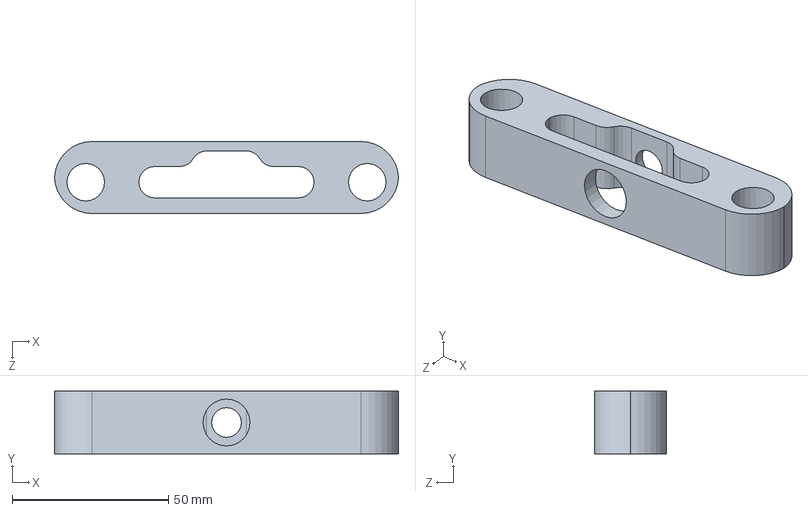
[picture p190: CAD file, 2017-02-13]
SolidWorks/El Padre/Base_roulante/Bloc moteur/support codeuse modifie.SLDPRT
110.0 x 20.0 x 23.0 mm
