nsobczak/CoupeDeFrance/SolidWorks/El Padre/Base_roulante/Claps/AntiClapsFinal/RenfortServomoteur.SLDPRT

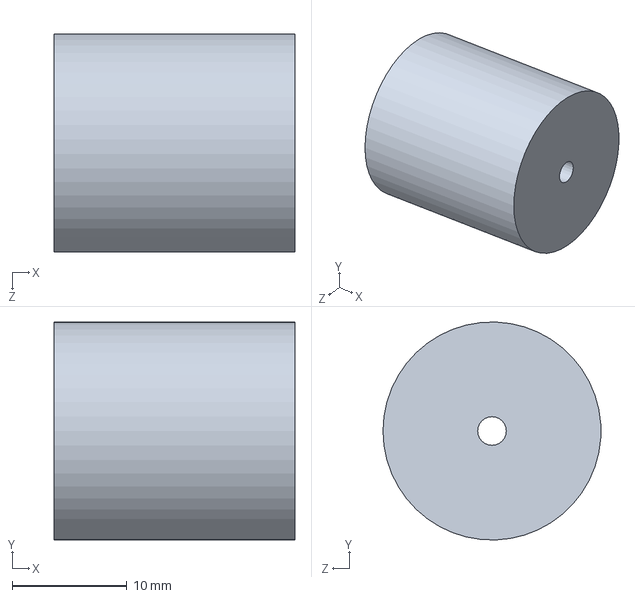
[picture p191: CAD file, 2017-02-13]
SolidWorks/El Padre/Base_roulante/Claps/AntiClapsFinal/RenfortServomoteur.SLDPRT
21.0 x 19.0 x 19.0 mm
