nsobczak/CoupeDeFrance/SolidWorks/El Padre/Base_roulante/cristeo/acroche.STL

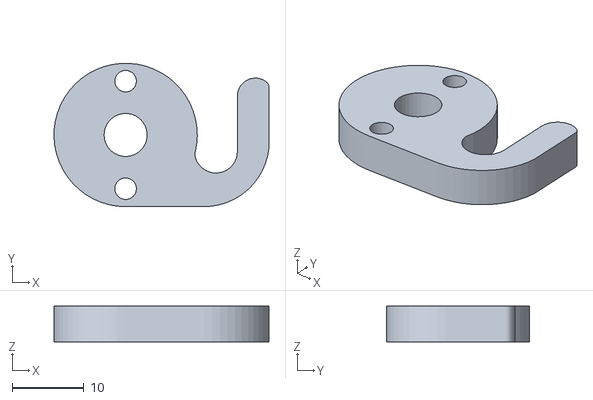
[picture p192: CAD file, 2017-04-03]
SolidWorks/El Padre/Base_roulante/cristeo/acroche.STL
30.0 x 20.0 x 5.00
