nsobczak/CoupeDeFrance/SolidWorks/El Padre/isen robot 2016-17/Pince/Pièce5.SLDPRT

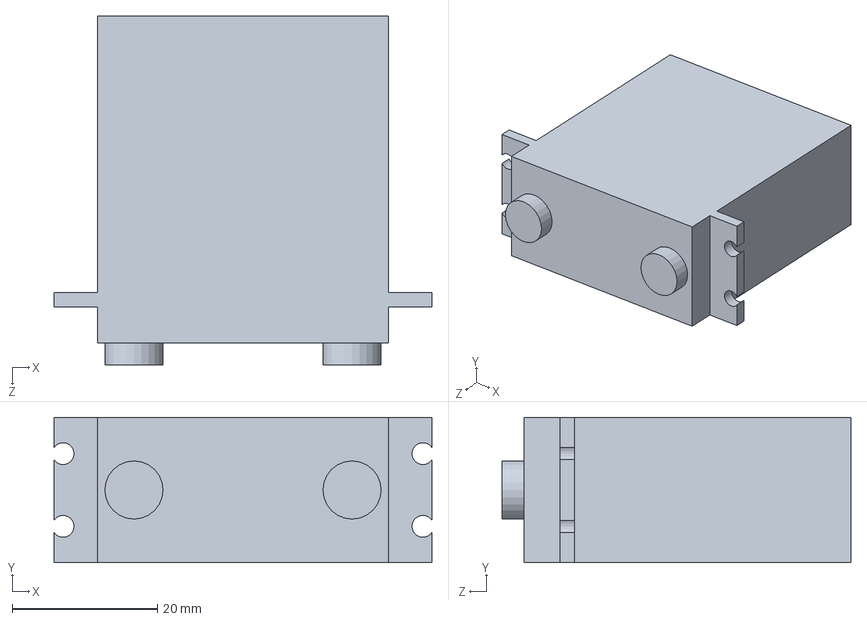
[picture p193: CAD file, 2017-02-13]
SolidWorks/El Padre/isen robot 2016-17/Pince/Pièce5.SLDPRT
52.0 x 20.0 x 48.0 mm
