nsobczak/CoupeDeFrance/SolidWorks/El Padre/isen robot 2016-17/support_haut.SLDPRT

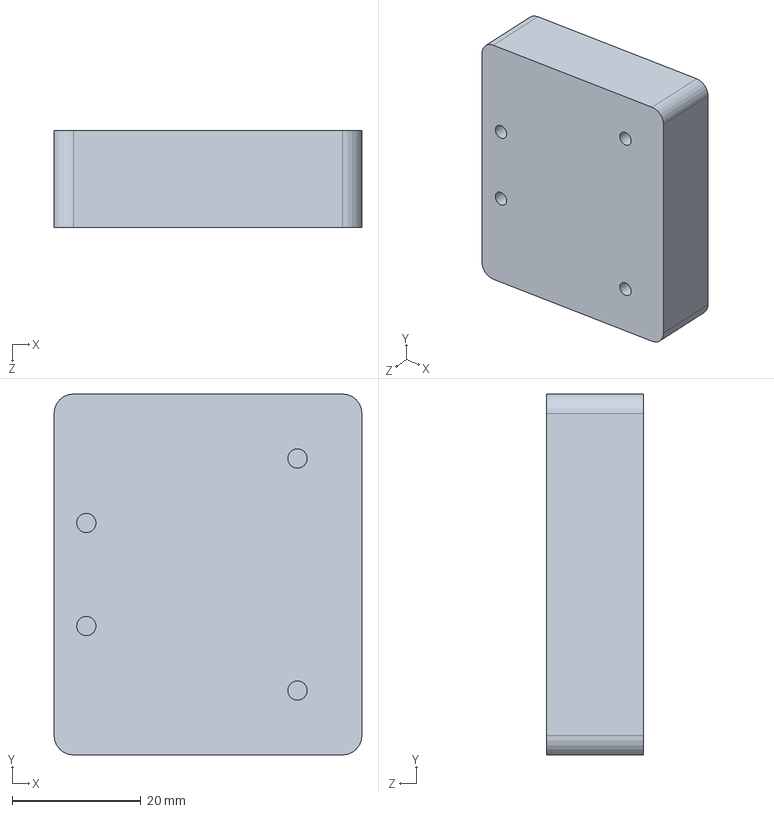
[picture p194: CAD file, 2017-03-29]
SolidWorks/El Padre/isen robot 2016-17/support_haut.SLDPRT
47.7 x 56.0 x 15.0 mm
