nsobczak/CoupeDeFrance/SolidWorks/El Padre/Base_roulante/Bloc moteur/plaqueRoueCodeuse.SLDPRT

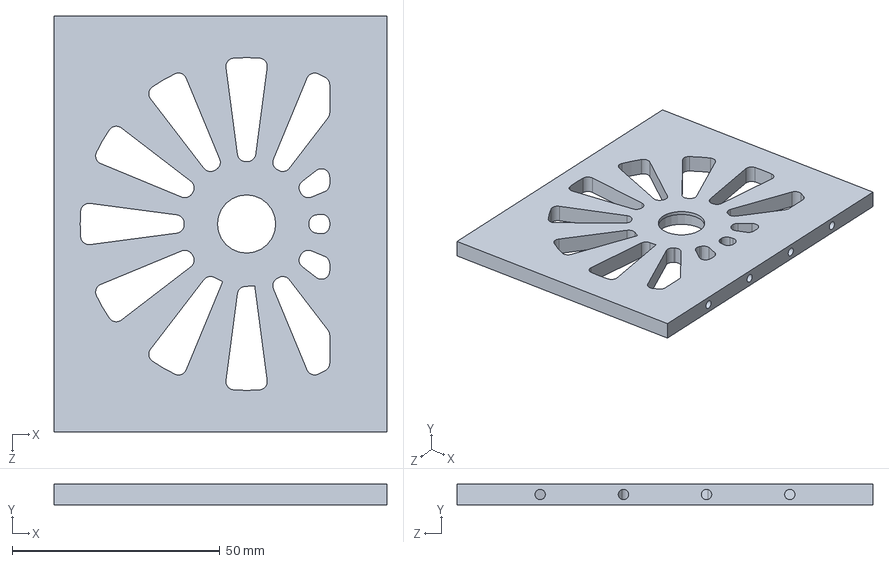
[picture p195: CAD file, 2017-02-13]
SolidWorks/El Padre/Base_roulante/Bloc moteur/plaqueRoueCodeuse.SLDPRT
80.0 x 5.00 x 100.0 mm
