nsobczak/CoupeDeFrance/SolidWorks/El Padre/isen robot 2016-17/Pince/Pièce2.SLDPRT

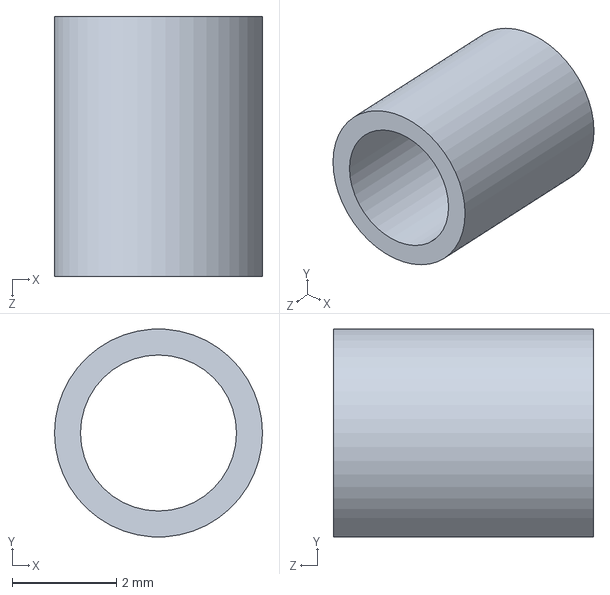
[picture p196: CAD file, 2017-02-13]
SolidWorks/El Padre/isen robot 2016-17/Pince/Pièce2.SLDPRT
4.00 x 3.99 x 5.00 mm
