nsobczak/CoupeDeFrance/SolidWorks/El Padre/isen robot 2016-17/support-milieu_gauche.SLDPRT

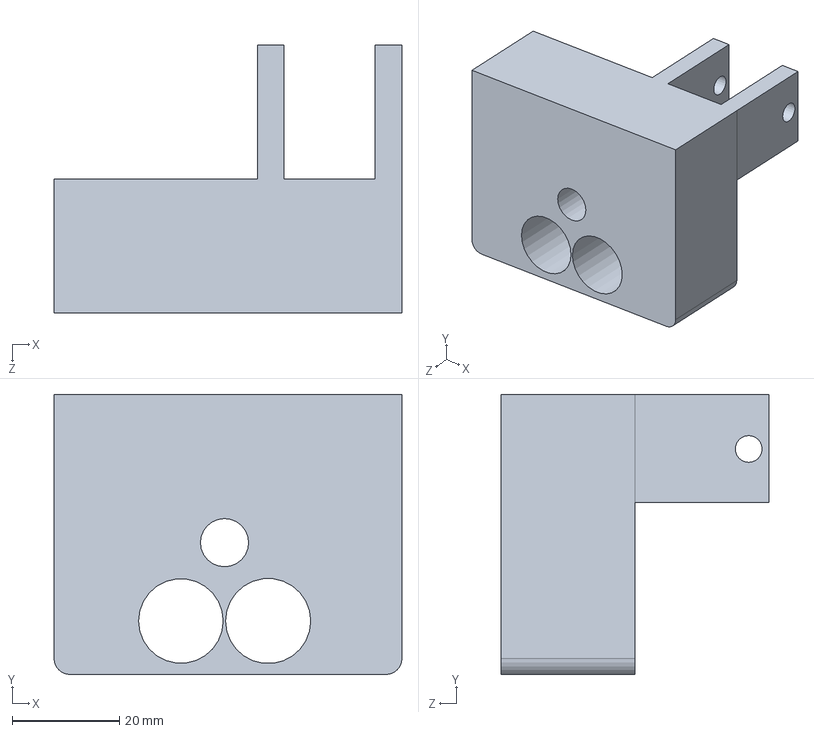
[picture p197: CAD file, 2017-03-29]
SolidWorks/El Padre/isen robot 2016-17/support-milieu_gauche.SLDPRT
65.0 x 52.3 x 50.0 mm
