nsobczak/CoupeDeFrance/SolidWorks/El Padre/Base_roulante/assemblage_spot2/plaque_engrenage_avec_trou.SLDPRT

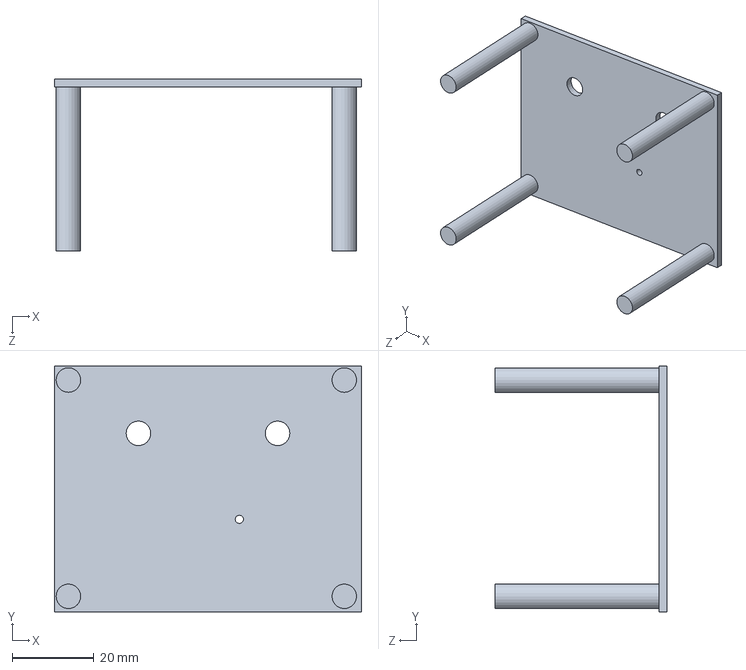
[picture p198: CAD file, 2017-02-13]
SolidWorks/El Padre/Base_roulante/assemblage_spot2/plaque_engrenage_avec_trou.SLDPRT
75.0 x 60.0 x 42.0 mm
