nsobczak/CoupeDeFrance/SolidWorks/El Padre/isen robot 2016-17/Pince/piece pince.SLDPRT

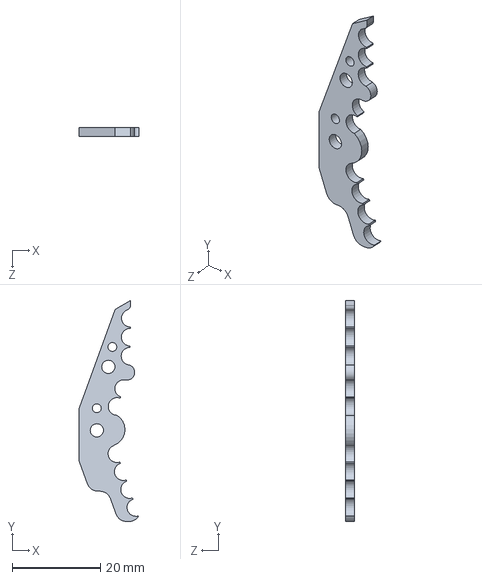
[picture p199: CAD file, 2017-02-13]
SolidWorks/El Padre/isen robot 2016-17/Pince/piece pince.SLDPRT
13.5 x 50.0 x 2.00 mm
