nsobczak/CoupeDeFrance/SolidWorks/El Padre/isen robot 2016-17/support8moteur.SLDPRT

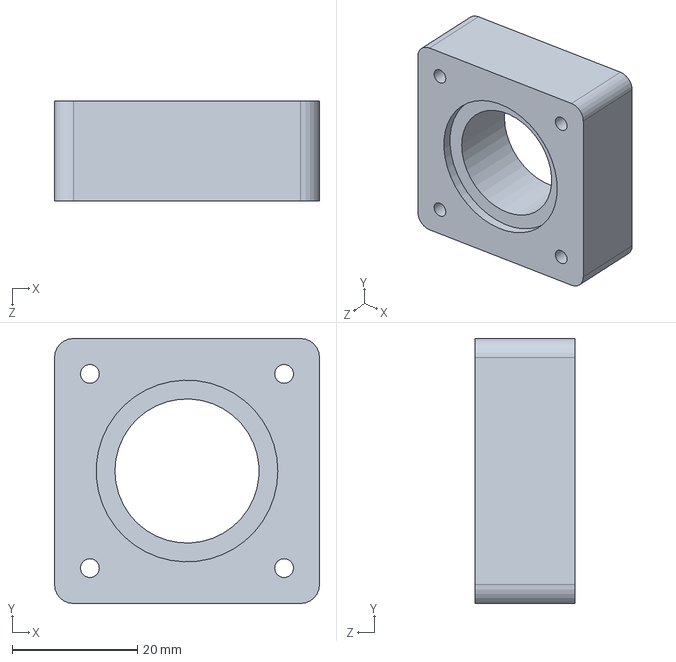
[picture p200: CAD file, 2017-03-29]
SolidWorks/El Padre/isen robot 2016-17/support8moteur.SLDPRT
42.3 x 42.3 x 16.0 mm
