nsobczak/CoupeDeFrance/SolidWorks/El Padre/Base_roulante/assemblage_spot2/moteur_vis.SLDPRT

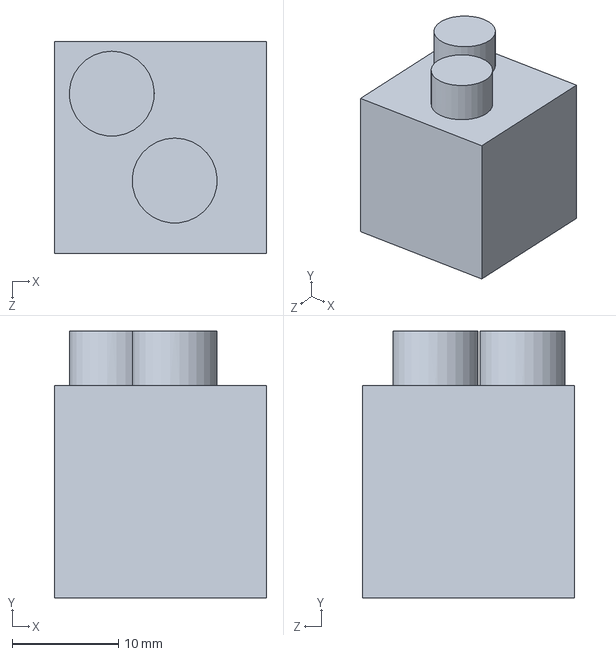
[picture p201: CAD file, 2017-02-13]
SolidWorks/El Padre/Base_roulante/assemblage_spot2/moteur_vis.SLDPRT
20.0 x 25.1 x 20.0 mm
