nsobczak/CoupeDeFrance/SolidWorks/El Padre/Base_roulante/Base du robot/Profile.SLDPRT

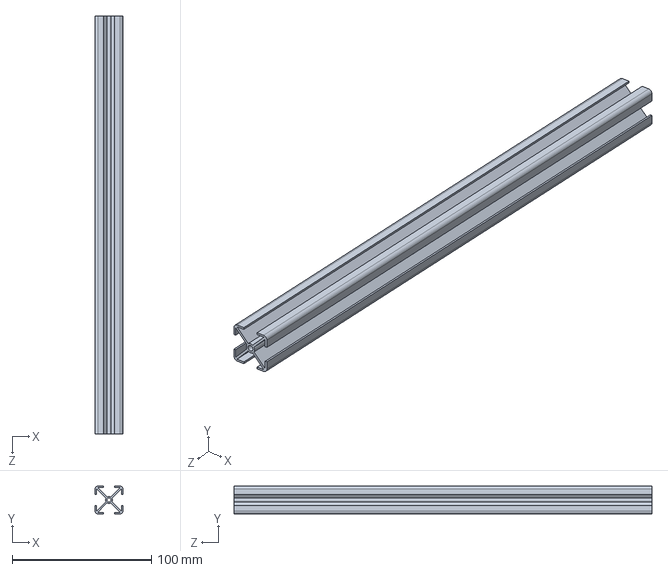
[picture p202: CAD file, 2017-03-29]
SolidWorks/El Padre/Base_roulante/Base du robot/Profile.SLDPRT
20.0 x 20.0 x 300.0 mm
