nsobczak/CoupeDeFrance/SolidWorks/El Padre/isen robot 2016-17/ENSEMBLE CHARIOT DEPLACEMENT_1.SLDPRT

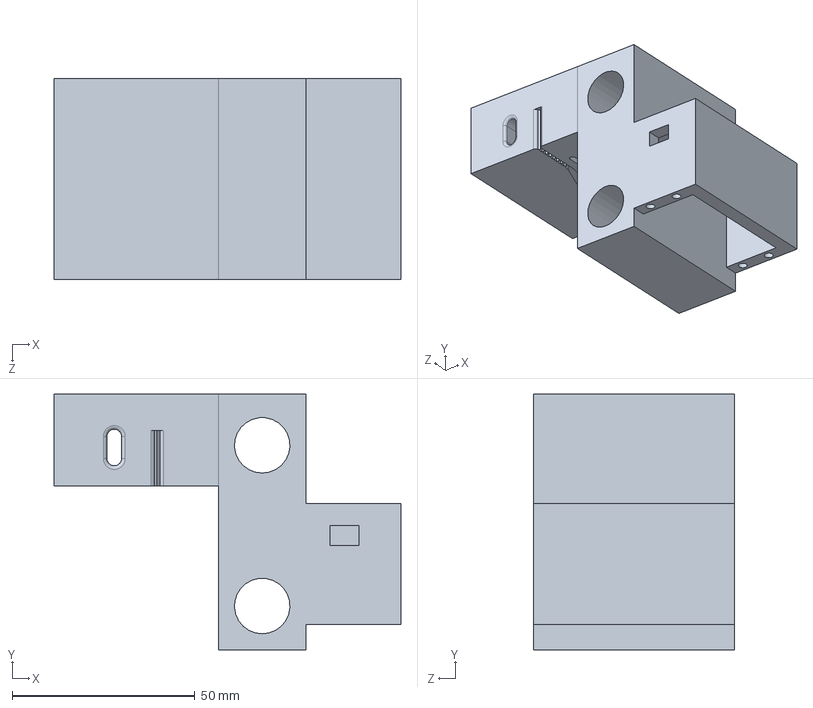
[picture p203: CAD file, 2017-03-29]
SolidWorks/El Padre/isen robot 2016-17/ENSEMBLE CHARIOT DEPLACEMENT_1.SLDPRT
95.0 x 70.0 x 55.0 mm
