nsobczak/CoupeDeFrance/SolidWorks/El Padre/isen robot 2016-17/Pince/Pièce4.SLDPRT

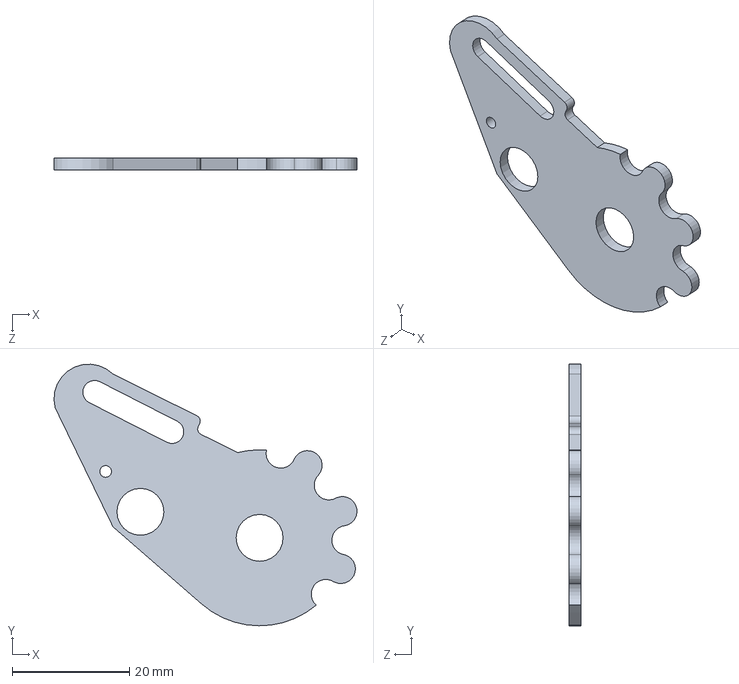
[picture p204: CAD file, 2017-02-13]
SolidWorks/El Padre/isen robot 2016-17/Pince/Pièce4.SLDPRT
51.7 x 44.6 x 2.00 mm
