nsobczak/CoupeDeFrance/SolidWorks/El Padre/Base_roulante/assemblage_spot2/engrenage_petit_1.SLDPRT

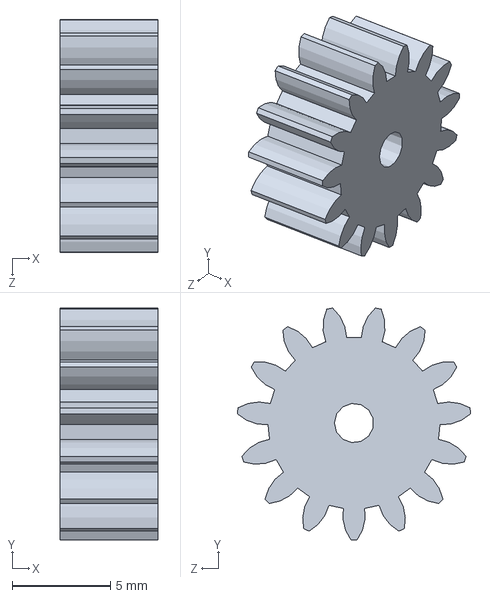
[picture p205: CAD file, 2017-02-13]
SolidWorks/El Padre/Base_roulante/assemblage_spot2/engrenage_petit_1.SLDPRT
5.00 x 11.8 x 11.9 mm
