nsobczak/CoupeDeFrance/SolidWorks/El Padre/Base_roulante/Base du robot/base_v3.SLDPRT

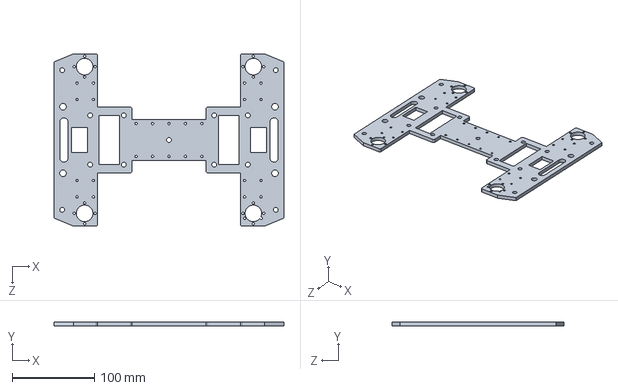
[picture p206: CAD file, 2017-03-29]
SolidWorks/El Padre/Base_roulante/Base du robot/base_v3.SLDPRT
280.0 x 5.00 x 210.0 mm
