nsobczak/CoupeDeFrance/SolidWorks/El Padre/Base_roulante/Bloc moteur/support moteur.SLDPRT

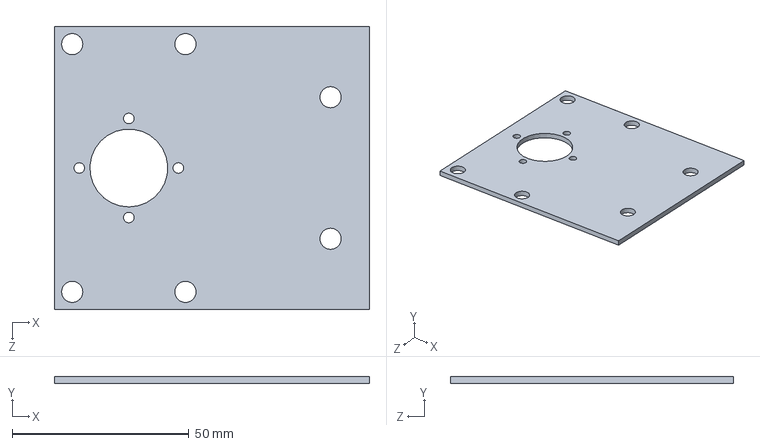
[picture p207: CAD file, 2017-02-13]
SolidWorks/El Padre/Base_roulante/Bloc moteur/support moteur.SLDPRT
89.0 x 2.00 x 80.0 mm
