nsobczak/CoupeDeFrance/SolidWorks/El Padre/Base_roulante/Base du robot/haut.SLDPRT

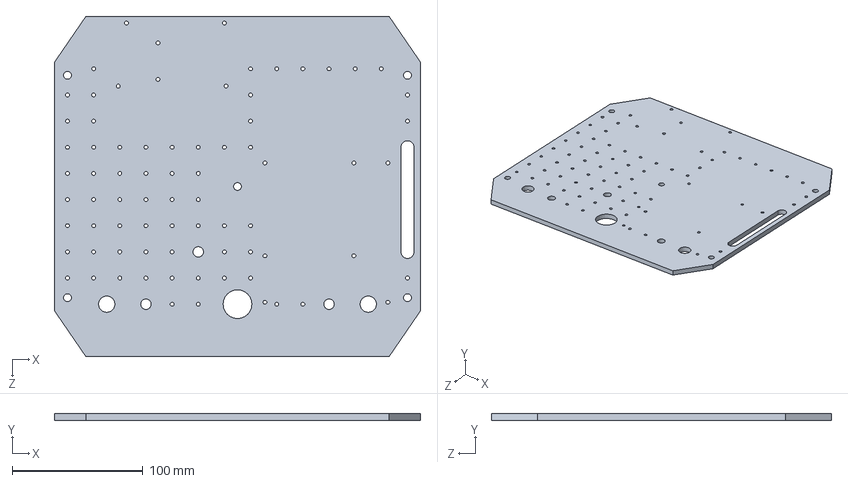
[picture p208: CAD file, 2017-02-13]
SolidWorks/El Padre/Base_roulante/Base du robot/haut.SLDPRT
280.0 x 5.00 x 260.0 mm
