nsobczak/CoupeDeFrance/SolidWorks/El Padre/Base_roulante/Bloc moteur/Straight Miter Gear_ISO.sldprt

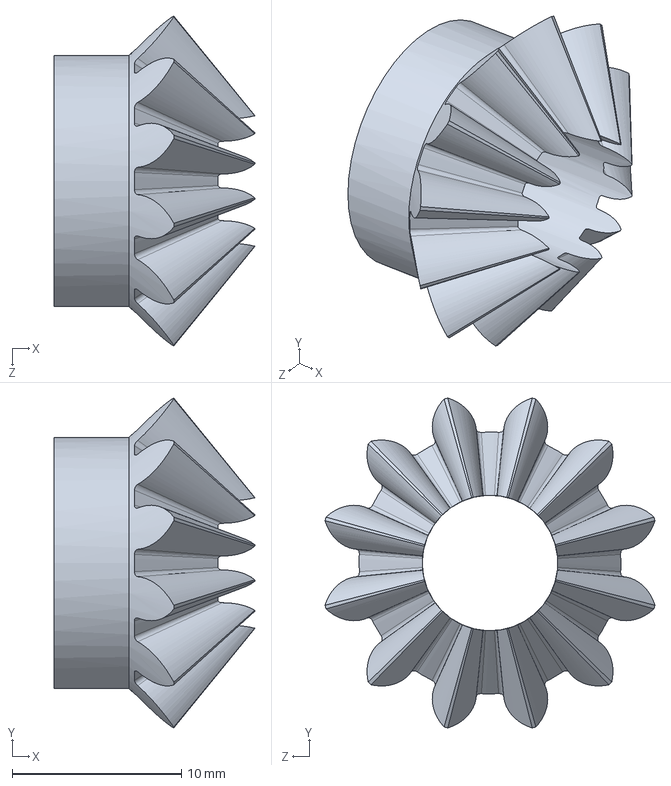
[picture p209: CAD file, 2017-02-13]
SolidWorks/El Padre/Base_roulante/Bloc moteur/Straight Miter Gear_ISO.sldprt
11.8 x 19.5 x 19.5 mm
