nsobczak/CoupeDeFrance/SolidWorks/El Padre/Base_roulante/Base du robot/Base_finale.SLDPRT

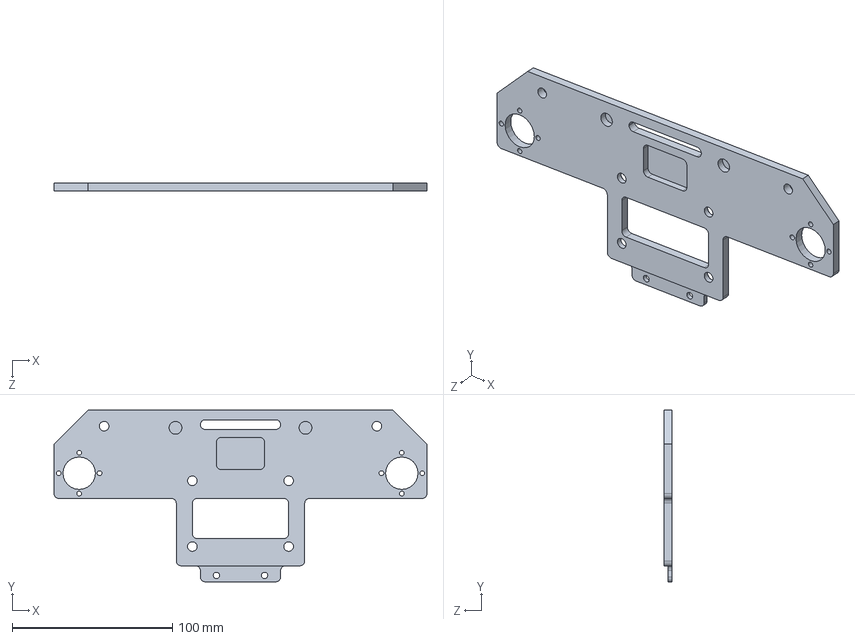
[picture p210: CAD file, 2017-02-13]
SolidWorks/El Padre/Base_roulante/Base du robot/Base_finale.SLDPRT
232.4 x 107.0 x 5.00 mm
