nsobczak/CoupeDeFrance/SolidWorks/El Padre/Base_roulante/Bloc moteur/piecedejonctiondessoususinage.SLDPRT

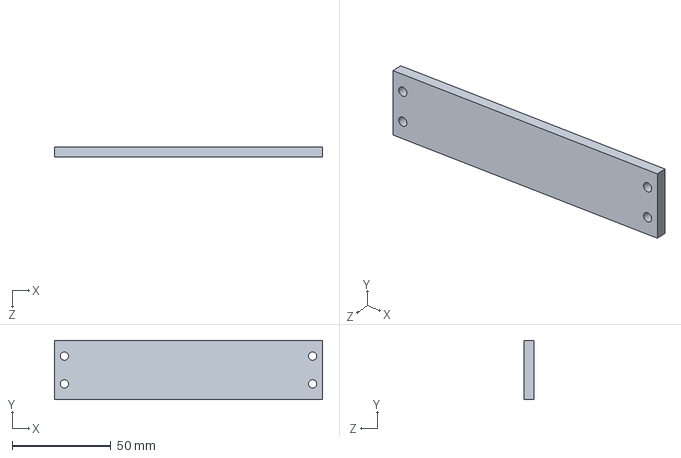
[picture p211: CAD file, 2017-02-13]
SolidWorks/El Padre/Base_roulante/Bloc moteur/piecedejonctiondessoususinage.SLDPRT
135.4 x 30.0 x 5.00 mm
