nsobczak/CoupeDeFrance/SolidWorks/El Padre/isen robot 2016-17/Pince/e6.SLDPRT

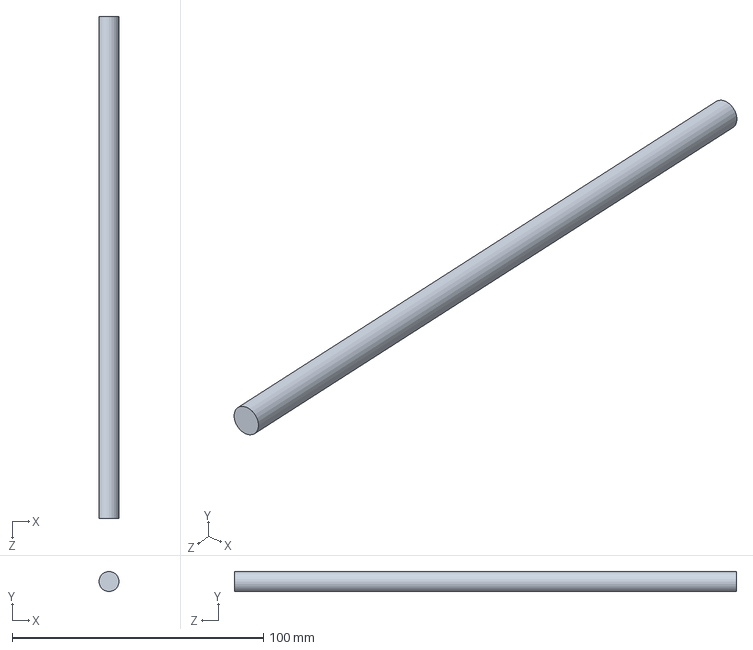
[picture p212: CAD file, 2017-02-13]
SolidWorks/El Padre/isen robot 2016-17/Pince/e6.SLDPRT
8.00 x 8.00 x 200.0 mm
