nsobczak/CoupeDeFrance/SolidWorks/El Padre/isen robot 2016-17/zz.SLDPRT

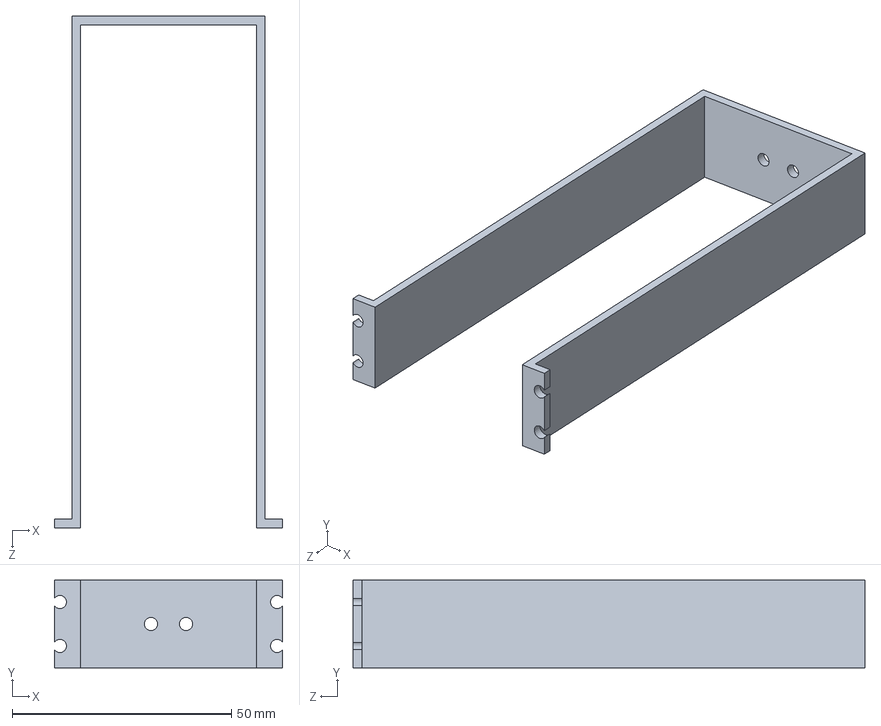
[picture p213: CAD file, 2017-02-13]
SolidWorks/El Padre/isen robot 2016-17/zz.SLDPRT
52.0 x 20.0 x 116.7 mm
