nsobczak/CoupeDeFrance/SolidWorks/El Padre/Base_roulante/Base du robot/base_modifiee.SLDPRT

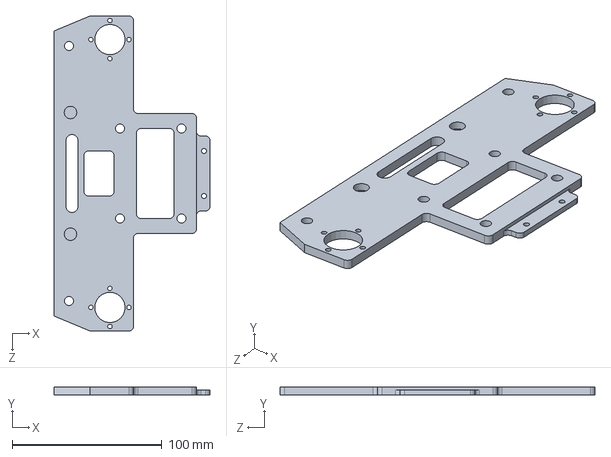
[picture p214: CAD file, 2017-02-13]
SolidWorks/El Padre/Base_roulante/Base du robot/base_modifiee.SLDPRT
104.0 x 5.00 x 210.0 mm
