nsobczak/CoupeDeFrance/SolidWorks/El Padre/Base_roulante/Bloc moteur/dessouusinagevieux.SLDPRT

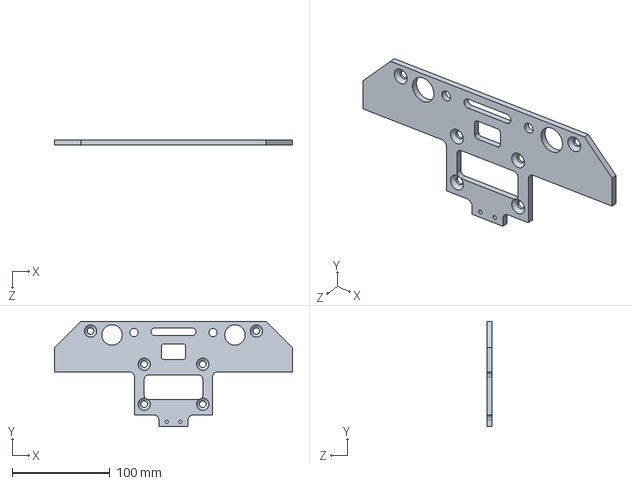
[picture p215: CAD file, 2017-02-13]
SolidWorks/El Padre/Base_roulante/Bloc moteur/dessouusinagevieux.SLDPRT
244.0 x 108.0 x 5.00 mm
