nsobczak/CoupeDeFrance/SolidWorks/El Padre/isen robot 2016-17/Tube lisse.SLDPRT

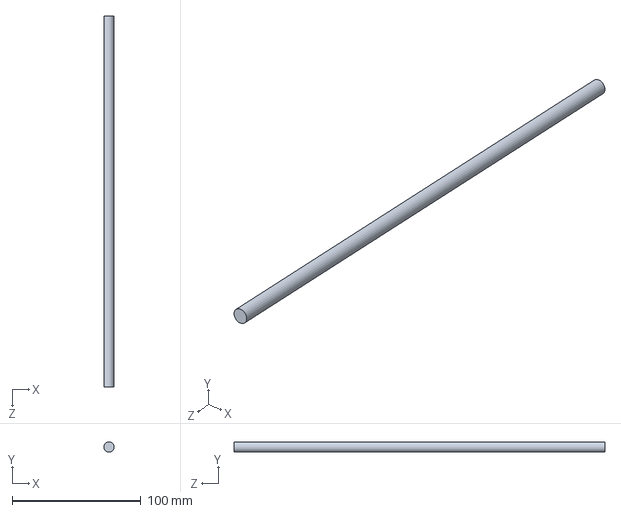
[picture p216: CAD file, 2017-02-13]
SolidWorks/El Padre/isen robot 2016-17/Tube lisse.SLDPRT
8.00 x 8.00 x 288.0 mm
