nsobczak/CoupeDeFrance/SolidWorks/El Padre/Base_roulante/Base du robot/Base_centre.SLDPRT

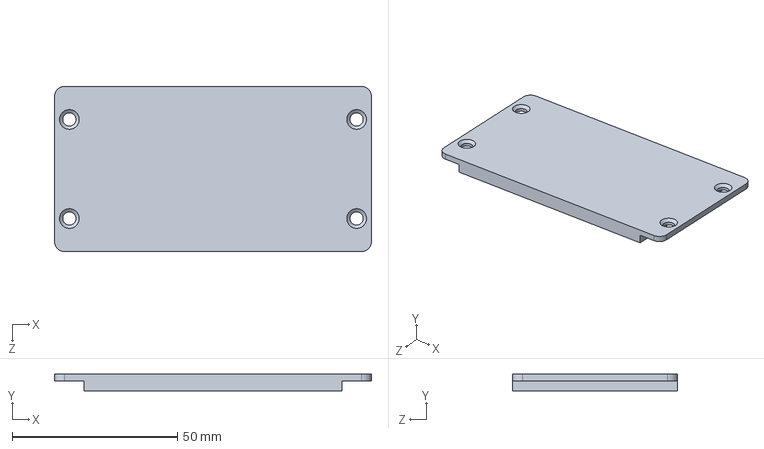
[picture p217: CAD file, 2017-02-13]
SolidWorks/El Padre/Base_roulante/Base du robot/Base_centre.SLDPRT
96.0 x 5.00 x 50.0 mm
