nsobczak/CoupeDeFrance/SolidWorks/El Padre/Base_roulante/Bloc moteur/batterie.SLDPRT

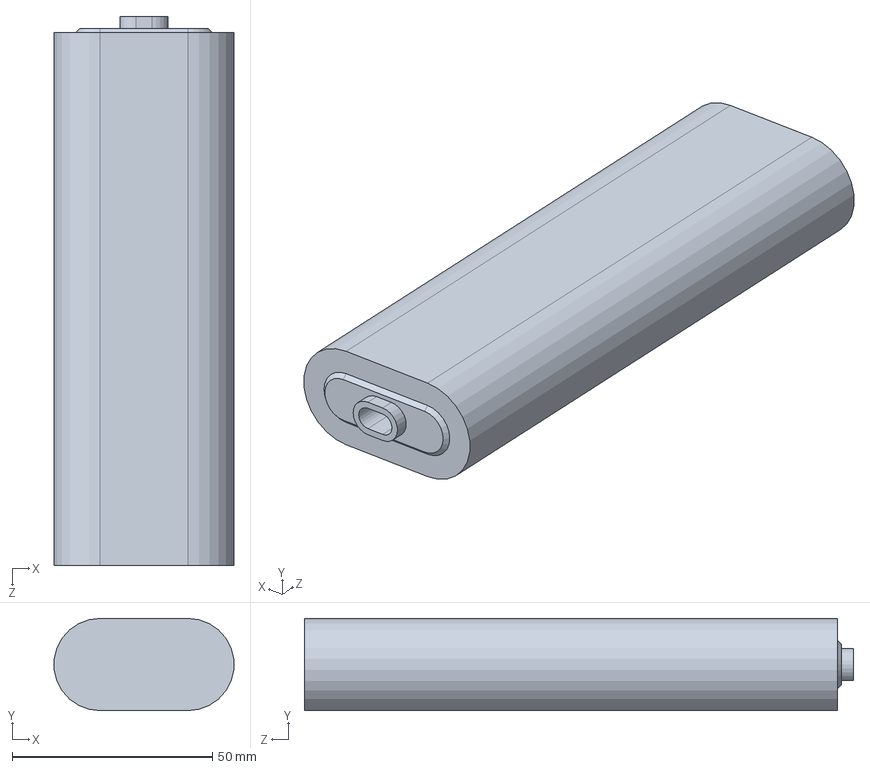
[picture p218: CAD file, 2017-02-13]
SolidWorks/El Padre/Base_roulante/Bloc moteur/batterie.SLDPRT
44.8 x 23.0 x 137.0 mm
