nsobczak/CoupeDeFrance/SolidWorks/El Padre/Base_roulante/cristeo/boule.SLDPRT

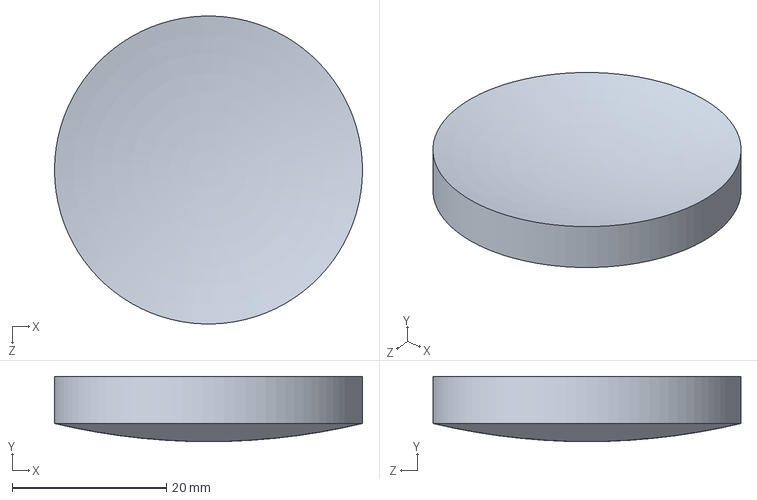
[picture p219: CAD file, 2017-03-29]
SolidWorks/El Padre/Base_roulante/cristeo/boule.SLDPRT
40.0 x 8.49 x 40.0 mm
