nsobczak/CoupeDeFrance/Module Moteur/Software/Tests/README.md

# Tests

## Test_I2C
Fichier pour tester que la communiocation I2C du robot fonctionne.

## TestDriver
Fichier pour tester que les drivers moteur du robot fonctionnent.

## TestEncodeurs
Fichier pour tester que les encodeurs du robot fonctionnent.
