nsobczak/CoupeDeFrance/Documentation/html/_ecran__test_8cpp__incl.png

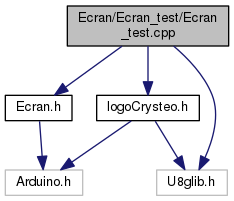
Documentation/html/_ecran__test_8cpp__incl.png
