nsobczak/CoupeDeFrance/Module Moteur/Software/Tests/TestDriver/TestDriver_Salon_etudiant/TestDriver_Salon_etudiant.ino

/**
 *    \file TestDriver_01.ino
 *    \brief test pour faire fonctionner les moteurs du robot et donc faire rouler le robot
 *
 *    \author Arthur Duytschaever
 *    \date Decembre 2016
 */
//_______________________________________________________________________________________________________
//_______________________________________________________________________________________________________
/* ======================================================================================================
 *      Variables globales
 * ======================================================================================================
 */
int MotorR =3; // Attention sur Due PWM ou Pwm sont des keyword -> donc ne pas les utiliser pour des nom de variable
int MotorL = 6; 
int IN1MotorL = 22;
int IN2MotorL = 23;
int IN1MotorR = 52;
int IN2MotorR = 53;
 
 
//_______________________________________________________________________________________________________
//_______________________________________________________________________________________________________
/**
 * \fn void setup()
 * \brief fonction setup d'arduino
 */
void setup() {
  pinMode(MotorR,OUTPUT);
  pinMode(MotorL,OUTPUT);
  pinMode(IN1MotorR,OUTPUT);
  pinMode(IN2MotorR,OUTPUT);
  pinMode(IN1MotorL,OUTPUT);
  pinMode(IN2MotorL,OUTPUT);
  //analogWriteResolution(8);// seulement sur Arduino Due pour gere la Resolution du convertisseur DAC 
  digitalWrite(IN1MotorR,LOW);
  digitalWrite(IN2MotorR,LOW);
  digitalWrite(IN1MotorL,LOW);
  digitalWrite(IN2MotorL,LOW);
  /*analogWrite(MotorR,255);
  analogWrite(MotorL,255);*/
}


/**
 * \fn void loop()
 * \brief fonction loop d'arduino
 */
void loop() {
  delay(5000);
  digitalWrite(IN1MotorR,LOW);
  digitalWrite(IN2MotorR,HIGH);
  digitalWrite(IN1MotorL,LOW);
  digitalWrite(IN2MotorL,HIGH);
  analogWrite(MotorR,0);
  analogWrite(MotorL,0);
  delay(1000);/*
  analogWrite(MotorR,255);
  analogWrite(MotorL,255);
  digitalWrite(IN1MotorR,LOW);
  digitalWrite(IN2MotorR,LOW);
  digitalWrite(IN1MotorL,LOW);
  digitalWrite(IN2MotorL,LOW);
  analogWrite(MotorR,255);
  analogWrite(MotorL,255);
  delay(700);
  analogWrite(MotorR,255);
  analogWrite(MotorL,255);
  digitalWrite(IN1MotorR,LOW);
  digitalWrite(IN2MotorR,HIGH);
  digitalWrite(IN1MotorL,LOW);
  digitalWrite(IN2MotorL,HIGH);
  analogWrite(MotorR,55);
  analogWrite(MotorL,55);
  delay(700);
  analogWrite(MotorR,255);
  analogWrite(MotorL,255);
  digitalWrite(IN1MotorR,LOW);
  digitalWrite(IN2MotorR,LOW);
  digitalWrite(IN1MotorL,LOW);
  digitalWrite(IN2MotorL,LOW);
  analogWrite(MotorR,255);
  analogWrite(MotorL,255);
  delay(700);*/
  
}
