nsobczak/CoupeDeFrance/Module Cerveau/I2C/Tests/Test04 - avec bibliothèque/slave_1/slave_1.ino

#include <Wire.h>
#include "i2cCommunication.h"

#define _SENDADRESS_ 5
#define _RECEIVEADRESS_ 6


//_____________________________________________________________________________________________
//_____________________________________________________________________________________________

int changeOrder(int order)
{
  order++;
  if (order==2)
  {
    order = 0;
  }
  return order;
}


//_____________________________________________________________________________________________
//_____________________________________________________________________________________________
void setup()
{
}

void loop()
{
  i2creceive(_RECEIVEADRESS_);
  delay(500);
}
