nsobczak/CoupeDeFrance/Module Cerveau/Artificial Intelligence/Ecran/Ecran_test/logoCrysteo.h

/**
 *    \file logoCrysteo.h
 *    \brief logoCrysteo
 *    \author Arthur Duytschaever
 *    \date octobre 2016
*/


/* ======================================================================================================
 *      Include
 * ======================================================================================================
 */
#include  "Arduino.h"
#include "U8glib.h"


/* ======================================================================================================
 *      Declaration
 * ======================================================================================================
 */
// creation avec U8GlibCreator
const uint8_t logoCrysteo[] U8G_PROGMEM = {
0x0,0x0,0x0,0x0,0x0,0x0,0x0,0x0,0x0,0x0,0x0,0x0,0x0,0x0,0x0,0x0,0x0,0x0,0x0,0x0,0x0,0x0,0x0,0x0,0x0,0x0,0x0,0x0,0x0,0x1f,0xe0,0x0,0x0,0x0,0x0,0x0,0x0,0x0,0x0,0x0,0x0,0x0,0x0,0x0,0x3,0xff,0xfe,0x0,0x0,0x0,0x0,0x0,0x0,0x0,0x0,0x0,0x0,0x0,0x0,0x1,0xff,0xff,0xff,0xc0,0x0,0x0,0x0,0x0,0x0,0x0,0x0,0x0,0x0,0x0,0x0,0x3f,0xff,0xff,0xff,0xf0,0x0,0x0,0x0,0x0,0x0,0x0,0x0,0x0,0x0,0x0,0x7,0xff,0xc0,0x0,0x7,0xf0,0x0,0x0,0x0,0x0,0x0,0x0,0x0,0x0,0x0,0x0,0x1f,0xfe,0x0,0x0,0x3,0xf8,0x0,0x0,0x0,0x0,0x0,0x0,0x0,0x0,0x0,0x1,0xff,0xc0,0x0,0x0,0x0,0xf8,
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
