nsobczak/CoupeDeFrance/Module Cerveau/Artificial Intelligence/Ecran/Ecran_test/logoCrysteo.cpp

/**
 *    \file logoCrysteo.cpp
 *    \brief logoCrysteo
 *    \author Arthur Duytschaever
 *    \date octobre 2016
*/


/* ======================================================================================================
 *      Include
 * ======================================================================================================
 */
 #include "logoCrysteo.h"
